pawaritmuangrach/ultrasonic01/CAR_PLAN.md

# แผนรถบังคับ — อัลตราซาวด์มองข้างหน้า

เป้าหมายปลายทาง: ติดอาเรย์อัลตราซาวด์บนรถบังคับ ให้รถ "เห็น" สิ่งกีดขวางข้างหน้า
แบบเรียลไทม์ โดยเทรน NN ด้วยกล้องเป็นครู เอกสารนี้ล็อกสถาปัตยกรรมที่ตัดสินแล้ว
และแทนแผน Stage 4-7 เดิมใน `.claude/plans/` ที่คิดไว้แบบตั้งโต๊ะ 9 ช่อง

Stage 1-2 (ยิงคลื่น + TDOA จริง sub-µs) เสร็จแล้ว ดู `README.md` §8

---

## สถาปัตยกรรมที่ล็อกแล้ว

| เรื่อง | เลือก | เพราะ |
|---|---|---|
| สมองรถ | **Raspberry Pi** (หรือคอมร่วม) | ESP32 เก็บคลื่นอย่างเดียว · Pi รัน NN + คุมมอเตอร์ · ยืดหยุ่นสุด |
| Ground truth | **Astra ติดบนรถ มองหน้า คู่กับอาเรย์** | กล้องเห็นสิ่งเดียวกับอัลตราซาวด์ = label ตรงกัน · ใช้ต่อจาก webcam project ได้เลย |
| เป้าหมายแรก | **egocentric — อะไรอยู่ข้างหน้าตอนนี้** | ทิศ+ระยะในกรวยหน้า ไม่ต้องรู้พิกัดรถ (global map ไว้ทีหลัง) |
| การเก็บข้อมูล | **พร้อมกันทุกช่อง** | รถเคลื่อนที่ → จับคู่ตามลำดับเบลอ (§8.17) |

## คุณค่าหลัก — อัลตราซาวด์เติมจุดบอดกล้อง

Astra เป็น structured light อ่านไม่ได้ในหลายกรณี (จาก webcam project README):
กระจก/แก้ว/พลาสติกใส · ผิวมันสะท้อน · จอมอนิเตอร์ · โดนแดด · **ใกล้กว่า 0.6 m**

จุดที่กล้องบอดคือจุดที่อัลตราซาวด์แข็งแรง โดยเฉพาะ <0.6 m ซึ่งเป็นระยะอันตรายที่สุด
ของรถ **กล้องเป็นครูตอนเทรน อัลตราซาวด์ทำงานตอนกล้องมองไม่เห็น** นี่คือเหตุผลของทั้งโปรเจกต์

## ตัวเลขจริงที่กำหนดขอบเขต (วัด/คำนวณแล้ว)

| | ค่า | ที่มา |
|---|---|---|
| มุมมอง | กรวยหน้า ~60° | ลำเสียง TCT40 |
| ระยะใช้ได้ | กำแพง ~2 m · ของเล็ก ~3 m · **ไม่ถึง 5-10 m** | SNR 40 dB ที่ 0.42 m + ดูดกลืน 1.2 dB/m |
| อัตราปิง | 30-50 ปิง/วิ ที่ 2-3 m | เวลาเอคโค่ไป-กลับ |
| รถขยับต่อปิง | 17-33 mm ที่ช้า | ละเอียดพอ |
| ADC หนึ่ง ESP32 | **2 ช่องพร้อมกันที่ 266 kS/s** | §8.17 (3+ ช่องยุบเหลือ 44-89 kS/s) |
| คอขวดส่งดิบ | 6-11 Mbps ที่ 30 ปิง/วิ | ดิบ 4 ช่อง — เกิน serial |

**คอขวดส่งดิบ**: เก็บ dataset ออฟไลน์ส่งช้าๆ ได้ ไม่มีปัญหา · deploy realtime ต้อง
ประมวลบน ESP32 แล้วส่งแค่ feature (Δt ต่อคู่ + envelope ย่อ) ไม่ใช่ดิบ

---

## แผ่นอาเรย์ที่ปริ้นไว้ — ใช้ตัวเดิมยาว ไม่ต้องปริ้นใหม่จนถึง Stage D

แผ่น Y-array เจาะรูเผื่อ 9 RX + 3 TX ไว้แล้ว เราใช้ทีละไม่กี่รู ไม่ต้องแก้อะไร

| Stage | ทำกับแผ่นอาเรย์ |
|---|---|
| A (2 ช่อง) | ไม่แตะ — T1 + A140 + C140 เสียบอยู่แล้ว |
| B (4 ช่อง) | แผ่นเดิม **เพิ่มหัวรับลงรู A80, C80** |
| C (ขึ้นรถ) | แผ่นเดิม + แผ่นยึดให้ติดรถได้ |
| D+ (9 ช่อง) | ค่อยตัดสินว่าปริ้นใหม่ไหม |

**4 ช่องของ Stage B เลือก A80, A140, C80, C140** (หมุนแผ่นให้ A140-C140 วางนอน =
แกนซ้าย-ขวาของรถ) ได้เบสไลน์แนวนอนสองขนาด: A140-C140 (242 mm, ทิศละเอียด) และ
A80-C80 (139 mm, ทิศหยาบไม่กำกวม) = coarse-to-fine แก้ปัญหาข้ามคาบ · TX คงที่ T1

**ของใหม่ชิ้นเดียวสำหรับ Stage A ไม่ใช่อาเรย์ แต่คือแผ่นยึดกล้อง+อาเรย์** ให้ Astra กับ
อาเรย์มองทางเดียวกันและไม่ขยับระหว่างเก็บ dataset (ไม้/อะคริลิก/พลาสวูดก็พอ ไม่ต้องแม่นมาก
NN เรียนความสัมพันธ์เอง แต่ต้องนิ่ง)

**ทำไม D+ ค่อยคิดเรื่องปริ้นใหม่** Y-array ออกแบบมาสำหรับ DOA 2 มิติบนโต๊ะ (สมมาตรทุกทิศ)
แต่รถมองหน้าอย่างเดียว เน้นซ้าย-ขวา อาจได้ประโยชน์จากอาเรย์เตี้ยกว้างและเล็กลง (ตอนนี้ 280 mm
ใหญ่สำหรับรถเล็ก) **ผล 4 ช่องจะบอกเองว่าต้องการเบสไลน์แบบไหนเพิ่ม** ออกแบบจากข้อมูลจริง
ไม่ใช่เดา

## แผน Stage ใหม่

### Stage A — ไปป์ไลน์ครบวงจร ด้วย 2 ช่องที่มีอยู่  ✅ เสร็จ (ไปป์ไลน์ครบเส้น · ระยะเรียนได้)

พิสูจน์ loop ทั้งเส้นก่อนสร้างฮาร์ดแวร์เพิ่ม **ทำบนคอมเครื่องนี้ได้เลย ไม่ต้องมี Pi
และไม่ต้องมีรถ** (Astra + OpenNI2 ติดตั้งแล้วจาก webcam project) ไม่ต้องซื้ออะไร

> **ไม่ต้องมีรถจนถึง Stage C** หนึ่งตัวอย่างเทรน = สแนปช็อตเดียวของ (คลื่น + depth)
> ณ ขณะเดียว รถไม่เกี่ยว เก็บด้วยการยึด **อาเรย์ + Astra ติดกันบนแท่น/ขาตั้งเดียว**
> หันทางเดียวกัน แล้วเลื่อนวัตถุ/ยกแท่นไปฉากต่างๆ ด้วยมือ เพราะเก็บพร้อมกันทุกช่องแล้ว
> สแนปช็อตจากแท่นนิ่งกับจากรถวิ่งจึงเหมือนกัน (Doppler ที่ 1 m/s = 0.3% ทิ้งได้)
> **ของชิ้นเดียวที่ต้องทำเพิ่มคือแผ่นยึดกล้อง+อาเรย์ให้มองสิ่งเดียวกัน** ไม่ใช่รถ

1. ตัวเก็บ dataset: อ่านอัลตราซาวด์ 2 ช่อง (ไปป์ไลน์ §8 ที่พิสูจน์แล้ว) + Astra depth
   พร้อม timestamp ให้ตรงกัน
2. เก็บชุดเล็ก: วางสิ่งกีดขวางหลายตำแหน่ง/หลายระยะในกรวยหน้า เก็บคู่ (คลื่น, depth)
3. เทรน NN จิ๋ว: คลื่น 2 ช่อง → ระยะ+ทิศของสิ่งที่อยู่ข้างหน้า (label จาก Astra)
4. **เกณฑ์ผ่าน**: NN ทำนายระยะ/ทิศได้ดีกว่าเดา และทำงานในจุดที่ Astra บอด (เอาวัตถุ
   ใกล้กว่า 0.6 m หรือกระจก มาลอง — กล้องได้ 0 แต่อัลตราซาวด์ยังเห็น)

### Stage A — ผลสรุป (2 ช่อง)

ไปป์ไลน์ครบเส้นทำงานแล้ว: เก็บ (คลื่น+depth) → สกัด feature → เทรน → วัดผลเทียบ baseline
โค้ดอยู่ใน `car/` (collect, astra, ultrasonic, features, labels, train, inspect_data)

**บทเรียนสำคัญที่วัดได้:**

| แกน | 2 ช่องทำได้ไหม | เพราะ |
|---|---|---|
| **ระยะ** | ✅ ได้ (r 0.5-0.9) | มาจากเวลาเอคโค่ตรงๆ ไม่ต้องเทียบสองช่อง `--track` พิสูจน์แล้ว 74→87, 102→117, 133→143 cm |
| **มุม** | ❌ ไม่ได้ (r~0) ตอนนั้น | **[แก้ทีหลัง]** สรุปตอนนั้นว่า "ต้องหลายเบสไลน์" — **ผิด** Stage B พบว่าเหตุจริงคือ (1) ช่อง g34 เสีย (Rf2 ผิดรู amp ต่ำ 3 เท่า) (2) อาเรย์วางบนพื้นกระเบื้องที่สะท้อน 40 kHz · พอแก้สองข้อนี้ **เบสไลน์เดียวก็วัดมุมได้** (9.4°) |

**กับดักที่เจอ (มีค่าต่อรถ):** อัลตราซาวด์เห็น "เสียงที่ดังที่สุด" ไม่ใช่ "สิ่งที่ใกล้ที่สุด"
ผนังเรียบไกล 2.4 m ดังกว่ากล่องเล็กที่ 0.8 m ทำให้ us ล็อกผนัง ไม่ใช่วัตถุ →
เพิ่มโหมด `--track` เช็คว่าวัตถุเป็นเสียงเด่นก่อนเก็บ และต้องเก็บในที่โล่ง

### Stage B — ขยายเป็น 4 ช่อง (ยังไม่ใช่ 9)  ⟵ อยู่ตรงนี้

**ฮาร์ดแวร์: ✅ เสร็จ · ระยะ+มุม: ✅ เรียนได้ทั้งคู่ · เหลือ: เก็บ dataset ชุดใหญ่ให้แม่นขึ้น**

รายละเอียดการวัดทั้งหมดอยู่ที่ [`README.md` §8.18](README.md) · ตรงนี้เก็บเฉพาะข้อสรุป

#### สถานะช่อง (วัดด้วย `collect.py --track` เป้าท่อ PVC ที่ ~80 cm)

| ช่อง | หัวรับ | เบสไลน์ | amp | |
|---|---|---|---|---|
| GPIO35 | A140 | คู่ 242 mm | 50 | ✅ |
| GPIO34 | C140 | | 81 | ✅ (เคย 17 — Rf2 เสียบผิดรู) |
| GPIO32 | A80 | คู่ 139 mm | 89 | ✅ |
| GPIO33 | C80 | | 107 | ✅ |

#### ผลการเรียนรู้ (แบ่ง train/val ตามฉาก ซื่อสัตย์)

**ชุดใหญ่ 790 ตัวอย่าง 6 ระยะ (e60-e160 ห่างละ 20 cm) หมุนทดสอบทีละฉาก:**

| | ระยะ | มุม |
|---|---|---|
| เดาค่าเฉลี่ย (baseline) | 36.3 cm | 14.8° |
| โมเดลเทรน | 13.6 cm ✓ | **11.8° ✓** |
| **ฟิสิกส์ตรงๆ (ไม่เทรน)** | **7.3 cm ✓** | — |

มุมดีที่ระยะใกล้ แย่ลงตามระยะ: **8.1° ที่ 53 cm** → 13.8° ที่ 154 cm (SNR ตก)
— ตรงกับที่รถต้องการพอดี เพราะระยะใกล้คือระยะอันตราย

> **ต้องหมุนทดสอบทีละฉาก อย่ากันฉากกลางฉากเดียว** ถ้าเก็บระยะห่างเท่าๆ กัน ค่าเฉลี่ยของ
> ฉากที่เหลือจะตรงกับฉากกลางพอดี baseline เลยแม่นเอง (ได้ 1.4 cm) ชนะยังไงก็ไม่ได้ =
> วัดผลหลอกตัวเอง

#### สี่บทเรียนที่เปลี่ยนผลจริง

1. **สภาพแวดล้อมสำคัญกว่าวงจร** — พื้นกระเบื้องสะท้อน 40 kHz กลบเป้าจนข้อมูล 3 ชุดแรก
   ใช้ไม่ได้ · ยกอาเรย์+เป้าพ้นพื้น ~50 cm และใช้**ทรงกระบอกตั้ง** (สะท้อนกลับทุกมุม
   ผลักตรงๆ ได้) แทนแผ่นเรียบ (ต้องเอียงหาเซนเซอร์ทุกตำแหน่ง ไม่งั้นเด้งหลุด)
2. **ช่องอ่อน = ฉีดสัญญาณวัดทีละสเตจ อย่าเดาแล้วเปลี่ยนของ** เดาผิดสองรอบ (หัวรับ/
   เรโซแนนซ์) เสียเวลา · ลองหัว 3 ตัว amp ไม่ขยับ = ตัดหัวออก แล้วยิงโทน 40 kHz วัดทีละ
   สเตจ เจอทันทีว่าสเตจ 2 ให้เกน ×2.3 แทน ×11
3. **T0 ผิด = bias คงที่ +13 cm** คาลิเบรตกับกล้อง 435 → 1220 µs แล้ว US ตรงกับกล้อง
   78% → 93%, MAE 20 → 9.7 cm · เพิ่ม range gate 40-250 cm กัน argmax เกาะเสียงสะท้อนใกล้
   ซึ่ง**ทำให้มุมพังไปด้วย** เพราะหน้าต่าง TDOA อิงยอดนี้
4. **แยก feature ตามเป้า** ระยะใช้เวลาเอคโค่ (8 มิติ) · มุมใช้ TDOA (6 มิติ) — รวมกัน 518 มิติ
   ทำให้ทำนายแย่กว่าเดาค่าเฉลี่ย (−134%) เพราะต่างฝ่ายเป็น noise ของอีกฝ่าย
5. **label กำกวมจากขาคนเก็บ** ขาที่ระยะพอๆ เป้าทำให้กล้องเลเบลขาแทนเป้า (`--expect-cm`
   กรองแค่ระยะจับไม่ได้) · `near_object_count>1` ข้ามเฟรมที่มีของใกล้หลายจุด — e60/d130 ติด
   27-32% แต่ตอนเก็บด้วย `--manual` เดินออกสุดติดแค่ 1-2% · train.py กรองอัตโนมัติแล้ว
6. **ช่องบนบอร์ดทดลองแผ่นที่สองมีพื้นเสียงสูงกว่า 3 เท่า** ยอดปลอมสูงกว่า 4 เท่า →
   argmax ไปเกาะยอดปลอม จับเป้าถูกแค่ 27-51% ที่ระยะ >90 cm ขณะที่ ch0 ได้ 89-100%
   **[แก้: ตอนแรกสรุปว่าเป็นเพราะสายจั๊มยาว — ผิด เปลี่ยนสายสั้นแล้วพื้นเสียงเท่าเดิม
   (9.0 → 9.0)]** เหตุผลเชิงวงจรที่ควรคิดตั้งแต่แรก: ขาออกออปแอมป์อิมพีแดนซ์ต่ำ (2.2k)
   รับ noise ยาก และ noise ที่เข้าหลังภาคขยายไม่ถูกขยายต่อ — จุดที่ไวคือ *ขาเข้า* ไม่ใช่ขาออก
   · สาเหตุจริงไล่ตัดจนเหลือ "ตัวบอร์ดทดลองเอง" (ดูตารางด้านล่าง)
7. **ใช้ "ยอดร่วม" ไม่ใช่ให้แต่ละช่องหายอดเอง** เป้าอยู่ระยะเดียว ทุกช่องจึงควรอ่านที่หน้าต่าง
   เดียวกัน — เลือกช่องที่พื้นเสียงต่ำสุดเป็นตัวชี้ยอด (`features.common_peak`) →
   **ระยะ MAE 20.6 → 7.3 cm (ถูก 57% → 94%) และมุมดีขึ้นเป็น 11.8°** เพราะหน้าต่าง TDOA
   ของคู่ที่สองเดิมอิงยอดของ ch2 ซึ่งเป็นช่องที่รบกวนสูงสุด

#### ข้อสรุปเชิงออกแบบ

> **ระยะคำนวณจากฟิสิกส์ (9.7 cm แม่นกว่าเทรน 16.7 cm) — ML มีไว้ทำ "มุม" และการแยกวัตถุ**

> **เบสไลน์ยาว (242 mm) คือตัวทำงาน** corr(มุม,TDOA) = +0.64 เทียบ 139 mm ที่ได้ −0.09 ·
> ที่กลัวว่าเบสไลน์ยาวจะกำกวมข้ามคาบ **ไม่เกิด เพราะเราหา TDOA จากเอนเวโลปไม่ใช่เฟสพาหะ
> จึงไม่มีคาบให้กำกวม** · เบสไลน์สั้นจะมีประโยชน์ตอนเปลี่ยนไปใช้เฟสพาหะเท่านั้น

#### ไล่ noise บอร์ด 2 จนจบ แล้วตัดสินใจย้ายลงไข่ปลา (ส.ค. 2026)

ช่องบนบอร์ดทดลองแผ่นที่สอง (g32/g33) พื้นเสียงสูงกว่าแผ่นแรก ~3 เท่า ทำให้ argmax ไปเกาะ
"ยอดปลอม" — จับเป้าถูกแค่ 27-51% ที่ระยะ >90 cm ขณะที่ g34 ได้ 89-100%

**ตัดผู้ต้องสงสัยออกทีละข้อด้วยการวัด** (เครื่องมือ `tools/noise_check.py` เก็บรายการไว้กันไล่ซ้ำ):

| สมมุติฐาน | วิธีตัด | ผล |
|---|---|---|
| สายจั๊มยาว | เปลี่ยนสายให้สั้น | เท่าเดิม (9.0 → 9.0) ❌ |
| คลื่นจากตัวส่ง | ปิดการยิง TX | เท่าเดิม (10.2 → 9.5) ❌ |
| EMI ความถี่เฉพาะ | ดูสเปกตรัม | แบนเรียบ สูงกว่า 3-4 เท่าทุกย่าน 0-133 kHz ❌ |
| หัวรับ/สายหัวรับ | ถอดหัวรับออก | noise **สูงขึ้น** (อินพุตลอย = เสาอากาศ) ❌ |
| ไฟ/VREF ที่ยืมข้ามบอร์ด | ดูสหสัมพันธ์ 2 ช่อง | corr −0.009 = ไม่ใช่แหล่งร่วม ❌ |
| ขา ADC ของ ESP32 | สลับสายที่ ESP32 | noise ตามวงจรไป ไม่ตามขา ❌ |
| ตัวชิป | เปลี่ยน MCP6004 ตัวใหม่ | เท่าเดิม ❌ |
| ค่าตัวต้านทาน | วัดด้วยมัลติมิเตอร์ | ตรงหมด ❌ |

> **เมื่อทุกชิ้นส่วนถูกหมดแต่ noise ยังอยู่ ผู้ต้องสงสัยที่เหลือคือ "ตัวบอร์ดทดลองเอง"**
> หน้าสัมผัสสปริงที่ต้านทานไม่คงที่ + ความจุแฝงระหว่างรางติดกัน — เปลี่ยนอะไหล่แก้ไม่ได้

**แก้ด้วยซอฟต์แวร์ไปก่อนแล้ว**: `features.common_peak` ใช้ยอดเอคโค่จาก "ช่องที่เงียบที่สุด"
เป็นหน้าต่างร่วมของทุกช่อง แทนที่จะให้แต่ละช่อง argmax เอง → **ระยะ MAE 20.6 → 7.3 cm
(ถูก 57% → 94%)** และมุมดีขึ้นเป็น 11.8°

**ตัดสินใจย้ายลงแผ่นไข่ปลา — เร็วกว่าแผนเดิม (เดิมไว้ Stage C)** เพราะแก้ 4 เรื่องพร้อมกัน:
พื้นที่ (บอร์ดทดลองเต็มแล้ว ขยายไม่ได้อีก) · noise (ผู้ต้องสงสัยที่เหลือ) · ความแมตช์ของช่อง
(บัดกรีเลย์เอาต์เดียวกันเป๊ะทุกช่อง = ปรสิตเท่ากัน) · พร้อมขึ้นรถ (รถสั่น ต้องบัดกรีอยู่แล้ว)

**ผังบัดกรีทำแล้ว 4 แผ่น** `hardware/perf_rx_layout.py` → `diagrams/perf_1..4_*.svg`
วาดตรงกับแผ่นจริง (คอลัมน์ A อยู่ขวา · เลขแถว 048 อยู่บน · ทุกรูแยกอิสระ วัดยืนยันแล้ว)
รวมวงจร VREF ที่ต้องสร้างเองบนแผ่น (ตัวแบ่ง + บัฟเฟอร์ section C) ซึ่งผังชุดแรกตกไป

**แผนแผ่น**: 9 ช่องใช้ 5 ชิป — ชิปแรก = ช่อง 1 + บัฟเฟอร์ VREF · ที่เหลือ 2 ช่อง/ชิป
**ทำช่องแรกก่อนช่องเดียว แล้ววัดเทียบทันที** ถ้าพื้นเสียงลงมาใกล้ 3-4 = ยืนยันว่าบอร์ดทดลอง
คือต้นเหตุจริง ค่อยลุยที่เหลือ (หลักเปลี่ยนทีละอย่าง แบบเดียวกับที่จับบั๊ก g34 ได้)

**MCP6024 ใช้ตอนไหน**: ใช้ซ็อกเก็ตทุกตัว จึงเปลี่ยนรุ่นทีหลังฟรี → **ช่องทดสอบใช้ MCP6004
ก่อน** (เพื่อให้เทียบกับบอร์ดทดลองได้สะอาด เปลี่ยนแค่ชนิดบอร์ดอย่างเดียว) แล้วค่อยสลับเป็น
**MCP6024 ทั้ง 5 ตัวพร้อมกัน** ตอนทำช่องที่เหลือ · เหตุผลเชิงวงจร: ที่เกน 11/สเตจ MCP6004
(GBW 1 MHz) ได้ BW 91 kHz ทำให้ 40 kHz อยู่ที่ 0.44 ของความถี่ตัด **เฟสเลื่อนตาม GBW
ของชิปแต่ละตัว = error ของ Δt ระหว่างช่อง** ส่วน MCP6024 (10 MHz) ได้ 909 kHz เฟสแทบไม่เลื่อน
(รายละเอียด `hardware/rx_frontend.md` 8.5)

#### ความคืบหน้าไข่ปลา (ล่าสุด)

| | สถานะ |
|---|---|
| ผัง 4 แผ่น | ✅ เสร็จ ตรงกับแผ่นจริง (A ขวา · แถว 048 บน) + มีตัวตรวจเส้นทับอัตโนมัติ |
| คอนเนคเตอร์ | ✅ TB1 = KF301 ไฟเข้า · H1 หัวรับ · H2 VREF ออก · H3 ไป ESP32 |
| **ESP32 ตัวที่ 2** | ✅ **แฟลช `esp32_scope` แล้ว (COM6)** ใช้กับแผ่นไข่ปลา — **ตัวเดิมคาไว้กับบอร์ดทดลอง อย่ารื้อ** เก็บไว้เทียบ noise |
| ผัง 1 (บัส+ซ็อกเก็ต) | ✅ **ผ่านครบ** · บัสไม่ช็อตกัน · ขา 4 (L33) = 3.35V · ขา 11 (O33) = 0V · บัส 3V3 = 3.35V · บัส GND = 0V — พร้อมเสียบชิป |
| ผัง 2 (VREF 1.65V) | ✅ **ผ่าน** · บัฟเฟอร์ทำงาน U30=1.60V ≈ F37=1.59V (1.59 เพราะ R ±5% — ไม่มีผล ทุกช่องดึงจากบัสเดียว) |
| ผัง 3+4 (สเตจ 1-2) | ✅ **ผ่าน DC ครบ** · H3 ขาออก = 1.611V เทียบ VREF 1.612V (ต่าง 1 mV) = ไบอาสถูกตลอด ขา 3→1→5→7→R_out |

**บทเรียนเครื่องมือ**: ESP32 อ่านได้ 0-3.3V และ**ชนเพดานที่ 3.3V พอดี** จึงไม่เหมาะวัดไฟเลี้ยง —
ใช้มัลติมิเตอร์กับผัง 1 · ESP32 เหมาะกับผัง 2 เป็นต้นไป (VREF 1.65V อยู่กลางพิสัย อ่านแม่น
และฉีดโทนวัดเกนรายสเตจได้)

**บทเรียนไล่จุดเสียบนไข่ปลา (ส.ค. 2026 — เสียเวลาหลายชั่วโมง)**

| อาการ | ความหมาย |
|---|---|
| โหนดตัวแบ่งอ่านได้ 0V ทั้งที่หัวบนมี 3.3V และขาล่างวัดได้ 10k | **มีอะไรลากโหนดลง GND** — ตรรกะบังคับ: ตัวแบ่งที่ครบวงจรอ่าน 0V ไม่ได้ |
| วัดโอห์มได้ **หลักร้อย** (150Ω) ไม่ใช่ 0Ω | **ไม่ใช่ตะกั่วช็อตเต็ม** — เป็นการแตะไม่เต็มที่/คราบฟลักซ์ที่ไหม้ (นำไฟได้ 100Ω–kΩ) |
| **ต้นเหตุจริง** | สายที่ต่อ **ขา 10** ล้นไปแตะแพด **ขา 11 (GND)** ที่อยู่ติดกันบนซ็อกเก็ต |

**บั๊กผังที่เจอระหว่างประกอบ (แก้แล้วทั้งหมด + มีตัวตรวจอัตโนมัติ)**

| # | บั๊ก | ผลที่เกิด |
|---|---|---|
| 1 | สายเข้าขาชิปวาดพาดทับตัวชิป จุดต่อถูกบัง | ต่อผิดไปขา 14 (OUTD) แทนขา 10 |
| 2 | ผัง 3 เดินสายลงคอลัมน์ F ซึ่งเป็นโหนด VREF ของผัง 2 (ผังนั้นไม่ได้วาดไว้ จึงดูว่าง) | สายพาดโหนด VREF · มุมหักลงรู GND |
| 3 | ผัง 1 บอกความยาวบัสแค่แถว 41-26 แต่ผัง 3 ใช้ถึง 44 ผัง 4 ถึง 21 | จุด GND ของผัง 4 ไม่ต่อบัส |
| 4 | ผัง 4 มีสายคนละโหนด 2 เส้นวิ่งคอลัมน์ K ห่างกัน **1 แถว** | มองเป็นเส้นเดียว → ขา 1/5/6 ถึงกันหมด → สเตจ 2 อิ่มตัว 3.34V |
| 5 | ป้ายชื่อชิปทับเส้นสายขา 7 | ขา 7 ดูเหมือนไม่ได้ต่ออะไร |

**ตัวตรวจที่เพิ่มใน `perf_panel.py`** (รันทุกครั้งที่สร้างผัง): เส้นทับกัน · **สองท่อนคนละเส้นเรียงต่อกันโดยเว้น ≤ 2 แถว** · และ `ghosts()` วาดวงประแดงบอก "รูที่ผังอื่นจองไว้แล้ว" ทุกผัง เพราะแผ่นเดียวกันแต่แยกวาด 4 ผัง

**กฎที่ได้:**
- แพดที่ติดกับขา GND/VDD ของชิป = จุดเสี่ยงช็อตที่สุด ใช้ตะกั่วน้อย ๆ และวัด `แพดนั้น ↔ GND ต้อง OL` ก่อนเสมอ
- **วัดโอห์มต้องปิดไฟเสมอ** — วัดตอนเปิดไฟได้ค่ามั่ว (เคยหลงว่าช็อตทั้งที่ไม่ช็อต)
- **วัดคาวงจรให้ค่าหลอก** (Rv1 อ่านได้ 1.5k/6k ทั้งที่เป็น 10k) จะฟันธงค่าอุปกรณ์ต้องปลดขาออกวัด
- **ESP32 ADC ใช้วัด DC แม่น ๆ ไม่ได้** — จุดเดียวกันอ่านได้ 2.055V แล้ว 1.413V ขณะมัลติมิเตอร์ได้ 1.70V ใช้ ESP32 เฉพาะงาน **AC/เทียบเกน** · ใช้มัลติมิเตอร์กับ DC
- **ขาลอยที่ต่อเข้า ADC อ่านได้ ~0.1–0.8V พร้อม noise สูง** — อย่าตีความว่าเป็นค่าจริงของวงจร (หลงมาแล้วตอนวัดบัส VREF ขณะถอดชิป ซึ่งไม่มีอะไรขับบัสเลย)

**บทเรียนผังไข่ปลา (ผัง 2)**: อาการโหนดถูกดึงลง 0 เมื่อเสียบชิป = สายอินพุต (+) ไปลง **ขา 14 (OUTD ที่ไม่ได้ใช้)** แทนขา 10 — OUTD อินพุตลอย เหวี่ยงเอาต์พุตชนขอบล่าง ลากโหนดตาม · **ต้นเหตุคือผังเรนเดอร์สายเข้าขา 10 โดยดิ่งลงทะลุตัวชิปจากด้านบน จุดต่อเลยถูกตัวชิปบัง** ผู้ใช้จึงบัดกรีผิดขา → **กฎใหม่: ผังไข่ปลา สายที่ต่อขาชิปต้อง 'โผล่ออกทางขอบชิป' ให้เห็นชัด ห้ามเดินเข้าหาขาโดยพาดผ่าน/ทับตัวชิป** (แก้ใน perf_rx_layout.py แล้ว)

#### ผลตัดสิน: ไข่ปลา vs บอร์ดทดลอง (ส.ค. 2026)

วัดด้วย ADC ตัวเดียวกัน วินาทีเดียวกัน หัวรับบนแท่น 3D ทั้งคู่ (`--pins 34,36 --samples 12000`)

| | ไม่ยิง TX | ยิง TX | crest | **ยอดปลอม** |
|---|---|---|---|---|
| บอร์ดทดลอง g34 | 3.0 | 13.1 | 12.8 | 167.0 |
| **ไข่ปลา g36** | 4.5 | **11.5** | **5.3** | **61.1** |

**สรุป: ไข่ปลาชนะในตัวชี้วัดที่สำคัญที่สุด** — ยอดปลอมน้อยกว่า 2.7 เท่า และ crest ต่ำกว่า 2.4 เท่า
(ยอดปลอมคือตัวที่ไปชนะเอคโค่จริงตอน argmax ทำให้อ่านระยะผิดทั้งที่ amp ดูปกติ)
พื้นเสียงตอนไม่ยิง TX สูงกว่าเล็กน้อย 1.5 เท่า ซึ่งอยู่ในเกณฑ์ที่ยอมรับได้ **-> เดินหน้าสร้างช่อง 2-9**

**บทเรียนที่ใหญ่ที่สุดของ Stage B**: ต่อสายกราวด์ตรงจาก H3 ขา GND ไป GND ของ ESP32 ที่อ่าน
ทำให้พื้นเสียงลดจาก 14.9 เหลือ **4.5 (3.3 เท่า)** — มากกว่าทุกอย่างที่เคยลองมาตลอดโปรเจกต์
สายสัญญาณทุกเส้นต้องมีสายกราวด์คู่เดินเคียงเสมอ (บิดเกลียวยิ่งดี) และ**เครื่องวัดเองก็เติม noise**
ช่องเดียวกันอ่านด้วย ESP32 คนละตัวได้ 24.0 กับ 14.9 -> เทียบวงจรต้องใช้ ADC ตัวเดียวกัน

#### เหลือทำใน Stage B

- เก็บ dataset ชุดใหญ่ 6 ระยะ ห่างละ 20 cm (ดู "ขั้นถัดไปทันที" ท้ายเอกสาร)
- **เกณฑ์ผ่าน**: มุมแม่นขึ้นจาก 14° ตอนทดสอบข้ามระยะ และระยะยังอยู่ระดับ ~10 cm

> ~~**ทางลัด: ไม่ต้อง master/slave** ฉากนิ่งตอนเก็บ จึงยิงสองครั้งอ่านทีละคู่ได้~~
> **เลิกใช้แล้ว (ส.ค. 2026) — ดู Stage B2** ทางลัดนี้ใช้ได้เฉพาะตอนฉากนิ่ง พอเปลี่ยนมา
> อัดต่อเนื่องกับเป้าที่เคลื่อนที่ มันพังทันที: สองรอบยิงห่างกัน ~95 ms คนเดิน 0.5 m/s
> ขยับไป 9.5 cm ซึ่งเกินหน้าต่างวิเคราะห์ (±5 cm) -> **คู่ที่สองพลาดเอคโค่โดยไม่มีอะไรเตือน**
> ตอนนี้อ่าน 4 ช่องพร้อมกันใน ESP32 ตัวเดียวด้วย bandpass sampling แทน (`car/sync4.py`)
> **master/slave ยังมีประโยชน์อยู่** ถ้าอยากได้ 266 kHz/ช่องเต็มพร้อมกันทั้ง 4 — เลื่อนไป Stage C

**1 TX + 4 RX ไม่ใช่ 3 TX + 9 RX** ขยายทีละขั้น 2→4 เพื่อให้แต่ละขั้นเป็นจุดจับปัญหา
(เหมือนที่ 2→3 ช่องทำให้เจอเพดาน ADC) กระโดดไป 9 เลยคือทำผิดซ้ำแบบสร้างใหญ่ก่อนพิสูจน์
9 RX / 3 TX เต็มรูปไว้ Stage D+ และตอนนั้นใช้ ADC ภายนอก ไม่ใช่ breadboard

- **ต่อ A80/C80 บนบอร์ดทดลองก่อน (ไม่ใช่ไข่ปลา) สำหรับทดสอบบนโต๊ะ** เพราะผู้ใช้เพิ่ง
  เคยใช้ไข่ปลาครั้งแรก การบัดกรีไข่ปลาครั้งแรก + เพิ่มช่อง พร้อมกัน = สองตัวแปร ถ้าไม่เวิร์ก
  แยกไม่ออกว่าบัดกรีพลาดหรือแนวคิดผิด — เปลี่ยนทีละอย่าง ต่อแบบเดิมที่คล่องแล้ว เสี่ยงต่ำ
  - A80 → GPIO32 · C80 → GPIO33 · ต่อเหมือน 2 ช่องเดิมเป๊ะ
- **ย้ายลงแผ่นไข่ปลาที่ Stage C (ตอนขึ้นรถ)** เมื่อแนวคิดพิสูจน์แล้วและรถสั่นจริงต้องบัดกรีอยู่ดี
  ตอนนั้นฝึกไข่ปลากับวงจรที่รู้ว่าถูกแล้ว ไม่ต้องเดาว่าปัญหาอยู่ไหน · ใส่ MCP6024 + IC socket
  ตอนนั้น · วางเลย์เอาต์ช่องละก้อนเหมือนกันเพื่อให้ปรสิตเท่ากัน (แมตช์ดีกว่า breadboard)
- TX กับ ESP32 ยังอยู่ breadboard/socket ได้ ยังไม่ต้องบัดกรี
- เฟิร์มแวร์ master/slave: ESP32 สองตัวยิง+เก็บพร้อมกัน ซิงก์ด้วยสายทริกเกอร์ร่วม +
  พัลส์ตรงในข้อมูล (ทดสอบ sync ได้ก่อนด้วย 2 ช่องปัจจุบันแยกใส่คนละบอร์ด)
- เทรนใหม่ วัดว่า 4 ช่องดีขึ้นจาก 2 ช่องแค่ไหน
- **เกณฑ์ผ่าน**: ความละเอียดทิศดีขึ้นวัดได้ และยังทำงานตอนรถขยับ

### Stage B2 — ระบบเก็บข้อมูลแบบใหม่: 4 ช่องพร้อมกัน อัดต่อเนื่อง (ส.ค. 2026) ✅

เดิมเก็บทีละช็อตด้วย `collect.py` (ฉากต้องนิ่ง กดปุ่มทีละเฟรม) เปลี่ยนเป็น **อัดต่อเนื่อง
พร้อมกล้อง depth เป็นเฉลยทุกเฟรม** และ **อ่าน 4 ช่องพร้อมกันในการยิงครั้งเดียว**

| | เดิม | **ตอนนี้** | ดีขึ้น |
|---|---|---|---|
| การยิง | 2 รอบ (อ่านทีละคู่) | **รอบเดียว ครบ 4 ช่อง** | ฐานเวลาเดียวกัน |
| คู่เบสไลน์ที่ใช้ได้ | 2 | **6** | มุมควรดีขึ้น |
| ความเร็วสาย | 921600 baud | **2,000,000 baud** | 2 เท่า |
| อัตราเก็บ | 1.3 -> 2.6 fps | **20 fps (คาบคงที่ 50 ms)** | **15 เท่า** |
| ระยะ | 258 cm | **200 cm** | พอดีกับสีกล้อง |
| กล้อง depth | 640x480 | **320x240 @ 30 fps** (เก็บ 15 fps) | ไฟล์เล็กลง 4 เท่า |
| ความเหลื่อมกล้อง-เซ็นเซอร์ | — | **33 ms** (วัดจริง) | |

#### กุญแจ 3 อย่างที่ทำให้เป็นไปได้

**1. เพิ่ม baud เป็น 2 Mbaud** — เฟรมส่งเป็นไบนารีอยู่แล้ว คอขวดคือความเร็วสายล้วน ๆ
แก้ `Serial.begin()` ค่าเดียวในเฟิร์มแวร์ + `car/ultrasonic.py: BAUD` ให้ตรงกัน
**เฟรมเสีย 0 และข้อมูลเหมือนเดิมทุกอย่าง** (ตรวจแล้ว: อัตราสุ่ม/skew/ค่าเฉลี่ยดิบ ตรงกับ npz เก่า)
สำรองไฟล์เดิมที่ `esp32_scope.ino.bak921600`

**2. bandpass sampling** — ADC ของ ESP32 มีตัวแปลงตัวเดียว อัตรารวมตันที่ ~266 kHz
**ไม่ว่าจะขอเท่าไหร่** (วัดที่ f = 0.5/0.8/1.0/1.2/1.6/2.0 MHz ได้ 62-66 kHz/ช่องเท่ากันหมด)
4 ช่องจึงได้ 66 kHz/ช่อง ซึ่งต่ำกว่า Nyquist ของ 40 kHz -> **40 kHz พับลงมาที่ 26.4 kHz
ซึ่งอยู่ใต้ Nyquist 33.2 kHz** สัญญาณเราเป็นแถบแคบ การพับจึงเป็นแค่การเลื่อนย่าน
เปลือกคลื่นและ TDOA อยู่ครบ · `features.signal_band(rate)` เลือกย่านกรองให้อัตโนมัติ
ราคาที่จ่าย: ความละเอียดเวลา 3.76 -> 15 us (~2.1 องศา ยังต่ำกว่าความผิดพลาดจริง 11.8 องศา)

**3. ตัดดีเลย์รอ ADC สลับช่อง** — เดิมหน่วง 0.2 วิทุกครั้ง วัดที่ 0.20/0.08/0.03/0.00
ได้ 1.3/1.8/2.2/**2.6** fps โดย**เฟรมเสีย 0 ทุกค่า** = เป็นการรอเปล่า ๆ ล้วน

#### เพดานที่เหลือ (วัด/คำนวณแล้ว)

```
เวลาต่อ 1 ping = เก็บ ADC (13.1 ms) + ส่งข้อมูล (34.8 ms) = 47.9 ms
คาบที่ตั้ง 50 ms -> เหลือระยะขอบ 2.1 ms
เสียงไปกลับที่ 200 cm ต้องการ 11.7 ms -> ห่างจากคาบ 4 เท่า ปลอดภัยมาก
```

**84% ของเวลาหมดไปกับการส่งข้อมูล ไม่ใช่การวัด** — ถ้าอยากเร็วกว่านี้: ดัน baud เป็น
4 Mbaud (คาบ 26.7 ms = 37 fps) · แพ็ก 12 บิตแทน 16 (+25%) · หรือใช้ ESP32 สองตัวขนานกัน
**5 ms ทำไม่ได้** — ต่อให้ลดระยะเหลือ 50 cm และดัน 4 Mbaud ก็ยังได้แค่ 13.2 ms

#### หลักที่ยึดในระบบใหม่

- **ไม่กรองอะไรตอนเก็บ** บันทึกทุกเฟรมพร้อมค่าคุณภาพ (`cam_near_cm`, `depth_valid`)
  ติดไปในไฟล์ **คัดตอนเทรนแทน** — คัดตอนเก็บคือทิ้งแล้วทิ้งเลย คัดตอนเทรนเปลี่ยนใจได้
- **หน้าจอแสดงข้อมูลดิบล้วน** แกนตั้งตรึง 0-4095 ไม่ปรับสเกล ไม่กรอง ไม่หาเปลือกคลื่น
  ไม่คำนวณ SNR/ระยะ — สิ่งที่เห็น = สิ่งที่บันทึกเป๊ะ ๆ (สเกลอัตโนมัติเคยหลอกตาว่าทุกช่อง
  แรงเท่ากัน ทั้งที่จริงต่างกัน 3 เท่า และมองไม่ออกว่าเหลือเฮดรูมเท่าไหร่)
- **แบ่ง train/test ตามช่วงเวลา ไม่ใช่สุ่มทีละเฟรม** เฟรมติดกันแทบเหมือนกัน สุ่มแบ่งแล้ว
  เพื่อนบ้านของเฟรมทดสอบไปอยู่ในชุดเทรน = โมเดลเคยเห็นคำตอบ (เคยเจอ baseline 1.4 cm)

#### เครื่องมือชุดใหม่

| ไฟล์ | ทำอะไร |
|---|---|
| `car/sync4.py` | อ่าน 4 ช่องพร้อมกัน คาบคงที่ · รันเดี่ยว ๆ เพื่อวัดความเร็ว/คุณภาพ |
| `car/record.py` | อัดต่อเนื่องเป็นช่วง ๆ (`--start N` แยกรันทีละช่วงได้) |
| `car/check.py` | ตรวจระบบทุกเมื่อ ไม่บันทึกอะไร ใช้ก่อนอัดทุกครั้ง |
| `car/view.py` | หน้าจอกลางที่ใช้ร่วมกัน — depth + คลื่นดิบ + กราฟประวัติแบบเลื่อน |
| `car/train_sections.py` | เทรน 3 ช่วง ทดสอบ 1 ช่วง + เทียบวิธีหายอด + แยกผลตาม SNR |
| `car/live.py` / `live2.py` | ดูสด: แผนที่ 2D จุดเดียว / กลุ่มจุดทุกเอคโค่ |
| `tools/noise_spectrum.py` | แยกว่าเสียงรบกวนอยู่ย่านไหน (ฮัม/เสียง/เกินย่าน) |
| `explain_car.md` | อธิบายวงจรทีละภาค ตั้งแต่สั่งยิงจนได้ระยะ+มุม |

#### บั๊กที่เจอและแก้ระหว่างทาง

| บั๊ก | ผล | แก้ |
|---|---|---|
| `os._exit(0)` ใน finally | **กลืน traceback ทั้งหมด** โปรแกรมตายเงียบ ไล่หาสาเหตุไม่ได้ | ดักและพิมพ์ error ก่อนจบ |
| numpy FFT ทำงานพร้อม OpenNI คนละเธรด | heap corruption 0xc0000374 | ซ้อมเส้นทางคำนวณ+วาดภาพให้ครบ **ก่อนเปิดกล้อง** ด้วยรูปร่างข้อมูลจริง |
| แผงแสดงผลใน `record.py` หายจากการแก้รอบก่อน | อัดโดยไม่เห็นอะไรเลย | ใส่กลับ + ต่อกราฟประวัติ |
| กรองความยาว feature ผิด (รวมชุดระยะกับมุมเข้าเซ็ตเดียว) | ข้ามตัวอย่างทั้งหมด | หาความยาวมาตรฐานแยกต่อชุด |

#### เป้าที่เป็น "คนเดิน" — สิ่งที่ต้องระวัง

วัดจริง 1 นาที (154 ตัวอย่าง): ระยะจากฟิสิกส์ผิดเฉลี่ย **27.4 cm** (ท่อ PVC ได้ 7.3 cm)
และผิดพลาดสัมพันธ์กับความแรงสัญญาณโดยตรง:

| SNR ของยอด | ผิดเฉลี่ย | ตรงใน 20 cm |
|---|---|---|
| 3.1-5.2 (อ่อน) | 47.8 cm | 31% |
| 8.2-25.5 (แรง) | **10.2 cm** | **87%** |

เสื้อผ้าดูดซับ 40 kHz ได้ดีมากและตัวคนเป็นผิวโค้งนุ่ม สะท้อนกระจัดกระจาย
-> ถือแผ่นแข็งไว้หน้าตัวจะได้สัญญาณที่เชื่อถือได้กว่ามาก (ยังเป็น "คนเดิน" อยู่)

### Stage B+ — MIMO: เพิ่ม TX เป็น 3 ตัว (ทำก่อนขึ้นรถ)

**ทำไมคุ้มเป็นพิเศษกับข้อจำกัดของเรา: TX ถูก RX แพง**

| เพิ่ม 1 ช่อง | ต้นทุน |
|---|---|
| RX | ออปแอมป์ 2 สเตจ + R/C ครบชุด + **ช่อง ADC** ซึ่งเราชนเพดานแล้ว (README §8.17: ตั้งแต่ 3 ช่องเหลือ 267 kHz รวม ต้องยิงสองครั้งทีละคู่อยู่แล้ว) |
| **TX** | **74HCT04 1 ตัว + GPIO 1 ขา** ไม่มีภาครับ ไม่กิน ADC เลย |

3 TX × 4 RX = **12 เส้นทาง โดยไม่แตะคอขวด ADC** — นี่คือเหตุผลที่แข็งที่สุด

**ต้องเป็น time-division (TDM) ไม่ใช่ code-division**

| แบบ | ใช้ได้ | เหตุผล |
|---|---|---|
| Code-division (ยิงพร้อมกัน แยกด้วยรหัส Golay/Hadamard ตามแผนเดิม §7) | ❌ | หัวแบนด์แคบ ~4 kHz → ผลคูณเวลา×แบนด์วิดท์ ได้แค่ ~4-8 แยกรหัสไม่ออก เอคโค่แรงของ TX ตัวหนึ่งจะกลบเอคโค่อ่อนของอีกตัว (ข้อจำกัดเดียวกับ FM chirp ด้านล่าง) |
| **TDM: ยิง TX1 ฟัง → TX2 ฟัง → TX3 ฟัง** | ✅ | แยกได้สมบูรณ์ 100% ไม่ต้องออกแบบรหัสเลย แลกกับเวลา 3 เท่า (ตอนเก็บ dataset ฉากนิ่ง = ของฟรี) |

**กำไรจริง 3 อย่าง**

1. **แก้ปัญหาผิวสะท้อนหลุด — ตัวที่ทำ dataset 3 ชุดแรกเสีย** TX คนละตำแหน่ง = ส่องวัตถุ
   คนละมุม ผิวเรียบที่สะท้อนหนีจาก TX1 อาจสะท้อนกลับเข้า TX2 · บนโต๊ะเราหลบด้วยท่อกลมได้
   **แต่ห้องจริงที่รถต้องวิ่งมีแต่ผนัง ประตู หน้ากล่อง = ผิวเรียบทั้งนั้น** ข้อนี้สำคัญที่สุดตอนขึ้นรถ
2. เส้นทางเพิ่ม 4 → 12 และ TX แต่ละตำแหน่งให้ความสัมพันธ์ Δt-กับ-มุม **ต่างกัน** =
   ได้สมการอิสระเพิ่ม ไม่ใช่แค่ SNR ดีขึ้น
3. รูรับเสมือน: จุดเฟสของคู่ TX-RX อยู่กึ่งกลาง → 12 ตำแหน่งเสมือน จากตัวจริงแค่ 7 ตัว

**ราคาที่ต้องจ่าย**

- **เวลาต่อการวัด ×3** — บนรถ 3 TX × ~15 ms = 45 ms/สแกน ที่ 1 m/s รถเคลื่อน 5 cm
  ระหว่างสแกน ยอมรับได้ที่ความเร็วต่ำ แต่เป็นงบที่ต้องคิดตอนออกแบบ Stage C
- **มิติ feature เพิ่ม → เสี่ยง overfit** (เจอมาแล้วกับ 518 มิติ) แก้ด้วย feature ฟิสิกส์กระชับ:
  3 TX × 2 คู่ = 6 ค่า TDOA + 12 ค่าระยะ ยังเล็กอยู่
- **เปลี่ยนผัง TX = dataset เก่าใช้ร่วมกันไม่ได้** (เรขาคณิตเปลี่ยน)

**ลำดับที่ตกลงกันไว้**: เก็บ dataset 1 TX ให้จบก่อน แล้วค่อยเพิ่ม TX — เพราะ (ก) ได้ตัวเลขฐาน
ไว้เทียบว่า MIMO ทำให้มุมดีขึ้นกี่องศาจริงๆ ไม่ใช่เดา (ข) ยึดหลัก **เปลี่ยนทีละอย่าง** ซึ่งเป็น
สิ่งที่ทำให้จับบั๊ก g34 (Rf2 ผิดรู) ได้

**ของที่ต้องใช้ มีแล้วตาม BOM**: 74HCT04 ×2 (ซื้อไว้ 4) · หัวส่ง TCT40 ×2 (เหลือเยอะ) ·
GPIO 2 ขา · งานเฟิร์มแวร์: เลือก TX ที่จะยิงต่อเบิร์สต์ แล้ววนเก็บ TX×คู่RX

### Stage C — ยกขึ้นรถ เดินจริง

- ย้ายสมองไป Raspberry Pi · ประมวลบน ESP32 ส่งแค่ feature (แก้คอขวด)
- inference realtime บน Pi → สั่งหลบสิ่งกีดขวาง
- **เกณฑ์ผ่าน**: รถวิ่งแล้วหยุด/เลี้ยงหลบสิ่งกีดขวางข้างหน้าได้ รวมถึงของที่กล้องมองไม่เห็น

### Stage D+ — ถ้าต้องการมากกว่านี้

- ช่องเพิ่มเป็น 6-9 ด้วย ADC ภายนอก simultaneous-sampling (บอร์ดเดียว สมองเดียว)
  ไม่ใช่ 5 ESP32
- (MIMO 3 TX ย้ายขึ้นไปเป็น **Stage B+** แล้ว — ทำก่อนขึ้นรถ เพราะแก้ปัญหาผิวสะท้อน)
- global map: เพิ่ม odometry (encoder ล้อ/IMU) สะสมเป็นแผนที่ห้อง

#### FM chirp แบบค้างคาว — อัปเกรดที่รู้ว่าคุ้ม แต่รอจังหวะ

ค้างคาวที่ล่าในที่รก (ใบไม้/กิ่งไม้) ใช้คลื่นแบบ **FM ไล่ความถี่** เพื่อดูรายละเอียด
ซึ่งเป็นสถานการณ์เดียวกับรถในห้องที่ของเยอะเป๊ะ ตอนนี้เราใช้เบิร์สต์ความถี่คงที่
40 kHz — chirp เป็นทางที่พิจารณาแล้วว่าคุ้ม แต่ยังไม่ทำเพราะยังไม่มีของพื้นฐาน (4 ช่อง)

**กำแพงเชิงฮาร์ดแวร์ที่ต้องรู้ก่อน**: หัว TCT40 เป็นเรโซเนเตอร์ Q สูง (วัดเองได้ Q~20)
มันดังเฉพาะ ~39-42 kHz ต่อให้สั่งไล่ 20-40 kHz หัวจะเงียบช่วง 20-38 kHz —
**แบนด์วิดท์ที่ปล่อยได้จริง ~4 kHz ไม่ใช่ 20 kHz** ค้างคาวทำได้เพราะกล่องเสียงกว้าง
หัวเราแคบ ลอกด้วยซอฟต์แวร์ไม่ได้

| | แบนด์วิดท์ | ความละเอียดระยะ = c/2B |
|---|---|---|
| ค้างคาว FM | 20 kHz | 0.9 cm |
| หัว TCT40 ปล่อยได้จริง | ~4 kHz | 4.3 cm |
| เบิร์สต์คงที่ตอนนี้ | ~2 kHz | 6.9 cm |

**กำไรที่ได้จริงสองอย่าง:**
1. ความละเอียดระยะ 4.3 vs 6.9 cm — ดีขึ้นเล็กน้อย (หัวจำกัดเพดานไว้ที่ ~4 cm)
2. **pulse compression** — ไล่ความถี่แคบแต่ยิงยาว แล้วบีบให้คมตอนประมวลผล ได้พลังงาน
   เยอะโดยไม่เสียความละเอียด: ยิง 2 ms → +9 dB, ยิง 5 ms → +13 dB (เห็นไกลขึ้น ~5 เท่า
   หรือเห็นของอ่อนกว่าเดิม 20 เท่า) **อันนี้คือกำไรตัวจริงสำหรับรถที่อยากเห็นไกลขึ้น**
3. สำหรับ NN: รูปคลื่นมีโครงสร้างมากขึ้น อาจช่วยแยกของหลายชิ้นที่ซ้อนกัน

**ทำได้ถูกและง่ายเมื่อถึงเวลา**: เฟิร์มแวร์แค่ไล่ `g_burst_hz` ระหว่างเบิร์สต์ (LEDC ทำได้)
ประมวลผลใช้ matched filter ที่มีอยู่แล้วใน `tools/matched.py`

**เงื่อนไขที่ควรเริ่มทำ**: หลัง 4 ช่องทำงาน **และ** พบว่าการแยกของหลายชิ้นหรือระยะ
เป็นคอขวดจริง — แล้วทำ A/B: เก็บฉากเดียวกันด้วยเบิร์สต์ vs chirp วัดว่า NN ทำนายดีขึ้นไหม
ถ้าดีขึ้นจริงค่อยเปลี่ยน (อย่าเปลี่ยนเพราะทฤษฎีสวย — วัดก่อน)

---

## ขั้นถัดไปทันที

1. **ตรวจระบบก่อนอัด** — `python car/check.py --port COM5`
   ดู: depth valid > 40% · ค่า min-max ของแต่ละช่องไม่ชนขอบ 0/4095 · กราฟประวัติขยับตอนมีของเข้ามา
2. **อัด dataset 4 ช่วง ช่วงละ 5 นาที** (แยกรันทีละช่วงเพื่อพักและควบคุมจังหวะเอง)
   ```
   python car/record.py --port COM5 --name walk --sections 1 --start 1 --minutes 5
   ```
   ที่ 20 fps จะได้ **~6,000 ตัวอย่าง** = 4 เท่าของชุดเดิม (1,544)
3. **เทรน** — `python car/train_sections.py --name walk --keep-multi`
   รายงาน 4 ส่วน: ผลตามที่ขอ (เทรน s1-s3 ทดสอบ s4) · หมุนทุกช่วง · เทียบวิธีหายอด ·
   **แยกผลตามความแรงเอคโค่** (จะบอกได้ว่าเฟรมที่สัญญาณอ่อนกระทบผลแค่ไหน)
4. **สิ่งที่ยังไม่ได้ยืนยันและควรทำ**
   - **T0 = 1220 us ยังไม่ได้คาลิเบรตใหม่** สำหรับโหมด 4 ช่อง/66 kHz — ในทางทฤษฎีไม่ควร
     เปลี่ยน (ตัวกรอง zero-phase ไม่เพิ่มหน่วง ชุดยิงยาวเท่าเดิม) แต่ต้องเทียบกับกล้องก่อนเชื่อ
   - **วัดสหสัมพันธ์ระหว่าง 4 ช่องด้วยตัวเลข** ยืนยันว่าทั้ง 4 เห็นเป้าเดียวกันจริง
   - **คาบ 50 ms คงที่จริงไหม** วัดค่ากลาง/ค่าแกว่ง/ช่วงต่ำสุด-สูงสุด
   - ทั้งสามข้อรันได้ทันทีเมื่อ COM5 ว่าง (ต้องปิด `check.py` ก่อน — พอร์ตเปิดซ้อนไม่ได้)

## ผลกฎ rule base กับชุด walk 5 ช่วง (25 ส.ค. 2026)

เก็บครบ 5 ช่วง ช่วงละ ~1 นาที **4,325 เฟรม** (ยืนซ้ายสุด/กลาง/ขวาสุด อย่างละ 10 วินาที
ในช่วงเดียวกัน เห็นการเดินเปลี่ยนตำแหน่งด้วย) กันช่วงที่ 1 ไว้ทดสอบ เทรนด้วยช่วง 2-5

### ปัญหาที่เจอก่อน: **เฉลยจากกล้องพัง ไม่ใช่เซ็นเซอร์พัง**

เฉลยเดิมใช้ `depth_to_profile` แบ่งภาพเป็น 9 ช่องมุมแล้วเอา `argmin` ของช่องที่ใกล้สุด
คนที่ยืนห่าง 60 cm **กินภาพ 5-7 ช่องมุมที่ระยะเท่ากันหมด** ต่างกันแค่ 1-3 cm ตาม
ความโค้งของลำตัว `argmin` จึงเลือกช่องแบบสุ่ม ได้เฉลยเด้ง ±26 องศาทั้งที่ยืนนิ่ง

| | เฉลยเดิม (argmin ช่องใกล้สุด) | เฉลยใหม่ (`labels.target_angle`) |
|---|---|---|
| สหสัมพันธ์กับความแรง | **−0.37** (กลับด้าน) | **+0.65** |
| ทายโซนถูก | 35% (เดาได้ 47% — **แพ้การเดา**) | 82% (เดาได้ 50%) |

`target_angle` หาก้อนเป้า (พิกเซลที่ลึกใกล้เคียงตัวใกล้สุด ±40 cm) แล้วเอา
**จุดศูนย์กลางตามคอลัมน์** เฉลี่ยทั้งลำตัวจึงไม่มีปัญหานี้

### ฟีเจอร์ที่เลือก และเหตุผลที่วัดมา

เทียบบนชุดเดียวกัน (เทรน s2-s5 · ทดสอบ s1) หน่วยเป็น MAE องศา ยิ่งน้อยยิ่งดี:

| ฟีเจอร์ | ยอด ≥0 mV | ≥80 mV | ≥250 mV |
|---|---|---|---|
| `(a−b)/(a+b)` คู่นอกอย่างเดียว | 8.43 | 7.15 | 6.33 |
| `(a−b)/(a+b)` ทั้ง 4 ช่อง | 7.61 | 6.47 | 5.61 |
| **`ln` อัตราส่วน ทั้ง 4 ช่อง (log4)** | **7.40** | **6.23** | **5.28** |

`ln` ชนะเพราะ beam pattern ของหัวรับเป็น **ตัวคูณ** `ln` ของอัตราส่วนจึงแปรตามมุม
แบบเส้นตรง ส่วน `(a−b)/(a+b)` อิ่มตัวที่ ±1 แล้วบีบช่วงปลายทิ้ง

**เกลี่ยด้วยมัธยฐาน 9 เฟรม (0.6 วินาที)** — เอคโค่จากคนเป็น specular ขยับตัวนิดเดียว
ความแรงเปลี่ยน 40 เท่า (วัดจริง 28 mV ถึง 1173 mV ที่ระยะเท่ากัน) เกลี่ยแล้ว
MAE 6.2 → **4.8 องศา** สหสัมพันธ์ 0.65 → **0.80** หน่วงคำตอบ 0.3 วินาที

### ผลไขว้ทั้ง 5 ช่วง (กันทีละช่วง)

| กันช่วง | เฟรมทดสอบ | MAE องศา | เดาได้ | ทายโซนถูก | เดาโซน | **สลับซ้าย↔ขวา** |
|---|---|---|---|---|---|---|
| s1 | 769 | **4.8** | 8.6 | **82%** | 50% | 0.0% |
| s2 | 634 | **4.5** | 7.7 | **88%** | 61% | 0.0% |
| s3 | 654 | **5.0** | 9.6 | **86%** | 57% | 0.0% |
| s4 | 637 | **6.0** | 9.1 | **76%** | 56% | 0.0% |
| s5 | 715 | **6.2** | 10.2 | **73%** | 48% | 0.4% |

**ไม่เคยสลับซ้ายเป็นขวา** (ผิดข้ามสุดขั้ว 3 เฟรมจาก 3,409) ซึ่งเป็นความผิดพลาดชนิดที่
อันตรายที่สุดสำหรับรถหลบสิ่งกีดขวาง

### ตารางตรวจสาย — ยืนยันว่าต่อถูกด้าน

ความแรงมัธยฐาน mV แยกตามมุมกล้อง (+ = เป้าอยู่ทางขวาของภาพ):

| มุม | เฟรม | FAR LEFT (34) | LEFT (33) | RIGHT (32) | FAR RIGHT (35) |
|---|---|---|---|---|---|
| −24° | 692 | 46 | 64 | **179** | **217** |
| −16° | 239 | 111 | 123 | **265** | **277** |
| −8° | 714 | **248** | 214 | 193 | 224 |
| 0° | 1127 | **268** | 207 | 184 | 206 |
| +8° | 274 | **211** | 171 | 68 | 67 |
| +16° | 357 | **154** | 116 | 57 | 59 |
| พื้นเสียงรบกวน | | 11.0 | 10.2 | 12.1 | 8.2 |

ไล่จากซ้ายไปขวาแบบ **โมโนโทน** ทั้ง 4 ช่อง และช่องคู่ตรงข้ามสลับกันตรงกลางพอดี
→ วงจรทั้ง 4 ช่องทำงานถูกต้อง เกนใกล้เคียงกัน (พื้นเสียง 8-12 mV เท่ากันหมด)

**การจับคู่กับกล้อง: ภาพฝั่งซ้าย ↔ GPIO 32/35 · ภาพฝั่งขวา ↔ GPIO 34/33**
(กล้องหันเข้าหาเป้า ภาพจึงกลับด้านกับชื่อที่ตั้งจากมุมมองของรถ — ถูกต้องตามฟิสิกส์)

### ทดลองยืนดูผลสด — `car/predict.py`

`rules.py` เก็บกฎที่ฟิตแล้วไว้ที่ `car/data/_walk_rule.json` (เทรนซ้ำด้วยทุกช่วง
3,409 เฟรม: **มุม = +9.68 × log4 − 4.75**) แล้ว `predict.py` โหลดไปใช้สด ๆ

- **เกลี่ยแบบย้อนหลังล้วน** ไม่แอบใช้เฟรมอนาคตเหมือนตอนวัดผลออฟไลน์
  วัดเทียบแล้วผลเท่ากัน (MAE 5.28 เทียบกับ 5.30 องศา) แต่ใช้บนรถได้จริง
- **เอคโค่วูบไม่ทำให้หยุดตอบ** เฟรมที่อ่อนกว่า 80 mV ไม่ถูกใส่บัฟเฟอร์ แต่ยังคืนคำตอบเดิม
  พร้อมป้าย `ECHO TOO WEAK` และนับจำนวนเฟรมที่ค้าง
- เล่นข้อมูลเก่าย้อนกลับผ่านเส้นทางเดียวกันได้ **โซนถูก 82% · ผิด 4.7 องศา**
  ตรงกับผลออฟไลน์ (82% · 4.8 องศา) → เส้นทางสดกับเส้นทางวัดผลตรงกันจริง
- วาดภาพได้ 64 fps จึงไม่เป็นคอขวด (เซ็นเซอร์ 15-20 fps)

### ข้อจำกัดที่ยังเหลือ

1. **ระยะยังประเมินไม่ได้จากชุดนี้** ผู้เก็บยืนที่ระยะเดียวเกือบตลอด (กล้อง 44-102 cm
   แต่ sd แค่ **5.8 cm**) ไม่มีการแปรผันให้วัด · เสียงอ่านได้ต่ำกว่ากล้อง **11.4 cm**
   อย่างเป็นระบบ (ฮิสโทแกรมเป็นก้อนเดียวเรียบ ไม่ใช่ล็อกวัตถุอื่น — เป็นอคติคงที่)
   **ต้องเก็บชุดคาลิเบรตระยะแยก**: ยืนนิ่งที่ 60 / 100 / 140 / 180 cm อย่างละ 20 วินาที
   แล้วค่อยฟิต T0 กับความชัน — ตอนนี้ยัง**ไม่ควรแก้ T0** เพราะช่วงระยะแคบเกินจะเชื่อได้
2. **โซนขวาแม่นน้อยกว่าโซนซ้าย** (59% เทียบกับ 85%) เพราะเอคโค่ฝั่งขวาอ่อนกว่า
   (57-68 mV เทียบกับ 179-217 mV) และเฟรมน้อยกว่า — เก็บเพิ่มฝั่งขวาจะช่วยได้
3. ทิ้งไป 21% ของเฟรม (782 เฟรมเสียงอ่อนกว่า 80 mV · 134 เฟรมเป้าเกือบหลุดภาพ)

## แผงทดลองเล็ก 150×150 มม. (25 ส.ค. 2026)

พิมพ์แผงเล็กมาลองก่อน แทนที่จะรอบัดกรีครบ 12 ช่องของแผงเต็ม — ใช้ **RX 4 + TX 1**
ซึ่งเท่ากับที่วงจรบนไข่ปลารองรับอยู่ตอนนี้พอดี พิมพ์ชิ้นเดียว ไม่ต้องแบ่งชิ้น

สเปกเต็ม: [`hardware/plate_mini_spec.md`](hardware/plate_mini_spec.md) ·
โมเดล: [`hardware/plate_mini_model.py`](hardware/plate_mini_model.py) ·
ไฟล์พิมพ์: `hardware/cad/plate_mini.stl`

| | ค่า |
|---|---|
| แผ่น | 150 × 150 × 4 มม. มุมลบ R12 |
| RX 4 ตัว | มุมทั้งสี่ที่ (±55, ±55) — **เบสไลน์ 110 มม.** ทั้งแนวนอนและแนวตั้ง |
| TX 1 ตัว | กึ่งกลาง (0, 0) |
| รูเซ็นเซอร์ | **⌀20.5** (ของเดิม 19.5 + 1.0 ตามที่ขอ) · บอส ⌀24 สูง 10 |
| ร่องตัดเสียง | 4 ร่อง 3 × 30 มม. ขวางแนว TX→RX ทุกเส้นทาง |
| GPIO | TL=34 · BL=33 · BR=32 · TR=35 · TX=18 |

**การจับคู่ GPIO เลือกให้ `car/rules.py` ใช้ต่อได้เลย** — สูตร
`log4 = ln((a34+a33+1)/(a32+a35+1))` คือการเทียบผลรวมฝั่งซ้ายกับฝั่งขวา
ตราบใดที่ (34,33) อยู่ซ้ายและ (32,35) อยู่ขวา โค้ดไม่ต้องแก้ ฟิตใหม่แค่ 2 ค่า

**ของแถม**: RX วางเป็นสี่เหลี่ยมทำให้ได้ทิศ *แนวตั้ง* มาด้วย
`ln((a34+a35+1)/(a33+a32+1))` — อาเรย์เส้นตรงเดิมบอกไม่ได้เลย

**รูโตขึ้น 1 มม. ดีกว่าเดิมจริง ไม่ใช่แค่ใส่ง่าย**: โอริงที่ถูกอัดจนแบนนำเสียงได้มากขึ้น
ซึ่งผิดวัตถุประสงค์ของมัน — โอริงมีไว้ *กั้น* เสียงไม่ให้ลัดผ่านเนื้อพลาสติก

### โมเดล PolarScan (นิวรัลเน็ต 13 ช่องมุม)

อธิบายการเทรนทีละขั้น: [`explain_polar_model.md`](explain_polar_model.md) —
ครอบคลุมขั้น DSP, เฉลยจากกล้อง, สถาปัตยกรรม, ฟังก์ชันสูญเสีย, การแบ่งข้อมูล
และผลจริงพร้อมเส้นฐานที่ควรเทียบ · ดูผลสด: `python car/live_polar.py --replay walk_s5`

### โมเดล ML ล้วนจากคลื่นดิบ — `car/train_nn.py` (26 ส.ค. 2026)

ป้อน `counts[4x871]` ดิบเข้า CNN ตรง ๆ **ไม่ผ่าน DSP ที่เขียนมือเลย** เน็ตเรียนรู้
การกรองแบนด์ หาเปลือกคลื่น เทียบความแรงระหว่างช่อง เองทั้งหมด · 142,721 พารามิเตอร์

**ผลรันไขว้ครบ 5 ช่วง** (กันทีละช่วงไว้ทดสอบ · เฉลยเดียวกับ rules.py):

| กันช่วง | ML ล้วน | เดามั่ว | ทายโซนถูก |
|---|---|---|---|
| s1 | 3.11° | 10.07° | 88% |
| s2 | 3.47° | 8.17° | 87% |
| s3 | 3.68° | 10.08° | 92% |
| s4 | 3.92° | 10.05° | 87% |
| s5 | 4.42° | 10.60° | 87% |
| **เฉลี่ย** | **3.72°** | 9.79° | **88%** |

| วิธี | MAE เฉลี่ย | ทายโซน | พารามิเตอร์ |
|---|---|---|---|
| เดาค่าเฉลี่ย | 9.79° | 47% | 0 |
| `rules.py` (ความแรง + เส้นตรง) | 4.80° | 82% | **2** |
| **`train_nn.py` (คลื่นดิบ → CNN)** | **3.72°** | **88%** | 142,721 |

**ดีขึ้นจาก rules.py 23%** และนิ่งทุกช่วง (3.11–4.42°) ไม่ใช่ความบังเอิญของการแบ่ง

สถาปัตยกรรมออกแบบตามฟิสิกส์: **ลำตัวคอนโวลูชันร่วมทั้ง 4 ช่อง** (หัวรับชนิดเดียวกัน
เอคโค่หน้าตาเหมือนกัน) แล้วค่อยรวมช่องเพื่อเทียบกัน · **นอร์มัลไลซ์ด้วยค่ากลาง+MAD
แต่เก็บสเกลเดิมป้อนแยก** เพราะความแรงสัมพัทธ์ระหว่างช่องคือข้อมูลบอกทิศทั้งหมด
ถ้านอร์มัลไลซ์ทิ้งไปเฉย ๆ จะทิ้งสัญญาณที่ rules.py ใช้

**ดูผลได้ทั้งสองหน้าจอเดิม** โดยเติม `--model nn` ไม่ต้องมีไฟล์ใหม่:

```bash
python car/predict.py --port COM5 --model nn      # สด
python car/replay.py  --section 5 --model nn      # เล่นย้อน (s5 = ช่วงที่โมเดลกันไว้)
```

หน้าจอขึ้นป้ายบอกเองว่ากำลังดูชุดไหน — เขียว `TEST SECTION` ถ้าเป็นช่วงที่โมเดลไม่เคยเห็น
เหลือง `TRAINED ON THIS` ถ้าอยู่ในชุดเทรน (ตัวเลขจะดีเกินจริง)

**เกลี่ยตามเวลาช่วย NN ด้วย** ทั้งที่เทรนแบบทีละเฟรม:

| เกลี่ย | MAE | ทายโซน |
|---|---|---|
| 1 เฟรม | 4.42° | 87% |
| **9 เฟรม** (ค่าเริ่มต้น) | **3.82°** | **93%** |
| 21 เฟรม | 3.73° | 95% |

เทียบบนช่วง s5 เดียวกัน: **NN 3.7° / โซน 94%** · rules.py 5.9° / 75%
(rules.py เคยเห็น s5 ตอนเทรนด้วยซ้ำ แต่ยังแพ้)

**ผลจากการเล่นย้อนตรงกับตอนเทรน** (3.7° เทียบ 3.82°) ยืนยันว่าเส้นทางที่ใช้จริง
กับเส้นทางที่วัดผลให้คำตอบเดียวกัน

**ยังไม่แทน rules.py** — rules.py มี 2 พารามิเตอร์ อธิบายได้ทุกตัว ตรวจสอบด้วยมือได้
เหมาะเป็นตัวอ้างอิงและตัวสำรอง · ตัวใหม่แม่นกว่าแต่เป็นกล่องดำ

### เล่นย้อนดูโมเดลทำงาน — `car/replay.py`

เล่นข้อมูลที่อัดไว้ทีละเฟรม ตั้งแต่เฟรมแรกจนเฟรมสุดท้าย **ไม่ต้องต่อฮาร์ดแวร์**

```bash
python car/replay.py --section 1              # เล่นบนหน้าต่าง
python car/replay.py --section 1 --save o.mp4 # อัดเป็นวิดีโอ
```

ปุ่ม: `space` หยุด · `,` `.` เดินทีละเฟรม · `<` `>` กระโดด 30 · `+` `-` ปรับความเร็ว ·
`r` กลับต้น · `s` เซฟภาพ · `q` ออก

**ใช้ `predict.Predictor` กับ `predict.render` ตัวเดียวกับตอนรันสด** ไม่ได้เขียนใหม่
สิ่งที่เห็นตอนเล่นย้อนจึงเป็นสิ่งเดียวกับที่รถจะเห็นจริง

**ตัวเลขซื่อสัตย์**: `rules.py` เก็บสัมประสิทธิ์ไว้สองชุด — ชุดหลักฟิตจากทุกช่วง
(ใช้ตอนรันสด) และ `holdout_slope/intercept` ฟิตจากชุดเทรนล้วน `replay.py` เลือกใช้
ชุดหลังอัตโนมัติเมื่อเล่นช่วงที่กันไว้ทดสอบ และขึ้นป้ายบอกบนจอว่ากำลังดูชุดไหน

| ช่วงที่เล่น | ป้ายบนจอ | โซนถูก | มุมผิด |
|---|---|---|---|
| s1 (กันไว้ทดสอบ) | 🟢 TEST SECTION — model never saw these frames | **82%** | **4.7°** |
| s3 (อยู่ในชุดเทรน) | 🟡 TRAINED ON THIS — numbers look better than reality | 86% | 4.8° |

ตัวเลขของ s1 ตรงกับผลออฟไลน์ (82% · 4.8°) เป๊ะ — ยืนยันว่าเส้นทางเล่นย้อนกับเส้นทาง
วัดผลให้คำตอบเดียวกัน

**เก็บผลที่คำนวณแล้วไว้ทุกเฟรม** (ไม่เก็บภาพ depth — cache แค่ 98 KB) ถอยหลังหรือ
กระโดดกลับจึงทันที 0 ms ถ้าไม่เก็บ การถอย 1 เฟรมตอนอยู่ท้ายช่วงต้องไล่คำนวณใหม่
ตั้งแต่ต้น เพราะมัธยฐานย้อนหลังมีสถานะสะสม = รอ 25 วินาทีต่อการกดหนึ่งครั้ง

### ขาตั้ง + ที่วางกล้อง (พิมพ์ 2 ชิ้น)

สเปก: [`hardware/stand_spec.md`](hardware/stand_spec.md) · โมเดล:
[`hardware/stand_model.py`](hardware/stand_model.py) ·
ไฟล์พิมพ์ `cad/stand_base.stl` (~160 g) + `cad/cam_cradle.stl` (~34 g)

| | ค่า |
|---|---|
| ฐาน + เสา | 145 × 150 × 206 มม. · ยึดแผงด้วยรูเดิม **ครบ 4 รู** (M4 × 25) |
| เดือยรองแผง | ⌀14 สูง **12 มม.** — เว้นที่ให้สายเซ็นเซอร์ที่ออกหลังแผง ไม่ให้ถูกหนีบ |
| ช่องร้อยสาย | 50 × 22 มม. ที่ z = 95 ลอดไปหลังเสา |
| รางกล้อง | ล็อกซ้าย-ขวาอย่างเดียว กว้างใน 167 มม. · ปรับหน้า-หลังได้ ±7.5 มม. |
| ความสูงกึ่งกลางแผง | **125 มม.** เหนือผิวฐาน |

**วางกล้องชิดแผงดีกว่าวางไกล** — ลำเสียงเป็นกรวยที่กางออกตามระยะ ขอบล่างของกรวย 30°
จาก RX คู่ล่างอยู่ที่ z = 67.7 มม. เมื่อ x = 30 แต่เหลือ 30.2 มม. เมื่อ x = 95
หลังคากล้องอยู่ 46 มม. จึงพ้นเมื่อวางชิด และ**โดนบังเมื่อวางไกล**

**ต้องวัด `CAM_W` (ความยาวกล้อง) ก่อนพิมพ์** ค่าตั้งต้น 165 มม. ตามสเปก Orbbec
รางไม่มีผนังหน้า-หลัง จึงมีมิติเดียวที่ต้องถูก

## สถานะอุปกรณ์ที่ซื้อมา (เทียบ BOM กับที่ใช้จริง)

| อุปกรณ์ | สถานะ | ใช้ตอน |
|---|---|---|
| มัลติมิเตอร์ · สาย USB · ESP32 #1 · 74HCT04 · breadboard ×3 · ชุด R/C · IC socket · แผ่นสะท้อน · ไม้บรรทัด | **ใช้แล้ว** | Stage 1-2 |
| TCT40 (1 T + 2 R จาก 12 คู่) · MCP6004 · อิเล็กโทรฯ 10/100µF | **ใช้อยู่** | ภาคส่ง/รับปัจจุบัน |
| ESP32 #2 | จะใช้ | **Stage C** (master/slave อ่านพร้อมกันตอนรถวิ่ง — Stage B ใช้ยิงสองครั้งทีละคู่แทน ไม่ต้องใช้) |
| TCT40 ที่เหลือ · หัวแร้ง+ตะกั่ว | จะใช้ | Stage B (บัดกรีช่องเพิ่มลงไข่ปลา) |
| MCP6024 ×6 | **จะใช้** | **Stage B (ไข่ปลา)** — ใส่ตอนทำช่องที่ 2-9 แล้วถอดเปลี่ยนช่องแรกด้วย ใช้ 5 เหลือสำรอง 1 |
| **74HCT04 ที่เหลือ ×2 · หัวส่ง TCT40 ×2** | **จะใช้** | **Stage B+ (MIMO 3 TX)** |
| **แผ่นไข่ปลา 9x15 cm ×4** | **กำลังใช้** | Stage B — ย้ายภาครับลงบัดกรี (ผัง `hardware/diagrams/perf_*.svg`) |
| ต้องซื้อเพิ่ม: **IC socket DIP-14 ×5 · ลวดแข็ง · pin header · ฟลักซ์ · ที่ดูดตะกั่ว** | ยังไม่มี | Stage B (ไข่ปลา) |
| TC4428A ×3 | อาจใช้ | Stage C/D ถ้าต้องยิงไกลขึ้นบนรถ |
| **LM393 ×4 · 1N4148 ×20 · trimpot · ADS1115** | **น่าจะไม่ใช้แล้ว** | แผนเดิมช่อง far แบบ comparator — แผนรถใช้ raw ทุกช่องป้อน NN จึงไม่ใช้ envelope→comparator (ของสามัญ เก็บใช้โปรเจกต์อื่นได้) |

**Logic analyzer** ยังไม่ได้ใช้ เก็บไว้ดีบัก sync ของ master/slave ใน Stage B ได้

**แผ่นไข่ปลา + pin header** ถ้ายังไม่ได้ซื้อ ให้ซื้อก่อน Stage B (ภาครับ 4 ช่องย้ายมาบัดกรีที่นี่)

### กับดักบน Windows: ไลบรารี native ที่จัดของตอนถูกเรียกครั้งแรก

เจอมาแล้ว **สามรอบ** กับ numpy, GC และล่าสุด torch อาการเหมือนกันหมดคือ
โปรเซสตายเงียบ ๆ ไม่มี exception มีแต่ stack ที่ชี้ไปที่เธรดกล้องค้างอยู่ใน
`oniStreamReadFrame` พร้อมกับอีกเธรดที่กำลังจัดหน่วยความจำก้อนใหญ่

เหตุคือไลบรารีพวกนี้ **ไม่ได้จัดของตอน import หรือตอนโหลดโมเดล แต่จัดตอนถูกเรียกจริงครั้งแรก**
พอไปชนกับเธรด native ของ OpenNI ที่กำลังทำงาน heap ก็พัง

กฎของโปรเจกต์นี้: **ซ้อมทุกเส้นทางคำนวณด้วยข้อมูลปลอมก่อนเปิดกล้องเสมอ**
(`record._warmup`, `NNPredictor.warmup`, `live_polar.Model.warmup`) และ `gc.disable()`

วัดแล้วเห็นชัด — forward ครั้งแรกของ torch แพงกว่าครั้งถัดไป **28 เท่า**
(27.5 ms เทียบ 1.0 ms) นั่นคือก้อนงานที่ไปชนกับกล้องพอดี

**ต้องซ้อมด้วยจำนวนจุดจริง** torch เลือกวิธีคำนวณตามรูปร่างข้อมูล ของจริงคือ
871 จุด ไม่ใช่ค่าเริ่มต้น 677 ซ้อมผิดรูปร่าง = มันไปจัดของใหม่ตอนกล้องเปิดอยู่ดี

## โมเดลแผนที่ depth — ML ล้วน ออกเป็นภาพระยะ

รับคลื่น 4 ช่อง ตอบ **ภาพระยะ 40x30** (1,200 ช่อง ช่องละ "มีวัตถุไหม" + "ไกลเท่าไร")
ไม่มีป้ายซ้าย/กลาง/ขวาแล้ว วาดเป็นกลุ่มจุดไล่เฉดฟ้า(ใกล้)→ม่วง(ไกล)
รายละเอียดทั้งหมดอยู่ที่ [`explain_map_model.md`](explain_map_model.md)

```bash
python car/mapdata.py                             # สร้างแคชครั้งเดียว (29,509 เฟรม)
python car/train_map.py --test 1                  # เทรน
python car/check_map.py                           # ตรวจว่าเห็นอะไรจริง
python car/live_map.py --port COM5                # ดูสด
python car/live_map.py --name walk2 --section 1   # เล่นย้อน
```

| | IoU | ระยะพลาด |
|---|---|---|
| ทายค่าเฉลี่ย | 0.308 | 28.2 ซม. |
| แม่แบบรู้ตำแหน่งจริง (โกง) | 0.731 | 8.8 ซม. |
| **โมเดล เสียงล้วน** | 0.659 | **6.4 ซม.** |
| โมเดล + สลับคลื่น | 0.248 | 29.1 ซม. |

**อ่านผล: เสียงบอกตำแหน่งและระยะได้จริง แต่รูปร่างที่เห็นเป็นค่าเฉลี่ยที่จำมา**

ระยะแม่นกว่าคู่เทียบทุกตัว เพราะเวลาเดินทางวัดระยะได้ตรง ๆ
แต่ IoU แพ้คู่เทียบที่ได้มุมจริงจากกล้องฟรี ๆ และวัดด้วย R² แล้วโมเดล
**อยู่ใต้เพดาน "รู้แค่ตำแหน่ง" ทั้งแกนนอนและแกนตั้ง**

จะได้รูปร่างจริงต้องแก้ที่ฮาร์ดแวร์ — เสา 4 ต้นเรียงแนวนอนล้วน แยกบน-ล่างไม่ได้
ในทางฟิสิกส์ และที่ 40 kHz แยกมุมได้ราว 4 องศาเท่านั้น **แผน 3x3 ตอบโจทย์นี้ตรง ๆ**
