pawaritmuangrach/ultrasonic01/explain_car.md

# เกิดอะไรขึ้นในวงจร — คำอธิบายทีละภาค

เอกสารนี้อธิบาย **"สัญญาณเดินทางอย่างไร"** ตั้งแต่ ESP32 สั่งยิง จนได้คำตอบว่า
*วัตถุอยู่ห่างกี่เซนติเมตร และเบนซ้าย/ขวากี่องศา* — เขียนให้ใช้อธิบายคนอื่นได้

> ตัวเลขอ้างอิงพื้นฐาน: เสียงเดินทาง **343 m/s** → ไป-กลับ **1 cm ใช้เวลา 58.3 µs**
> ความถี่ใช้งาน **40 kHz** (ความยาวคลื่น 8.6 mm) เลือกตามความถี่เรโซแนนซ์ของหัวส่ง-หัวรับ

---

## ภาพรวม — เส้นทางสัญญาณทั้งเส้น

```
[1] ESP32 GPIO18 ──► [2] 74HCT04 ──► [3] R 100Ω ──► หัวส่ง TCT40-16T
                        (3.3V→5V)                          │
                                                    คลื่นเสียง 40 kHz
                                                           ▼
                                                        วัตถุ
                                                           │  สะท้อนกลับ (อ่อนมาก)
                                                           ▼
หัวรับ TCT40-16R ──► [4] Cin+Rb ──► [5] สเตจ 1 ×11 ──► สเตจ 2 ×11 ──► [6] R_out+C_out
   (~1 mV)              ตัดไฟตรง        รวม ×121 (จริง ~91)                │
                        ตั้งกลาง 1.65V                                     ▼
                                                          [7] ESP32 ADC 12-bit 266 kHz/ช่อง
                                                                           │
                                                          [8] ซอฟต์แวร์: ระยะ + มุม
```

**หัวใจของทั้งระบบมีสองข้อ**
1. เสียงสะท้อนกลับมา **เล็กมาก (~1 mV)** ต้องขยายราว 100 เท่าก่อน ADC จะอ่านออก
2. **เวลา** ที่เอคโค่กลับมา = ระยะ · **ความต่างของเวลาระหว่างหัวรับแต่ละตัว** = มุม

---

## ภาค 1 — ESP32 สั่งยิง

ESP32 สร้างคลื่นสี่เหลี่ยม **40 kHz จำนวน 16 ลูก** ออกที่ **GPIO18** (ยิงครั้งหนึ่งกินเวลา
16 ÷ 40 kHz = **400 µs**) แล้วสลับไปเป็นโหมดฟังทันที

**ทำไมต้องเป็นชุดสั้น ๆ ไม่ใช่ยิงต่อเนื่อง:** ต้องเงียบเพื่อฟังเสียงสะท้อน ถ้ายิงตลอด
จะแยกไม่ออกว่าเสียงที่ได้ยินเป็นของตัวเองหรือเป็นเอคโค่

**ผลข้างเคียงที่ต้องยอมรับ:** ระหว่าง 400 µs ที่กำลังยิง หัวรับจะได้ยินเสียงของตัวเองดังมาก
จึงเกิด **โซนบอด ~7 cm** — วัตถุที่ใกล้กว่านี้อ่านไม่ได้

---

## ภาค 2 — วงจรขับหัวส่ง (74HCT04 + R 100Ω)

GPIO ของ ESP32 จ่ายได้แค่ 3.3V และกระแสน้อย ซึ่งเบาเกินกว่าจะขับหัวส่งให้ดัง
จึงส่งผ่านชิป **74HCT04** (inverter 6 เกต) ที่เลี้ยงด้วยไฟ **5V**

| ส่วน | หน้าที่ | ทำไม |
|---|---|---|
| **74HCT04** | แปลง 3.3V → 5V และเพิ่มกระแส | ได้แรงขับ **5 Vpp** แทน 3.3 Vpp = เสียงดังขึ้น |
| ตัว **T** ใน HCT | รับลอจิก 3.3V ได้ | 74HC04 (ไม่มี T) ต้องการ 3.5V → ESP32 ขับไม่ขึ้น ทำงานแบบสุ่ม |
| ขนานหลายเกต | ลดความต้านทานขาออก | เกตเดียวจ่ายกระแสไม่พอ |
| **R 100Ω อนุกรม** | จำกัดกระแสพีค | หัวส่งคือ **คาปาซิเตอร์ 2.4 nF** ไม่ใช่ลำโพง ถ้าไม่มี R กระแสพุ่ง 333 mA (เกินพิกัดชิป 6 เท่า) และทำให้กราวด์เด้ง 0.7V ซึ่งท่วมสัญญาณรับที่มีแค่ 1 mV · ใส่ R แล้วเหลือ 43 mA ✅ |

> **ข้อห้าม:** ห้ามต่อขาออกของ 74HCT04 (5V) กลับเข้า GPIO ของ ESP32 — พังถาวร
> ทิศทางมีทางเดียว: ESP32 → 74HCT04 → หัวส่ง

---

## ภาค 3 — VREF 1.65V (ไฟอ้างอิงกลาง)

**ปัญหา:** วงจรเลี้ยงด้วยไฟชุดเดียว 0-3.3V แต่คลื่นเสียงมีทั้งค่าบวกและลบ
ถ้าตั้งจุดพักไว้ที่ 0V ครึ่งล่างของคลื่นจะถูกตัดหายไป

**วิธีแก้:** ตั้งจุดพักไว้ **กลางทาง = 1.65V** คลื่นจึงแกว่งขึ้น-ลงรอบจุดนี้ได้เต็มที่

```
3.3V ──[10k]──┬──[10k]── GND        ตัวแบ่งแรงดัน → ได้ 1.65V
              │
              └──► ออปแอมป์ต่อเป็น "ตัวตาม" (buffer) ──► บัส VREF เลี้ยงทุกช่อง
```

**ทำไมต้องมีบัฟเฟอร์ ไม่ใช้ตัวแบ่งตรง ๆ:** ตัวแบ่ง 10k/10k มีอิมพีแดนซ์ 5 kΩ ถ้าเอาไป
เลี้ยงหลายช่องพร้อมกัน กระแสของช่องหนึ่งจะทำให้ VREF กระเพื่อม แล้วไปกวนช่องอื่น
(= ครอสทอล์ก) **บัฟเฟอร์ทำให้เหลือต่ำกว่า 1 Ω** จึงแยกช่องออกจากกันได้จริง

---

## ภาค 4 — ทางเข้าของสัญญาณ (Cin + R_bias)

หัวรับให้สัญญาณ AC เล็ก ๆ ราว **1 mV** ที่ลอยอยู่รอบ 0V แต่วงจรต้องการให้มันลอยรอบ 1.65V

| ชิ้น | ค่า | หน้าที่ |
|---|---|---|
| **Cin** | 100 nF | **กั้นไฟตรง** ปล่อยผ่านเฉพาะคลื่น 40 kHz — หัวรับจึงไม่ไปดึงจุดพัก 1.65V ให้เพี้ยน |
| **R_bias** | 10 kΩ | **ดึงจุดพักให้มาอยู่ที่ VREF** ถ้าไม่มี ขาอินพุตจะลอย กลายเป็นเสาอากาศ |

**ทำไม R_bias ต้องเป็น 10k ไม่ใช่ 1M:** ตอนใช้ค่าสูง ๆ วงจรรับ **ฮัมไฟบ้าน 50 Hz** เข้ามา
จนเอาต์พุตแกว่งเต็มราง 3.3 Vpp (วัดจริงได้ 1059 mV) เพราะที่ 50 Hz หัวรับแทบเป็นวงจรเปิด
กระแสรั่วจากสายไฟบ้านจึงตกคร่อม R_bias เต็ม ๆ **ลดเหลือ 10k แล้วฮัมลดลง 10 เท่า**
และความถี่ตัดล่างขยับจาก 16 Hz → 159 Hz ช่วยทอน 50 Hz อีก 3.3 เท่า

---

## ภาค 5 — ภาคขยาย 2 ชั้น (หัวใจของวงจร)

```
สัญญาณเข้า ──► ขา 3 (+) ┌────────┐
                        │ ออปแอมป์ │──► ขา 1 (ออก)  เกน ×11
              ขา 2 (−) ─┤        │      │
                        └────────┘      │
                    ▲                   │
                    └─── Rf1 100k ──────┘
                    │
                  Rg1 10k ── Cg1 1nF ── GND
```

**เกนต่อสเตจ = 1 + Rf/Rg = 1 + 100k/10k = 11** → สองสเตจได้ **11 × 11 = 121 เท่า**
(ในทางปฏิบัติเหลือ ~91 หลังคิดผลของ Cg และการโหลดหัวรับ)

### ทำไมต้องซอยเป็น 2 ชั้น ไม่ใช่ชั้นเดียว ×121

ออปแอมป์มีข้อจำกัดชื่อ **GBW** (เกน × แบนด์วิดท์ = ค่าคงที่) MCP6004 มี GBW = 1 MHz

| แบบ | เกน/สเตจ | แบนด์วิดท์ที่ได้ | ใช้กับ 40 kHz ได้ไหม |
|---|---|---|---|
| ชั้นเดียว ×121 | 121 | 1 MHz ÷ 121 = **8.3 kHz** | ❌ ต่ำกว่า 40 kHz มาก สัญญาณหาย |
| **สองชั้น ×11** | 11 | 1 MHz ÷ 11 = **91 kHz** | ✅ เหลือระยะขอบ |

### หน้าที่ของ Cg (สำคัญกว่าที่คิด)

Cg ต่ออนุกรมกับ Rg ลงกราวด์ ทำให้ **เกนเปลี่ยนไปตามความถี่**

| ความถี่ | เส้นทางผ่าน Cg | เกน |
|---|---|---|
| ไฟตรง (0 Hz) | Cg กั้นสนิท → เหมือน Rg หลุด | **×1** |
| 50 Hz (ฮัมไฟบ้าน) | ผ่านได้น้อย | **×1.03** |
| 40 kHz (สัญญาณเรา) | ผ่านสบาย | **×11** ✅ |

- **เกน DC = 1** แปลว่าแรงดันออฟเซ็ตของออปแอมป์ไม่ถูกขยาย ทุกขาจึงนั่งนิ่งที่ ~1.65V
- **กด 50 Hz ทิ้ง** เปลี่ยน Cg จาก 100nF → 1nF ช่วยทอนฮัมรวมกันได้ราว **500 เท่า**
  (1059 mV → ~2 mV) ขณะที่เกนที่ 40 kHz แทบไม่ลด

> **จุดที่ใช้ตรวจว่าวงจรปกติ:** ขา 1, 2, 3, 5, 6, 7 ต้องวัดได้ **~1.65V เท่ากันหมด**
> ถ้าขาไหนเป็น 0V หรือ 3.3V = สเตจนั้นอิ่มตัว มีอะไรต่อผิด

---

## ภาค 6 — ขาออกไปหา ADC (R_out + C_out)

`ขา 7 ──[ R_out 1–2.2k ]──┬──► GPIO34 (ADC)`
`                          └── C_out 1nF ── GND`

| ชิ้น | หน้าที่ |
|---|---|
| **R_out** | จำกัดกระแสถ้าขา ADC มีปัญหา และกันออปแอมป์แกว่งเมื่อเจอโหลดเป็นคาปา |
| **C_out** | พักประจุให้ ADC — ตอน ADC เริ่มสุ่ม มันจะดูดประจุจากสายทันที ถ้าไม่มี C_out แรงดันจะแกว่งตอนสุ่ม ทำให้อ่านเพี้ยน |

---

## ภาค 7 — ESP32 อ่านค่า

- ADC 12 บิต (0-4095 = 0-3.3V) ทำงานโหมด **ต่อเนื่อง (adc_continuous)**
- **อ่านพร้อมกันได้ทีละ 2 ช่อง** ที่ **266 kHz ต่อช่อง** (เพดานจริงของฮาร์ดแวร์)
- ต้องการ 4 ช่อง → **ยิง 2 ครั้ง อ่านทีละคู่** (ใช้ได้เพราะตอนเก็บข้อมูลฉากนิ่ง)
- เก็บ 12,000 ตัวอย่าง/ช่อง = 45 ms = ครอบคลุมระยะ ~2.5 m

**ทำไมต้องเร็วขนาดนี้:** คลื่น 40 kHz หนึ่งลูกกินเวลา 25 µs ที่ 266 kHz จะได้ตัวอย่าง
~6.6 จุดต่อลูกคลื่น พอให้จับรูปร่างคลื่นและวัดเวลาได้ละเอียดระดับไมโครวินาที

---

## ภาค 8 — ซอฟต์แวร์แปลงเป็นระยะและมุม

### ขั้นที่ 1: หาเปลือกคลื่น (envelope)
คลื่นดิบแกว่งขึ้นลง 40,000 ครั้ง/วินาที — เราไม่สนใจตัวคลื่น สนใจแค่ **"ตอนไหนดัง"**
จึงคำนวณเปลือกของมันออกมาเป็นเส้นโค้งเรียบ ๆ ที่มี "เนิน" ตรงตำแหน่งที่มีเอคโค่

### ขั้นที่ 2: ระยะ = ฟิสิกส์ล้วน
หาตำแหน่งเนินที่สูงที่สุด แล้วแปลงเวลาเป็นระยะ:

```
ระยะ (cm) = (เวลาที่เจอเนิน − T0) × 343 m/s ÷ 2 × 100
```
- **หาร 2** เพราะเสียงเดินทางไป-กลับ
- **T0 = 1220 µs** คือเวลาหน่วงของระบบเอง (ความยาวชุดยิง + หน่วงของวงจรกรอง)
  ค่านี้ได้จากการเทียบกับกล้องวัดระยะ — ตอนแรกตั้งผิดเป็น 435 µs ทำให้อ่านเกินจริง 13 cm ทุกครั้ง
- **ประตูระยะ (range gate) 40-250 cm** — สนใจเฉพาะช่วงนี้ ไม่งั้นจะไปเกาะเสียงขยะใกล้ ๆ

> ระยะ**ไม่ต้องใช้ AI** — คำนวณตรง ๆ แม่นกว่า: **7.3 cm** เทียบกับให้โมเดลเดา 13.6 cm

### ขั้นที่ 3: มุม = ต้องใช้โมเดลที่เทรน
หัวรับสองตัวที่วางห่างกัน จะได้ยินเอคโค่**ไม่พร้อมกัน** ถ้าวัตถุอยู่เยื้องไปข้างหนึ่ง

```
วัตถุเยื้องซ้าย → หัวรับซ้ายได้ยินก่อน → ผลต่างเวลา (TDOA) เป็นบวก
วัตถุอยู่ตรงกลาง → ได้ยินพร้อมกัน     → TDOA = 0
```

ผลต่างนี้เล็กมาก (ระดับไมโครวินาที) และยังปนกับความไม่เท่ากันของหัวรับแต่ละตัว
จึงคำนวณตรง ๆ ไม่แม่น ต้อง**ให้โมเดลเรียนจากข้อมูลจริง** โดยใช้กล้องวัดระยะเป็นเฉลย

**ผลที่ได้จริง (1,544 ตัวอย่าง):** มุมคลาดเคลื่อนเฉลี่ย **11.8°** เทียบกับเดาสุ่ม 14.8°
— ใกล้แม่นกว่า (8.1° ที่ 53 cm) ไกลแย่ลง (13.8° ที่ 154 cm)

---

## สรุปตัวเลขสำคัญ

| หัวข้อ | ค่า |
|---|---|
| ความถี่ทำงาน | 40 kHz |
| ความเร็วเสียง | 343 m/s (1 cm ไป-กลับ = 58.3 µs) |
| ชุดยิง | 16 ลูก = 400 µs → โซนบอด ~7 cm |
| แรงขับหัวส่ง | 5 Vpp ผ่าน R 100Ω (กระแสพีค 43 mA) |
| สัญญาณที่หัวรับ | ~1 mV |
| เกนภาครับ | 11 × 11 = 121 (จริง ~91) |
| จุดพัก VREF | 1.65V (ครึ่งของ 3.3V) |
| ADC | 12 บิต · 266 kHz/ช่อง · ทีละ 2 ช่อง |
| ช่วงวัด | 40-250 cm |
| ความแม่นระยะ | 7.3 cm (ฟิสิกส์) |
| ความแม่นมุม | 11.8° (โมเดล) |

---

## คำถามที่มักโดนถาม

**ถาม: ทำไมไม่ใช้โมดูล HC-SR04 สำเร็จรูป**
ตอบ: HC-SR04 บอกได้แค่ "ระยะของสิ่งที่ดังที่สุด" 1 ค่า บอกทิศไม่ได้เลย
โปรเจกต์นี้ต้องการ **ทิศทาง** ด้วย จึงต้องมีหัวรับหลายตัวและเข้าถึงคลื่นดิบเพื่อวัด TDOA

**ถาม: ทำไมต้องขยายถึง 121 เท่า**
ตอบ: ADC แยกแยะได้ละเอียดสุด 3.3V ÷ 4096 = **0.8 mV** ซึ่งพอ ๆ กับขนาดสัญญาณดิบ (~1 mV)
ถ้าไม่ขยาย เอคโค่จะจมอยู่ในระดับ 1 บิต มองไม่เห็นอะไรเลย

**ถาม: ทำไมอัลตราซาวด์เห็น "เสียงที่ดังที่สุด" ไม่ใช่ "สิ่งที่ใกล้ที่สุด"**
ตอบ: ผิวเรียบ (กระเบื้อง กระจก) สะท้อนเหมือนกระจกเงา — ถ้าไม่ได้หันหน้าเข้าหาเซ็นเซอร์พอดี
เสียงจะสะท้อนไปทางอื่นและ "หายไป" ขณะที่ผนังไกล ๆ ที่หันตรงกลับดังกว่า
นี่คือเหตุผลที่ใช้ **ท่อ PVC ทรงกระบอก** เป็นเป้าทดสอบ — ทรงกระบอกสะท้อนกลับได้ทุกมุม

---

*ค่าอุปกรณ์อ้างอิงจาก `hardware/rx_frontend.md` §4.1/§5 และ `hardware/tx_driver.md` §2*
*(หมายเหตุ: ผังวาดใน rx_frontend.md §3 ยังเป็นค่าชุดเก่า — ค่าที่ใช้จริงคือชุดใน §4.1)*
