pawaritmuangrach/ultrasonic01/pcb/3d-models.md

# ทำไม 3D ถึงโล่ง และทำยังไงให้เห็นตัวชิป

## สาเหตุจริง ไม่ใช่เรื่องรูปแบบไฟล์

EasyEDA วาดภาพ 3D จาก **โมเดล 3D ที่ผูกอยู่กับ footprint ในคลังของ EasyEDA เอง**
ไม่ได้วาดจากข้อมูลในไฟล์ที่นำเข้า

footprint ที่มากับไฟล์นำเข้ามีแค่ **ตำแหน่งรู ขนาดแป้น และเส้นซิลค์สกรีน**
ซึ่งเป็นข้อมูล 2 มิติล้วน ๆ ไม่มีคำว่า "ตัวนี้เป็นชิป DIP-14 สูง 4 มม." อยู่ในนั้นเลย
โปรแกรมจึงไม่มีอะไรจะเอาไปวาดเป็นก้อน

## เปลี่ยนไปนำเข้ารูปแบบอื่นช่วยไหม

| รูปแบบ | พา 3D มาด้วยได้ไหม |
|---|---|
| KiCad (ที่ใช้อยู่) | ไม่ได้ · อ้างถึงไฟล์ .step ภายนอกด้วยเส้นทางไฟล์ ซึ่งไม่ได้อยู่ในซิป |
| Gerber | ไม่ได้ · มีแต่รูปร่างทองแดง ไม่มีแม้แต่ชื่อชิ้นส่วน |
| Eagle | ไม่ได้ · เก็บ footprint เป็น 2 มิติเหมือนกัน |
| Altium | ตามทฤษฎีฝัง 3D ลงไฟล์ได้ แต่เป็นไฟล์ไบนารีที่ไม่มีสเปกเปิด สร้างเองไม่ไหว |

**สรุป: ไม่มีรูปแบบไหนที่ผมสร้างจากฝั่งไฟล์แล้วจะทำให้ 3D โผล่มาได้**
เพราะต้นตอไม่ใช่รูปแบบไฟล์ แต่คือ **เราไม่มีข้อมูลโมเดล 3D อยู่ในมือตั้งแต่แรก**

## ทางที่ได้ผลจริง — เปลี่ยน footprint ไปใช้ของคลัง EasyEDA

ของในคลัง EasyEDA มีโมเดล 3D ติดมาให้อยู่แล้วทุกตัว

**ข่าวดี: ตัวถังที่เราใช้เป็นของมาตรฐานทั้งหมด** ผมเลือกระยะขาให้ตรงมาตรฐานตั้งแต่ต้น
เปลี่ยนแล้วรูจะลงตำแหน่งเดิม ไม่ต้องย้ายอะไร ไม่กระทบลายที่เดินไว้

| ตัวเราใช้ | ระยะขา | ค้นในคลัง EasyEDA ด้วยคำว่า | ใช้กับ |
|---|---|---|---|
| DIP14 | 2.54 แถวห่าง 7.62 | `DIP-14` | U1-U6 |
| R_AXIAL | 7.62 | `AXIAL-0.3` | ตัวต้านทาน 54 ตัว |
| C_DISC | 5.08 | `RAD-0.2` | คาปาจาน 39 ตัว |
| C_ELEC | 2.54 | `RAD-0.1` | CB1 CB2 |
| C_BULK | 5.08 | `RAD-0.2` | CF |
| HDR20 | 2.54 | `HDR-1X20` ตัวเมีย | JA JB |
| TERM2 | 5.08 | `KF301-5.0-2P` | TX1-3 RX1-8 ไฟเข้า |

**ต้องเช็คระยะขาทุกครั้งก่อนเปลี่ยน** ถ้าระยะขาไม่ตรงกับตารางนี้ รูจะเลื่อน
แล้วลายที่เดินไว้จะขาด ให้ดูตัวเลขในคอลัมน์ "ระยะขา" เป็นตัวตัดสิน ไม่ใช่ดูแค่ชื่อ

## ลำดับที่แนะนำ

1. เดินลายและตรวจ DRC ให้ผ่านก่อน — **3D เป็นเรื่องความสวยงาม ไม่ใช่เรื่องที่โรงงานใช้**
   ไฟล์ที่ส่งโรงงานคือ Gerber กับ Excellon ซึ่งไม่มี 3D อยู่แล้วโดยธรรมชาติ
2. ถ้าอยากเห็น 3D ค่อยไล่เปลี่ยน footprint ทีหลัง มี 7 แบบเท่านั้น
   เปลี่ยนแบบเดียวแล้วใช้กับทุกตัวที่ใช้ตัวถังนั้นได้
3. ลอง `Device Standardization` ใน EasyEDA ก่อน เป็นเครื่องมือจับคู่ชิ้นส่วน
   กับของมาตรฐานในคลัง ถ้ามันจับคู่ให้ได้ทีเดียวก็ไม่ต้องไล่ทีละตัว

## สิ่งที่ผมทำให้แล้วและช่วยได้จริงกว่า

เพิ่ม **เส้นกรอบตัวถัง 464 เส้น** กับ **จุดบอกขา 1** ลงซิลค์สกรีน
ซึ่งเดิมไม่มีเลยแม้แต่เส้นเดียว

อันนี้สำคัญกว่า 3D มาก เพราะ **ซิลค์สกรีนถูกพิมพ์ลงบอร์ดจริง**
คนประกอบใช้เส้นพวกนี้ดูว่าตัวไหนอยู่ตรงไหนและหันทางไหน
ส่วน 3D อยู่แค่ในจอ ไม่ได้ไปถึงบอร์ดจริง
