pawaritmuangrach/ultrasonic01/pcb/out/tx3/nets.md

# tx3 — ตารางการต่อ

ไว้ไล่วัดด้วยมิเตอร์โหมดเสียงปี๊บ ขาในแถวเดียวกันต้องปี๊บถึงกันหมด
ขาคนละแถวต้องไม่ปี๊บ ถ้าปี๊บ = ลายช็อต

| เน็ต | ขาที่ต่อถึงกัน |
|---|---|
| `+5V` | U1.14 · C1.1 · C2.1 · JP.1 |
| `GND` | U1.7 · C1.2 · C2.2 · JP.2 · J1.1 · T1.2 · T2.2 · T3.2 |
| `TX1_IN` | J1.2 · U1.1 |
| `TX1_MID` | U1.2 · U1.3 |
| `TX1_OUT` | U1.4 · R1.1 |
| `TX1_DRV` | R1.2 · T1.1 |
| `TX2_IN` | J1.3 · U1.13 |
| `TX2_MID` | U1.12 · U1.11 |
| `TX2_OUT` | U1.10 · R2.1 |
| `TX2_DRV` | R2.2 · T2.1 |
| `TX3_IN` | J1.4 · U1.5 |
| `TX3_MID` | U1.6 · U1.9 |
| `TX3_OUT` | U1.8 · R3.1 |
| `TX3_DRV` | R3.2 · T3.1 |
