pawaritmuangrach/ultrasonic01/hardware/plate_mini_coords.csv

id | x_mm | y_mm | z_mm | role | gpio | note
RX_TL | -55.00 | 55.00 | 14.00 | RX | 34 | ซ้ายบน
RX_BL | -55.00 | -55.00 | 14.00 | RX | 33 | ซ้ายล่าง
RX_BR | 55.00 | -55.00 | 14.00 | RX | 32 | ขวาล่าง
RX_TR | 55.00 | 55.00 | 14.00 | RX | 35 | ขวาบน
TX1 | 0.00 | 0.00 | 14.00 | TX | 18 | กลาง
M0 | 62.00 | 0.00 | 0.00 | MOUNT |  | รูยึด ⌀4.5
M90 | 0.00 | 62.00 | 0.00 | MOUNT |  | รูยึด ⌀4.5
M180 | -62.00 | 0.00 | 0.00 | MOUNT |  | รูยึด ⌀4.5
M270 | -0.00 | -62.00 | 0.00 | MOUNT |  | รูยึด ⌀4.5
