pawaritmuangrach/ultrasonic01/hardware/stand_spec.md

# ขาตั้ง plate_mini + ที่วางกล้อง Astra Pro — สเปกพิมพ์ 3D

พิมพ์ 2 ชิ้น สร้างจากโค้ด [`stand_model.py`](stand_model.py) →
`python hardware/stand_model.py` จะได้ STEP + STL + ภาพตัวอย่างใน `cad/`

| ไฟล์พิมพ์ | ขนาด | เนื้อตัน | น้ำหนักจริง (อินฟิล 25%) |
|---|---|---|---|
| `cad/stand_base.stl` | 145 × 150 × 206 มม. | 310.6 cm³ | ~197 g |
| `cad/cam_cradle.stl` | 45 × 177 × 24 มม. | 54.1 cm³ | ~34 g |

---

## ⚠️ วัดกล้องก่อนพิมพ์ — มีตัวเลขเดียวที่ต้องถูก

```python
CAM_W = 165.0      # ความยาวตัวกล้องซ้าย-ขวา  (hardware/stand_model.py บรรทัด 44)
```

สเปกที่ Orbbec ประกาศคือ **165 × 30 × 40 มม.** ซึ่งใช้เป็นค่าตั้งต้น แต่ตัวจริงอาจต่าง
ถ้ามีฐานเอียงติดมาด้วย **วัดด้วยไม้บรรทัดแล้วแก้บรรทัดเดียว แล้วรันใหม่** ใช้เวลา 10 วินาที

รางออกแบบให้ **ล็อกแค่ซ้าย-ขวา ไม่มีผนังหน้า-หลัง** ตามที่ขอ ผลพลอยได้คือ
**ความลึกกับความสูงของกล้องผิดได้ไม่เป็นไร** เหลือมิติเดียวที่ต้องถูก = เสี่ยงพิมพ์ผิดน้อยที่สุด

> อยากได้ขอบกันกล้องไหลไปข้างหลังด้วย ตั้ง `BACK_LIP = 6.0` แล้วรันใหม่

---

## ทำไมวางกล้อง**ชิด**แผงถึงดีกว่า

ลำเสียงเป็น**กรวยที่กางออกตามระยะ** ขอบล่างของกรวย 30° จาก RX คู่ล่าง
(สูง 70 มม. หน้าเซ็นเซอร์อยู่ที่ x = 26) ตกลงมาเป็น

```
z = 70 − tan(30°) × (x − 26)
```

| ระยะจากแผง | ขอบล่างของลำเสียง | หลังคากล้อง 46 มม. |
|---|---|---|
| x = 30 มม. (ขอบหลังราง) | 67.7 มม. | ✅ พ้นสบาย |
| x = 60 มม. (ขอบหน้ากล้อง) | 50.4 มม. | ✅ พ้น 4.4 มม. |
| x = 95 มม. (ตำแหน่งเดิม) | 30.2 มม. | ❌ **กล้องบังลำเสียง** |

**ยิ่งวางใกล้ ยิ่งบังน้อย** เพราะกรวยยังไม่ทันกางลงมา — ตำแหน่งเดิมที่ x = 95
กลับเป็นตำแหน่งที่แย่ที่สุด (ฉบับแรกคิดกลับด้าน)

ขอบหลังรางหยุดที่ **x = 30** เพราะบอส RX คู่ล่างกินพื้นที่ถึง x = 26
และยกแผงจาก 115 เป็น **125 มม.** เพื่อให้ปลายหน้าของกล้องพ้นขอบกรวยด้วย

---

## เดือยรองแผง 12 มม. — จำเป็น ไม่ใช่ของตกแต่ง

ตัวเซ็นเซอร์ TCT40 นั่งจมในรูลึก 14 มม. และ **สายออกทางด้านหลังแผง** ซึ่งเป็นด้าน
ที่แนบเสาพอดี ถ้าแผงแนบเสาสนิท **สายจะถูกหนีบ** — และสายที่ถูกดึงหรือหนีบคือจุดสัมผัสแข็ง
ที่ทำลายการแยกเสียงพอ ๆ กับการทากาว (ดู `plate_mini_spec.md` ข้อ 3)

เดือย ⌀14 สูง 12 มม. สามตัวยกแผงให้ลอย สายจึงมีที่เดินแล้วลอด**ช่องร้อยสาย
50 × 22 มม.** ที่ z = 95 ไปออกหลังเสาได้

---

## จุดยึดและอะไหล่ที่ต้องใช้

| จุด | จำนวน | สกรู |
|---|---|---|
| แผง ↔ เสา (ผ่านเดือย) | **4** | **M4 × 25 + น็อต** (แผง 4 + เดือย 12 + เสา 8 = 24 มม.) |
| ราง ↔ ฐาน | 2 | **M4 × 16 + น็อต M4** (น็อตหย่อนในช่องหกเหลี่ยมใต้ฐาน ไม่ต้องจับ) |

- แผงใช้รูยึด **ครบทั้ง 4 รู** — เสาสูง 200 มม. จึงรับรูบน (0, +62) ที่ z = 187 ได้
  (ฉบับแรกเสาสูง 140 มม. รูบนเลยลอยพ้นเสา ผู้ใช้ทักมาถึงเจอ)
  **ขันสามรูล่างให้แน่นก่อน แล้วค่อยขันรูบนพอตึงมือ** — เดือยพิมพ์ออกมาสูงไม่เท่ากันเป๊ะ
  ถ้าขันแน่นทั้งสี่พร้อมกันแผ่น 4 มม. จะถูกบิดเล็กน้อย ซึ่งย้ายตำแหน่งเซ็นเซอร์จากค่าที่ใช้คำนวณ
- ร่องบนรางยาว 15 มม. → **ปรับกล้องหน้า-หลังได้ ±7.5 มม.** หลังพิมพ์เสร็จ
- หัวสกรูของรางจมในบ่า ⌀8.6 ลึก 3 มม. จึงไม่โดนก้นกล้อง

---

## ค่าพิมพ์

| | ค่า | เหตุผล |
|---|---|---|
| วัสดุ | PETG | เหมือนแผง หน่วงการสั่นดี |
| ผนัง | 4 เส้น | ครีบค้ำหนา 6 มม. ต้องตันจริง |
| อินฟิล | 25% gyroid | |
| ซัพพอร์ต | **ไม่ต้อง** | เสา/ผนังรางตั้งฉาก · ช่องน็อตเปิดลงล่างเป็นชั้นแรก · ปลายครีบค้ำอยู่บนเนื้อฐาน |
| ทิศวาง | วางตามที่โมเดลวางไว้ (ฐานติดเตียง) | |

---

## ตรวจก่อนพิมพ์ (โค้ดทำให้อัตโนมัติ)

`python hardware/stand_model.py` จะพิมพ์ผลตรวจออกมาทุกครั้ง:

- **เมชปิดสนิท** ทั้งสองชิ้น
- **ระยะเนื้อขั้นต่ำระหว่างฟีเจอร์ 14 คู่** ต้อง ≥ 4 มม. ทุกคู่
- ราง**ไม่ยื่นเกินขอบฐาน** · ปลายครีบค้ำ**อยู่บนเนื้อฐาน** (ไม่พิมพ์ลอย)
- ขอบหลังราง**ไม่ชนบอส RX ล่าง**

> **บทเรียนจากรอบนี้** — สามข้อที่มองจากภาพไม่เห็นเลย แต่ตัวตรวจจับได้:
> 1. `both=True` ใน build123d ทำให้ทุกความหนาเป็น **สองเท่า** (ฐานหนา 12 แทน 6)
> 2. ช่องลดเนื้อกลางฐานกินขอบช่องน็อต M4 พอดี → ช่องน็อตแหว่ง ขันไม่ได้
> 3. ปลายครีบค้ำยื่นพ้นขอบฐาน 3 มม. → พิมพ์ลอยกลางอากาศ
