pawaritmuangrach/ultrasonic01/explain_map_model.md

# โมเดลแผนที่ depth จากเสียงล้วน — อธิบายทีละขั้น

เป้าหมาย: รับคลื่นสะท้อน 4 ช่อง แล้ววาดออกมาเป็นภาพระยะ ให้ใกล้เคียงกล้อง depth ที่สุด
ไม่มีสูตรที่คนเขียนเลย ป้อนคลื่นดิบเข้าไปตรง ๆ ให้โมเดลหาเอง

```bash
python car/mapdata.py                        # สร้างแคชครั้งเดียว
python car/train_map.py --test 1             # เทรน
python car/check_map.py                      # ตรวจว่าเห็นอะไรจริง
python car/live_map.py --port COM5           # ดูสด
python car/live_map.py --name walk2 --section 1   # เล่นย้อน
```

---

## 1. ต่างจากสองโมเดลก่อนหน้ายังไง

| | ป้อนอะไร | ตอบอะไร | ใครคิดสูตร |
|---|---|---|---|
| `rules.py` | ความแรง 4 ช่อง | มุมเดียว | คน (2 พารามิเตอร์) |
| `train_nn.py` | คลื่นดิบ | มุมเดียว | โมเดล (142k) |
| **`train_map.py`** | **คลื่นดิบ** | **ภาพระยะ 40x30** | **โมเดล (718k)** |

สองตัวแรกตอบเลขตัวเดียว ตัวนี้ตอบ 1,200 ช่อง ช่องละสองค่า

---

## 2. เป้าหมายที่ให้โมเดลเรียน

กล้องให้ภาพ 320x240 หน่วยมิลลิเมตร ย่อเหลือ **40x30 ด้วยบล็อก 8x8**

ย่อไม่ใช่เพราะสวย แต่เพราะ **กำลังแยกแยะของอาเรย์หยาบกว่านั้นมาก** — เสาห่างกัน 12 ซม.
ที่ความถี่ 40 kHz แยกมุมได้ราว 4 องศา ซึ่งกินพื้นที่ราว 7 ช่องของภาพ 40 ช่อง
ทำนายละเอียดกว่านี้คือทำนายลม

ย่อด้วย **มัธยฐานเฉพาะพิกเซลที่อ่านได้** ไม่ใช่ค่าเฉลี่ยทั้งบล็อก
เพราะกล้องคืน 0 ตรงที่อ่านไม่ได้ (ขอบวัตถุ ผิวมันวาว) ถ้าเฉลี่ยรวม 0 เข้าไปด้วย
ขอบของคนจะถูกดึงให้ดูใกล้กว่าความจริง

### หัวออกสองอัน ไม่ใช่อันเดียว

- `occ` — มั่นใจแค่ไหนว่ามีวัตถุอยู่ในช่วง 40–200 ซม.
- `depth` — ถ้ามี อยู่ไกลเท่าไร

แยกกันเพราะ **"ไม่มีอะไรตรงนี้" ไม่ใช่ "อยู่ไกลมาก"** ถ้ายัดรวมเป็นเลขเดียว
ที่ว่างจะถูกบังคับให้มีค่าระยะ แล้วลากค่าเฉลี่ยเพี้ยนทั้งภาพ

ตอนคิด loss จึงนับระยะ **เฉพาะช่องที่กล้องเห็นวัตถุจริง** ที่ว่างไม่มีระยะให้เรียน

---

## 3. เตรียมคลื่นก่อนป้อน

```
คลื่นดิบ -> ลบมัธยฐาน (ตัดไฟตรง) -> หารด้วย MAD ของตัวเอง -> ส่งความแรงเดิมไปอีกทางเป็น log
```

หารด้วยความแรงตัวเองเพื่อให้โมเดลดู **รูปร่างคลื่น** ไม่ใช่ดังเบา —
คนสะท้อนเสียงแรงต่างกันได้ถึง 40 เท่าที่ระยะเดียวกัน แล้วแต่ว่าหันตัวยังไง
แต่ความแรงก็มีข้อมูลของมัน (ไกลกว่า = เบากว่า) จึงไม่ทิ้ง ส่งแยกไปอีกทาง

ใช้ **MAD ไม่ใช่ส่วนเบี่ยงเบนมาตรฐาน** เพราะยอดสะท้อนกินพื้นที่นิดเดียวของคลื่น
ส่วนเบี่ยงเบนมาตรฐานจะโดนยอดลากจนวัดพื้นเสียงรบกวนไม่ได้

---

## 4. โครงโมเดล

```
คลื่น (4 ช่อง x 871 จุด)
   |
   +-- trunk  ใช้น้ำหนักชุดเดียวกันทั้ง 4 ช่อง   -> (4 x 32 x 55)
   |          ฟิสิกส์ของทุกช่องเหมือนกัน ต่างแค่ตำแหน่ง
   |          ใช้ร่วมกันจึงได้ข้อมูลต่อพารามิเตอร์มากกว่า
   |
   +-- mix    เอา 4 ช่องมาต่อกันแล้วผสม        -> (96 x 7)
   |          ความต่างเวลาระหว่างช่องคือที่มาของมุม
   |
   +-- fc     แผ่ทั้งก้อน + ความแรง 4 ค่า      -> 768
   |          **ไม่ยุบแกนเวลา** เพราะตำแหน่งบนแกนเวลาคือระยะ ยุบทิ้งคือทิ้งระยะ
   |
   +-- dec    3x4 -> 7x10 -> 15x20 -> 30x40   -> occ + depth
```

ขยายภาพด้วยการกำหนดขนาดปลายทางตรง ๆ ไม่ใช่ `ConvTranspose2d`
เพราะ 30 หารสองลงตัวไม่สวย (30 → 15 → 7.5) กำหนดเองชัดเจนกว่าไล่คำนวณ padding

---

## 5. แบ่ง train/test ยังไง

**ตามช่วงการอัด ไม่ใช่สุ่มรายเฟรม**

เฟรมที่ติดกันเกือบเหมือนกัน (กล้อง 15 fps คนขยับไม่ทันในหนึ่งเฟรม)
ถ้าสุ่มรายเฟรม เฟรมข้างเคียงของ test จะไปโผล่ใน train แล้วคะแนนพองเกินจริง

`--test 1` = กันช่วง s1 ของ **ทุกชุด** ไว้ (grid_s1 + walk_s1 + walk2_s1)

---

## 6. วิธีวัดผล — ส่วนที่สำคัญที่สุด

ภาพ depth ที่ทายออกมา **ดูน่าเชื่อได้ง่ายมาก** เพราะห้องกับคนหน้าตาคล้ายกันทุกเฟรม
โมเดลที่ตอบ "ภาพเฉลี่ย" เฉย ๆ ก็ดูดีแล้ว จึงต้องมีคู่เทียบ

### คู่เทียบ 1 — ทายค่าเฉลี่ย
ไม่ดูคลื่นเลย ตอบภาพเฉลี่ยของชุดเทรนทุกครั้ง
**ชนะไม่ได้ = ไม่ได้เรียนอะไรจากเสียงเลย**

### คู่เทียบ 2 — แม่แบบรู้ตำแหน่ง (โกง)
ดูมุมและระยะจริง**จากกล้อง** แล้วแปะรูปร่างเฉลี่ยของตำแหน่งนั้นลงไป
**ชนะไม่ได้ = เสียงบอกได้แค่ "อยู่ตรงไหน" ไม่ได้บอก "รูปร่างยังไง"**

นี่คือคำถามที่แพงที่สุดของโปรเจกต์ ถ้าชนะไม่ได้ ภาพสวย ๆ ที่เห็นก็เป็นแค่
รูปร่างเฉลี่ยที่ถูกเลื่อนไปวางถูกที่ ไม่ใช่การ "มองเห็น" ด้วยเสียงจริง ๆ

### สลับคลื่น
เอาคำตอบที่ทายจากคลื่นของเฟรมอื่น มาเทียบกับภาพจริงของเฟรมนี้
**ถ้าคะแนนไม่ตก แปลว่าโมเดลไม่ได้ใช้เสียงเลย** แค่จำภาพเฉลี่ยไว้ตอบ

### จุดตัดต้องหาให้ทุกฝ่าย
วัดด้วย IoU ไม่ใช่ "ทายถูกกี่ช่อง" เพราะภาพส่วนใหญ่เป็นที่ว่าง
การตอบ "ว่างทั้งภาพ" จะได้ความถูกต้องสูงลิ่วทั้งที่ไม่เจออะไรเลย

และต้องหาจุดตัดที่ดีที่สุดให้ **คู่เทียบด้วย** ไม่ใช่แค่โมเดล —
ภาพเฉลี่ยไม่มีช่องไหนเกิน 0.5 เลย (คนเดินไปมา ไม่มีจุดไหนมีคนยืนเกินครึ่งเวลา)
ถ้าล็อกจุดตัดไว้ที่ 0.5 คู่เทียบนี้จะได้ IoU 0.000 ซึ่งอ่อนเกินจริง แล้วโมเดลก็ดูเก่งเกินตัว
พอหาจุดตัดให้มัน คู่เทียบเดียวกันขยับจาก 0.000 เป็น 0.308 ทันที

---

## 7. ชุดข้อมูลที่ใช้

| ชุด | เฟรม | ระยะ (5–95%) | หน้าตา |
|---|---|---|---|
| `grid` | 16,970 | 66–173 ซม. | ถ่ายใกล้ เห็นแค่ลำตัวกับขา |
| `walk` | 4,300 | 54–107 ซม. | ใกล้มาก ลำตัวเต็มเฟรม |
| `walk2` | 8,092 | 64–150 ซม. | **เห็นคนเต็มตัว** มีหัวและแขน |
| รวม | 29,509 | | |

สามชุดนี้หน้าตาต่างกันมาก ตัวเลขรวมก้อนเดียวจะกลบความต่างนี้
`check_map.py` จึงแยกรายงานทีละชุด

---

## 8. หน้าจอ

ซ้าย = กล้อง (ความจริง) · ขวา = เสียงล้วน (โมเดล) วาดบน **ตารางเดียวกัน 40x30**
เพื่อให้เทียบกันได้ตรง ๆ ไม่ใช่เอาภาพกล้องเต็มความละเอียดมาข่มภาพที่โมเดลทายได้

- **สีบอกระยะ** ฟ้า = ใกล้ ม่วง = ไกล สเกลตายตัว 40–200 ซม. ทุกเฟรม
  (ตายตัวเพื่อให้สีเฟรมนี้เทียบกับเฟรมอื่นได้ ถ้าปรับตามเฟรมจะเทียบไม่ได้)
- **ขนาดจุดบอกความมั่นใจ** ถ้าวาดทุกจุดเท่ากันหมด ขอบของก้อนจะดูคมชัด
  ราวกับโมเดลรู้แน่ ทั้งที่ตรงนั้นมันลังเลอยู่ — ภาพจะโกหกมากกว่าที่โมเดลโกหก
- **ความแรงเสียงสะท้อน** โหมดสดต้องเห็นค่านี้ ไม่งั้นแยกไม่ออกระหว่าง
  "ไม่มีอะไรอยู่ตรงนั้น" กับ "เซ็นเซอร์ไม่ได้ยินอะไรเลย" — สองอย่างนี้หน้าจอออกมาเหมือนกัน
- **ป้ายมุมขวาบน** เขียว = ช่วงที่กันไว้ (เชื่อได้) เหลือง = ช่วงที่เคยเทรน (ดีเกินจริง)

ข้อความบนจอเป็นภาษาอังกฤษเพราะ OpenCV วาดอักษรไทยไม่ได้ (ออกมาเป็น `?`)

---

## 9. ผลจริง (กันช่วง s1 ไว้ 6,944 เฟรม · เทรนจาก 22,565 เฟรม)

| | IoU | ระยะพลาด |
|---|---|---|
| ทายค่าเฉลี่ย | 0.308 | 28.2 ซม. |
| แม่แบบรู้ตำแหน่ง (โกง) | 0.731 | 8.8 ซม. |
| **โมเดล เสียงล้วน** | **0.659** | **6.4 ซม.** |
| โมเดล + สลับคลื่น | 0.248 | 29.1 ซม. |

**สลับคลื่นแล้วพังจาก 0.659 เหลือ 0.248** — ยืนยันว่าโมเดลใช้เสียงจริง ไม่ได้จำภาพเฉลี่ยไว้ตอบ

### ไล่คู่เทียบให้ละเอียดขึ้นเรื่อย ๆ

| ช่อง (มุม x ระยะ) | เฟรม/ช่อง | IoU | ระยะพลาด |
|---|---|---|---|
| 8 x 4 | 738 | 0.738 | 10.1 ซม. |
| 12 x 6 | 363 | 0.731 | 8.8 ซม. |
| 20 x 8 | 167 | **0.780** | 8.6 ซม. |
| 32 x 12 | 73 | 0.765 | 7.8 ซม. |
| **โมเดล** | | 0.659 | **6.4 ซม.** |

**รูปร่างแพ้ทุกความละเอียด แต่ระยะชนะทุกความละเอียด**

ระยะชนะเพราะ **เวลาเดินทางของเสียงวัดระยะได้ตรง ๆ** ละเอียดกว่าการหยอดลงช่องระยะ
ส่วนรูปร่างแพ้เพราะโมเดลต้องเดามุมเอาเอง ขณะที่คู่เทียบได้มุมจริงจากกล้องฟรี ๆ

### รูปร่างที่เห็นมาจากไหน (R² เทียบกับการตอบค่าเฉลี่ย)

| | โมเดล | เพดานถ้ารู้ของจริงฟรี |
|---|---|---|
| แนวนอน ซ้าย-ขวา | +0.534 | รู้มุมจริง **+0.809** |
| แนวตั้ง บน-ล่าง | +0.670 | รู้ระยะจริง +0.182 · +ชุด +0.280 · **+มุม +0.728** |

โมเดล **อยู่ใต้เพดานทั้งสองแกน** แปลว่าทุกอย่างที่เห็นบนจออธิบายได้หมดด้วย
"อยู่มุมไหน ไกลเท่าไร" ไม่มีส่วนไหนที่ต้องอ้างว่าเสียงมองเห็นรูปร่าง

ที่แนวตั้งดูเหมือนโมเดลเก่ง (+0.670 ขณะที่ระยะอย่างเดียวได้ +0.182) ไม่ใช่เพราะ
เสียงแยกบน-ล่างได้ — เสา 4 ต้นเรียงแนวนอน แยกบน-ล่างไม่ได้ในทางฟิสิกส์
แต่เพราะ **ความสูงในภาพเกาะไปกับระยะและมุม** (ยิ่งใกล้ยิ่งเต็มเฟรม อยู่ริมก็โดนตัด)
พอใส่มุมเข้าไปในเพดาน เพดานก็กระโดดเป็น +0.728 แซงโมเดลทันที

### แยกตามชุด

| ชุด | เฟรม | IoU | ระยะพลาด |
|---|---|---|---|
| `walk` | 865 | 0.833 | 5.4 ซม. |
| `grid` | 3,393 | 0.703 | 5.8 ซม. |
| `walk2` | 2,686 | **0.501** | 8.0 ซม. |

`walk2` ยากที่สุดเพราะคนอยู่ไกลกว่า เห็นเต็มตัว และท่าทางหลากหลายกว่า
ซึ่งบังเอิญเป็นชุดที่ **หน้าตาใกล้เคียงกับที่เห็นตอนยืนใช้งานจริงที่สุด**

---

## 10. สรุปตรง ๆ ว่าตอนนี้ได้อะไร ยังไม่ได้อะไร

**ได้จริง**
- เสียงบอก **อยู่ตรงไหน** และ **ไกลเท่าไร** ได้จริง ระยะแม่นกว่าคู่เทียบทุกตัว (6.4 ซม.)
- ผลไม่ได้มาจากการจำ — สลับคลื่นแล้วพังทันที
- ภาพออกมาเป็นกลุ่มจุดไล่เฉดตามระยะ เหมือนกล้อง depth ในระดับที่ฟิสิกส์ยอมให้

**ยังไม่ได้**
- **รูปร่างของวัตถุ** สิ่งที่เห็นเป็นก้อนคือรูปร่างเฉลี่ยที่จำมา ไม่ใช่สิ่งที่เสียงเห็น
  วัดแล้วยืนยัน: โมเดลอยู่ใต้เพดาน "รู้แค่ตำแหน่ง" ทั้งสองแกน
- แยกบน-ล่างไม่ได้เลย เพราะเสาเรียงแนวนอนล้วน

**ถ้าอยากได้รูปร่างจริง ต้องแก้ที่ฮาร์ดแวร์ ไม่ใช่ที่โมเดล**
- เสา 4 ต้นแนวนอนที่ 40 kHz แยกมุมได้ราว 4 องศา = ราว 7 ช่องของภาพ 40 ช่อง
- อยากได้แนวตั้ง ต้องมีเสาเรียงแนวตั้งด้วย — แผน 9 ตัว (3x3) ตอบโจทย์นี้ตรง ๆ
- อยากได้ละเอียดขึ้น ต้องกางอาเรย์ให้กว้างขึ้น หรือขึ้นความถี่

โมเดลนี้จึงเป็น **เพดานของฮาร์ดแวร์ชุดปัจจุบัน** ไม่ใช่เพดานของวิธีการ
