pawaritmuangrach/ultrasonic01/car/ROUND3.md

# รอบ 3 — สิ่งที่จะแก้ และชุดข้อมูลใหม่

บันทึกไว้ก่อนเก็บข้อมูล จะได้ไม่ลืมว่าจะแก้อะไรและทำไม

## ชุดข้อมูลใหม่ — และทำไมมันแก้ปัญหาใหญ่ของรอบ 2

**แผน: 5 ช่วง ช่วงละ 5 นาที ทำอะไรก็ได้ แต่ทำเหมือนกันทุกช่วง**

รอบ 2 พังตรงนี้: **หนึ่งช่วง = หนึ่งตำแหน่ง** กันช่วงหนึ่งไว้ทดสอบจึงเท่ากับ
กันตำแหน่งนั้นออกจากการเทรนทั้งหมด โมเดลต้องเดาข้ามไปยังที่ไม่เคยเห็น
หลักฐาน: แม้แต่แม่แบบที่รู้ตำแหน่งจริงยังได้ R2 ติดลบ 0.713

ต้องเลี่ยงด้วยการแบ่งตามเวลา (กัน 25% ท้ายของทุกช่วง) ซึ่งใช้ได้ แต่ยังมีจุดอ่อน
เพราะเฟรมทดสอบอยู่ในเซสชันเดียวกับเฟรมเทรน เสื้อผ้าเดิม ห้องเดิม แสงเดิม

**ชุดใหม่ทุกช่วงครอบคลุมเหมือนกัน จึงกันทั้งช่วงไว้ทดสอบได้ตรง ๆ**
เป็นการทดสอบที่สะอาดกว่า และเป็นวิธีที่ควรใช้ตั้งแต่แรก

## ข้อกังวลข้อเดียวของแผนนี้ — และวิธีกัน

"ทำอะไรก็ได้" ให้ **ตำแหน่ง** หลากหลายดี แต่มีโอกาสให้ **ท่าทาง** น้อยลง
ถ้าเดินไปมาเฉย ๆ ส่วนใหญ่จะเป็นท่ายืน ซึ่งเป็นท่าเดียวกันหมด

แต่เป้าหมายของเราคือให้เห็นท่ากางแขนกับท่าย่อตัว ถ้าข้อมูลมีท่าพวกนั้นน้อย
โมเดลก็เรียนไม่ได้ ไม่ว่า loss จะดีแค่ไหน

**ทางแก้: เปิดคิวท่าไว้ด้วย (`--poses`) แล้วเดินเปลี่ยนที่ไปด้วยระหว่างทำท่า**
จะได้ทั้งตำแหน่งหลากหลายและท่าหลากหลายในช่วงเดียวกัน

คำสั่งที่จะใช้

```
python car/record.py --port COM5 --name mix --sections 5 --minutes 5 --poses
```

- `--name mix` สำคัญ · `mapdata2.ROUNDS["r3"]` รอชุดชื่อ `mix_s1` ถึง `mix_s5`
- ขาไม่ต้องใส่แล้ว ค่าปริยายเป็น `35,34,32,33` ตรงกับ rig2 แล้ว
- ได้ราว 4,200 เฟรมต่อช่วง รวม ~21,000 เฟรม ใกล้เคียงรอบ 2 (22,375)

## แยกที่เก็บของแต่ละรอบแล้ว

ทำไปแล้วก่อนเก็บข้อมูล เพราะถ้าสร้างแคชทับ ข้อมูลกับโมเดลรอบ 2 จะหายทั้งคู่

| รอบ | ชุดข้อมูล | แคช | โมเดล |
|---|---|---|---|
| r2 | pose_s1-5 + free_s1-3 | `_map2_cache` | `_map2_model.pt` |
| **r3** | **mix_s1-5** | `_map2_cache_r3` | `_map2_model_r3.pt` |

ค่าปริยายคือ r3 · กลับไปใช้ของเก่าด้วย `MAP2_ROUND=r2`

## สี่อย่างที่จะแก้ตอนเทรน

เรียงตามผลกระทบที่คาดว่าจะได้ · **ทั้งสี่ข้อยังไม่ได้ทดลอง** เป็นการวิเคราะห์ว่า
loss ไม่ตรงกับสิ่งที่เราวัด ไม่ใช่ผลที่วัดมาแล้ว

### 1. เพิ่มพจน์ความสูงเงาเข้า loss

**ปัญหา: เราวัดท่าทางแต่ไม่เคยสอนท่าทางเลย** loss ปัจจุบันไม่มีคำว่าความสูง
อยู่เลยแม้แต่คำเดียว โมเดลจึงไม่เคยถูกบอกว่าท่าทางสำคัญ

```python
h_p = shadow_height(sigmoid(ol))
h_t = shadow_height(occ)
loss = bce + 2.0*l1 + 0.5*|h_p - h_t|
```

น่าจะได้ผลมากที่สุด เพราะตรงกับเป้าหมายที่ตั้งไว้ที่สุด

### 2. เพิ่ม Dice เข้าไปคู่กับ BCE

**ปัญหา: วัด IoU แต่สอนด้วย BCE ซึ่งเป็นคนละอย่าง**

วัดจากข้อมูลจริง: ช่องที่มีวัตถุเฉลี่ยแค่ **26.7%** ของภาพ
ทายว่า "ว่างทั้งภาพ" อย่างเดียว BCE ก็ดูดีเพราะถูก 73.3% ของช่อง
**แต่ IoU จะเป็นศูนย์** BCE ให้น้ำหนักทุกช่องเท่ากัน จึงถูกครอบงำด้วยพื้นหลัง

```python
dice = 1 - 2*(p*occ).sum() / (p.sum() + occ.sum() + 1)
loss = bce + dice + 2.0*l1
```

### 3. เลือกเช็คพอยต์ด้วย R2 ไม่ใช่ IoU

ตอนนี้เก็บรอบที่ IoU ดีที่สุด ซึ่งอาจทิ้งรอบที่ท่าทางดีกว่าไป
รอบ 2 เห็นชัด: รอบที่ 28 ได้ R2 -0.016 แต่รอบที่เก็บไว้ได้ -0.143

ควรเก็บทั้งสองแบบไว้เทียบ หรือเลือกด้วยคะแนนรวมที่ให้น้ำหนักท่าทางด้วย

### 4. ลองน้ำหนักของ l1 หลายค่า

เลข 2.0 ผมตั้งขึ้นมาเอง ไม่ได้ทดลอง · ควรลอง 1.0 / 2.0 / 4.0 แล้ววัด

## เรื่องฮาร์ดแวร์ที่เจอระหว่างวิเคราะห์ — ไม่เกี่ยวกับรอบนี้แต่ต้องจด

**สัญญาณใช้ไปแค่ 7.3 บิต จาก 12 บิตที่ ADC มี**

| | ค่า |
|---|---|
| ช่วงที่ ADC ให้ได้ | 0 - 4095 |
| ที่ใช้จริง | 1437 - 2318 |
| ไฟตรงที่ลอยอยู่ | 1889 (นิ่งมาก +-1) |
| สัญญาณแกว่ง (99%) | **+-80 นับ จากที่มีให้ +-2048** |
| จุดสูงสุด | +-451 นับ |

ใช้ไป **3.9%** ของช่วง ADC · จุดสูงสุดถึง 451 แปลว่า **เพิ่มอัตราขยายได้อีก
ราว 4.5 เท่าก่อนล้น** ซึ่งจะได้ความละเอียดเพิ่มอีก 2.2 บิต

แก้ที่บอร์ด ไม่ใช่ที่โมเดล · จดไว้ใช้ตอนออกแบบบอร์ดรุ่นถัดไป
บอร์ด main8 ที่ทำไว้ยังใช้อัตราขยายเดิม 1156 เท่า

## ลำดับที่จะทำ

1. เก็บข้อมูล 5 ช่วง (คำสั่งข้างบน) — ราว 30 นาทีรวมพัก
2. `python car/mapdata2.py` สร้างแคช r3
3. `python car/check_data2.py` ตรวจว่าท่าทางแยกจากตำแหน่งก่อนเทรน
4. แก้ loss ตามข้อ 1-2 แล้วเทรน
5. เทียบกับรอบ 2: IoU 0.555 · ระยะ 5.7 ซม. · ท่าทาง R2 +0.114

---

# ผลรอบสาม — สรุปหลังเทรนสามรัน

## ตัวเลขบน section 4 ซึ่งไม่ถูกแตะระหว่างเทรน

| รัน | เลือกเช็คพอยต์จาก | IoU | ระยะพลาด | **ท่าทาง R2** |
|---|---|---|---|---|
| รอบสอง (แบ่งตามเวลา) | **ชุดทดสอบเอง** | 0.555 | 5.7 ซม. | **+0.114** |
| รัน 1 | **ชุดทดสอบเอง** | 0.481 | 10.9 ซม. | −0.116 |
| รัน 2 (น้ำหนักท่าทาง 3.0) | ทั้ง section 5 | 0.397 | 15.9 ซม. | −0.086 |
| **รัน 3 (สะอาดที่สุด)** | **15% ท้ายของชุดเทรน** | **0.459** | **10.3 ซม.** | **+0.002** |
| คู่เทียบ ทายค่าเฉลี่ย | — | 0.232 | 28.2 ซม. | 0.000 |

**รัน 3 คือตัวเลขที่เชื่อถือได้ที่สุด** เพราะเป็นรันเดียวที่เช็คพอยต์ถูกเลือก
โดยไม่เคยเห็น section 4 เลย สองรันบนไม่ว่าจะได้เลขดีหรือแย่ ล้วนเลือกเช็คพอยต์
จากชุดเดียวกับที่ใช้รายงาน จึงมองข้ามไปได้

## ข้อสรุปเรื่องท่าทาง

**เสียงทายท่าทางไม่ได้ดีกว่าการเดาค่าเฉลี่ยเลย** R2 = +0.002 คือศูนย์พอดี

เลข +0.114 ของรอบสองที่เคยดูมีหวัง เกิดจากการเลือกเช็คพอยต์จากชุดทดสอบเอง
พอวัดด้วยวิธีที่สะอาด สัญญาณนั้นหายไป

ลองมาสามวิธีที่ต่างกันมาก — 5 การยิงต่อภาพ, LSTM ข้ามการยิง, พจน์ความสูงใน
loss, น้ำหนักสองระดับ — ผลคร่อมศูนย์ทุกครั้ง ไม่มีแนวโน้มดีขึ้น

## ข้อสรุปเรื่องที่ทำได้จริง

**ตำแหน่งกับระยะทำได้ดีและมั่นคงทุกรัน**

| | โมเดล | คู่เทียบ | ดีกว่า |
|---|---|---|---|
| รูปร่าง IoU | 0.459 | 0.232 | 2.0 เท่า |
| ระยะพลาด | 10.3 ซม. | 28.2 ซม. | 2.7 เท่า |

และสลับคลื่นแล้วพังทุกครั้ง (IoU 0.156 · ระยะ 37.0 ซม.) ยืนยันว่าใช้เสียงจริง
ไม่ได้จำภาพเฉลี่ย

## เรื่องฟิสิกส์ที่ผมเคยพูดผิด และขอแก้

**ผมเคยบอกว่าบอร์ด 8 หัวรับจะลดความเบลอลงครึ่งหนึ่ง — ผิด**

ความเบลอเชิงมุมขึ้นกับ **ความกว้างของอาเรย์** ไม่ใช่จำนวนหัวรับ
8 หัวรับวางในกรอบ 110 มม. เท่าเดิม ได้ความเบลอ 4.5 องศาเท่าเดิมทุกประการ

| ความกว้างอาเรย์ | ความเบลอ | ที่ระยะ 1.5 ม. แยกของห่างกันเกิน |
|---|---|---|
| **110 มม. (ตอนนี้)** | **4.5°** | **11.7 ซม.** |
| 220 มม. | 2.2° | 5.9 ซม. |
| 257 มม. | 1.9° | 5.0 ซม. |

แขนคนกว้างราว 15 ซม. ที่ระยะ 1.5 ม. จึงกินราว **1.3 ช่องความละเอียด**
ตามหลักฟิสิกส์แล้ว "พอเห็น" ว่ามีอะไรกว้างขึ้น แต่ไม่พอจะเห็นเป็นแขนแยกจากลำตัว
ถ้าอยากได้ 3 ช่องพาดแขน ต้องกางอาเรย์เป็น **257 มม. คือกว้างขึ้น 2.3 เท่า**

**สิ่งที่การเพิ่มจำนวนหัวรับช่วยได้จริง** คือกดทิศทางหลอก
ระยะห่างที่ไม่เกิดภาพหลอกคือครึ่งความยาวคลื่น = 4.3 มม. แต่หัวรับตัวหนึ่งกว้าง
ราว 16 มม. วางชิดขนาดนั้นไม่ได้ อาเรย์จึงมีช่องโหว่และเกิดทิศทางหลอกเสมอ
หัวรับมากขึ้นในกรอบที่กว้างขึ้น จึงช่วยทั้งสองเรื่องพร้อมกัน

## ที่ควรทำต่อ

1. **เก็บโมเดลรัน 3 ไว้ใช้งาน** ตำแหน่งกับระยะใช้ได้จริงแล้ว
2. **ถ้ายังอยากได้ท่าทาง ต้องแก้ที่ฮาร์ดแวร์ ไม่ใช่ที่โมเดล**
   กางอาเรย์ให้กว้างขึ้นราว 2.3 เท่า และใช้หัวรับ 8 ตัวกระจายในกรอบนั้น
   ซึ่งบอร์ด main8 รองรับอยู่แล้ว เหลือแค่การจัดวางทางกายภาพ
3. อย่าปรับ loss เพิ่มอีก — สามครั้งแล้วผลคร่อมศูนย์ ไม่ใช่ปัญหาการตั้งค่า
