pawaritmuangrach/ultrasonic01/pcb/out/main8/nets.md

# main8 — ตารางการต่อ

ไว้ไล่วัดด้วยมิเตอร์โหมดเสียงปี๊บ ขาในแถวเดียวกันต้องปี๊บถึงกันหมด
ขาคนละแถวต้องไม่ปี๊บ ถ้าปี๊บ = ลายช็อต

| เน็ต | ขาที่ต่อถึงกัน |
|---|---|
| `GND` | JA.1 · JA.2 · JB.19 · U1.7 · CD1.2 · CB1.2 · JP.2 · T1.2 · T2.2 · T3.2 · CF.2 · K1.2 · C1G1.2 · C1G2.2 · C1O.2 · K2.2 · C2G1.2 · C2G2.2 · C2O.2 · K3.2 · C3G1.2 · C3G2.2 · C3O.2 · K4.2 · C4G1.2 · C4G2.2 · C4O.2 · K5.2 · C5G1.2 · C5G2.2 · C5O.2 · K6.2 · C6G1.2 · C6G2.2 · C6O.2 · K7.2 · C7G1.2 · C7G2.2 · C7O.2 · K8.2 · C8G1.2 · C8G2.2 · C8O.2 · U2.11 · CD2.2 · U3.11 · CD3.2 · U4.11 · CD4.2 · U5.11 · CD5.2 · U6.11 · CD6.2 · RV2.2 · CV1.2 · CB2.2 |
| `MCU3V3` | JA.3 · JB.20 · RF.1 |
| `RX8_ADC` | JA.9 · R8O.2 · C8O.1 |
| `RX7_ADC` | JA.10 · R7O.2 · C7O.1 |
| `RX6_ADC` | JA.11 · R6O.2 · C6O.1 |
| `RX5_ADC` | JA.12 · R5O.2 · C5O.1 |
| `RX4_ADC` | JA.13 · R4O.2 · C4O.1 |
| `RX3_ADC` | JA.14 · R3O.2 · C3O.1 |
| `RX2_ADC` | JA.15 · R2O.2 · C2O.1 |
| `RX1_ADC` | JA.16 · R1O.2 · C1O.1 |
| `TX1_IN` | JB.14 · U1.1 |
| `TX2_IN` | JB.15 · U1.13 |
| `TX3_IN` | JB.16 · U1.5 |
| `P5V` | JB.18 · U1.14 · CD1.1 · CB1.1 · JP.1 |
| `TX1_MID` | U1.2 · U1.3 |
| `TX1_OUT` | U1.4 · RT1.1 |
| `TX1_DRV` | RT1.2 · T1.1 |
| `TX2_MID` | U1.12 · U1.11 |
| `TX2_OUT` | U1.10 · RT2.1 |
| `TX2_DRV` | RT2.2 · T2.1 |
| `TX3_MID` | U1.6 · U1.9 |
| `TX3_OUT` | U1.8 · RT3.1 |
| `TX3_DRV` | RT3.2 · T3.1 |
| `A3V3` | RF.2 · CF.1 · U2.4 · CD2.1 · U3.4 · CD3.1 · U4.4 · CD4.1 · U5.4 · CD5.1 · U6.4 · CD6.1 · RV1.1 |
| `RX1_IN` | K1.1 · C1I.1 |
| `RX1_G` | C1I.2 · R1B.1 · U2.3 |
| `RX1_S1O` | U2.1 · R1F1.1 · U2.5 |
| `RX1_S1N` | U2.2 · R1F1.2 · R1G1.1 |
| `RX1_G1` | R1G1.2 · C1G1.1 |
| `RX1_S2O` | U2.7 · R1F2.1 · R1O.1 |
| `RX1_S2N` | U2.6 · R1F2.2 · R1G2.1 |
| `RX1_G2` | R1G2.2 · C1G2.1 |
| `RX2_IN` | K2.1 · C2I.1 |
| `RX2_G` | C2I.2 · R2B.1 · U2.10 |
| `RX2_S1O` | U2.8 · R2F1.1 · U2.12 |
| `RX2_S1N` | U2.9 · R2F1.2 · R2G1.1 |
| `RX2_G1` | R2G1.2 · C2G1.1 |
| `RX2_S2O` | U2.14 · R2F2.1 · R2O.1 |
| `RX2_S2N` | U2.13 · R2F2.2 · R2G2.1 |
| `RX2_G2` | R2G2.2 · C2G2.1 |
| `RX3_IN` | K3.1 · C3I.1 |
| `RX3_G` | C3I.2 · R3B.1 · U3.3 |
| `RX3_S1O` | U3.1 · R3F1.1 · U3.5 |
| `RX3_S1N` | U3.2 · R3F1.2 · R3G1.1 |
| `RX3_G1` | R3G1.2 · C3G1.1 |
| `RX3_S2O` | U3.7 · R3F2.1 · R3O.1 |
| `RX3_S2N` | U3.6 · R3F2.2 · R3G2.1 |
| `RX3_G2` | R3G2.2 · C3G2.1 |
| `RX4_IN` | K4.1 · C4I.1 |
| `RX4_G` | C4I.2 · R4B.1 · U3.10 |
| `RX4_S1O` | U3.8 · R4F1.1 · U3.12 |
| `RX4_S1N` | U3.9 · R4F1.2 · R4G1.1 |
| `RX4_G1` | R4G1.2 · C4G1.1 |
| `RX4_S2O` | U3.14 · R4F2.1 · R4O.1 |
| `RX4_S2N` | U3.13 · R4F2.2 · R4G2.1 |
| `RX4_G2` | R4G2.2 · C4G2.1 |
| `RX5_IN` | K5.1 · C5I.1 |
| `RX5_G` | C5I.2 · R5B.1 · U4.3 |
| `RX5_S1O` | U4.1 · R5F1.1 · U4.5 |
| `RX5_S1N` | U4.2 · R5F1.2 · R5G1.1 |
| `RX5_G1` | R5G1.2 · C5G1.1 |
| `RX5_S2O` | U4.7 · R5F2.1 · R5O.1 |
| `RX5_S2N` | U4.6 · R5F2.2 · R5G2.1 |
| `RX5_G2` | R5G2.2 · C5G2.1 |
| `RX6_IN` | K6.1 · C6I.1 |
| `RX6_G` | C6I.2 · R6B.1 · U4.10 |
| `RX6_S1O` | U4.8 · R6F1.1 · U4.12 |
| `RX6_S1N` | U4.9 · R6F1.2 · R6G1.1 |
| `RX6_G1` | R6G1.2 · C6G1.1 |
| `RX6_S2O` | U4.14 · R6F2.1 · R6O.1 |
| `RX6_S2N` | U4.13 · R6F2.2 · R6G2.1 |
| `RX6_G2` | R6G2.2 · C6G2.1 |
| `RX7_IN` | K7.1 · C7I.1 |
| `RX7_G` | C7I.2 · R7B.1 · U5.3 |
| `RX7_S1O` | U5.1 · R7F1.1 · U5.5 |
| `RX7_S1N` | U5.2 · R7F1.2 · R7G1.1 |
| `RX7_G1` | R7G1.2 · C7G1.1 |
| `RX7_S2O` | U5.7 · R7F2.1 · R7O.1 |
| `RX7_S2N` | U5.6 · R7F2.2 · R7G2.1 |
| `RX7_G2` | R7G2.2 · C7G2.1 |
| `RX8_IN` | K8.1 · C8I.1 |
| `RX8_G` | C8I.2 · R8B.1 · U5.10 |
| `RX8_S1O` | U5.8 · R8F1.1 · U5.12 |
| `RX8_S1N` | U5.9 · R8F1.2 · R8G1.1 |
| `RX8_G1` | R8G1.2 · C8G1.1 |
| `RX8_S2O` | U5.14 · R8F2.1 · R8O.1 |
| `RX8_S2N` | U5.13 · R8F2.2 · R8G2.1 |
| `RX8_G2` | R8G2.2 · C8G2.1 |
| `MID` | RV1.2 · RV2.1 · U6.3 |
| `VREF` | R1B.2 · R2B.2 · R3B.2 · R4B.2 · R5B.2 · R6B.2 · R7B.2 · R8B.2 · U6.1 · U6.2 · CV1.1 · CB2.1 · U6.5 · U6.6 · U6.7 · U6.10 · U6.9 · U6.8 · U6.12 · U6.13 · U6.14 |
| `NC_JA_R` | JA.4 |
| `NC_JA_B11` | JA.5 |
| `NC_JA_B10` | JA.6 |
| `NC_JA_B1` | JA.7 |
| `NC_JA_B0` | JA.8 |
| `NC_JA_C15` | JA.17 |
| `NC_JA_C14` | JA.18 |
| `NC_JA_C13` | JA.19 |
| `NC_JA_VB` | JA.20 |
| `NC_JB_B12` | JB.1 |
| `NC_JB_B13` | JB.2 |
| `NC_JB_B14` | JB.3 |
| `NC_JB_B15` | JB.4 |
| `NC_JB_A8` | JB.5 |
| `NC_JB_A9` | JB.6 |
| `NC_JB_A10` | JB.7 |
| `NC_JB_A11` | JB.8 |
| `NC_JB_A12` | JB.9 |
| `NC_JB_A15` | JB.10 |
| `NC_JB_B3` | JB.11 |
| `NC_JB_B4` | JB.12 |
| `NC_JB_B5` | JB.13 |
| `NC_JB_B9` | JB.17 |
