pawaritmuangrach/ultrasonic01/pcb/out/rx2/nets.md

# rx2 — ตารางการต่อ

ไว้ไล่วัดด้วยมิเตอร์โหมดเสียงปี๊บ ขาในแถวเดียวกันต้องปี๊บถึงกันหมด
ขาคนละแถวต้องไม่ปี๊บ ถ้าปี๊บ = ลายช็อต

| เน็ต | ขาที่ต่อถึงกัน |
|---|---|
| `3V3` | U1.4 · C1.1 · C2.1 · J1.1 |
| `CH1_IN` | K1.1 · C11.1 |
| `CH1_G` | C11.2 · R1B.1 · U1.3 |
| `CH1_S1O` | U1.1 · R1F1.1 · U1.5 |
| `CH1_S1N` | U1.2 · R1F1.2 · R1G1.1 |
| `CH1_G1` | R1G1.2 · C1G1.1 |
| `CH1_S2O` | U1.7 · R1F2.1 · R1O.1 |
| `CH1_S2N` | U1.6 · R1F2.2 · R1G2.1 |
| `CH1_G2` | R1G2.2 · C1G2.1 |
| `CH1_OUT` | R1O.2 · C1O.1 · J2.1 |
| `CH2_IN` | K2.1 · C21.1 |
| `CH2_G` | C21.2 · R2B.1 · U1.10 |
| `CH2_S1O` | U1.8 · R2F1.1 · U1.12 |
| `CH2_S1N` | U1.9 · R2F1.2 · R2G1.1 |
| `CH2_G1` | R2G1.2 · C2G1.1 |
| `CH2_S2O` | U1.14 · R2F2.1 · R2O.1 |
| `CH2_S2N` | U1.13 · R2F2.2 · R2G2.1 |
| `CH2_G2` | R2G2.2 · C2G2.1 |
| `CH2_OUT` | R2O.2 · C2O.1 · J2.2 |
| `GND` | U1.11 · C1.2 · C2.2 · J1.2 · J2.3 · K1.2 · C1G1.2 · C1G2.2 · C1O.2 · K2.2 · C2G1.2 · C2G2.2 · C2O.2 |
| `VREF` | J1.3 · R1B.2 · R2B.2 |
