pawaritmuangrach/ultrasonic01/pcb/out/vref/nets.md

# vref — ตารางการต่อ

ไว้ไล่วัดด้วยมิเตอร์โหมดเสียงปี๊บ ขาในแถวเดียวกันต้องปี๊บถึงกันหมด
ขาคนละแถวต้องไม่ปี๊บ ถ้าปี๊บ = ลายช็อต

| เน็ต | ขาที่ต่อถึงกัน |
|---|---|
| `3V3` | U1.4 · R1.1 · C1.1 · C2.1 · J1.1 · J2.1 · J3.1 · J4.1 · J5.1 |
| `GND` | U1.11 · R2.2 · C1.2 · C2.2 · C3.2 · C4.2 · J1.2 · J2.2 · J3.2 · J4.2 · J5.2 |
| `MID` | R1.2 · R2.1 · U1.3 |
| `VREF` | U1.1 · U1.2 · C3.1 · C4.1 · U1.5 · U1.6 · U1.7 · U1.10 · U1.9 · U1.8 · U1.12 · U1.13 · U1.14 · J2.3 · J3.3 · J4.3 · J5.3 |
