pawaritmuangrach/ultrasonic01/pcb/out/main8/preview.png

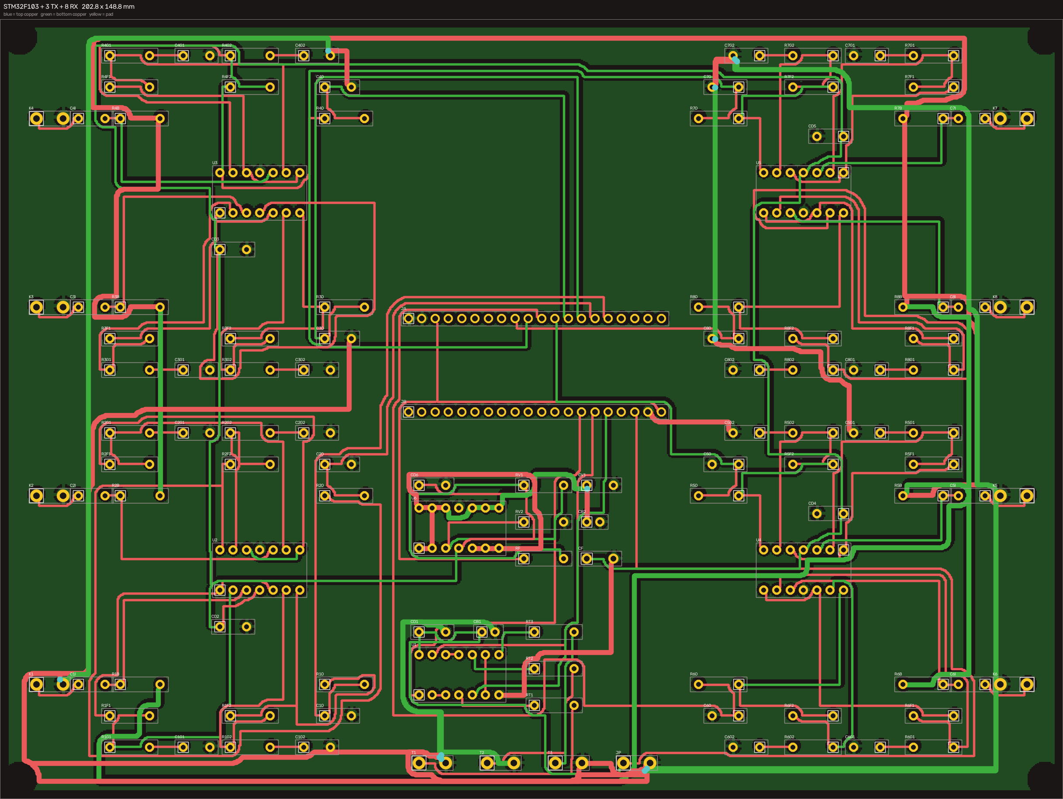
pcb/out/main8/preview.png
