pawaritmuangrach/ultrasonic01/pcb/out/main8/schematic-2-rx-channel.png

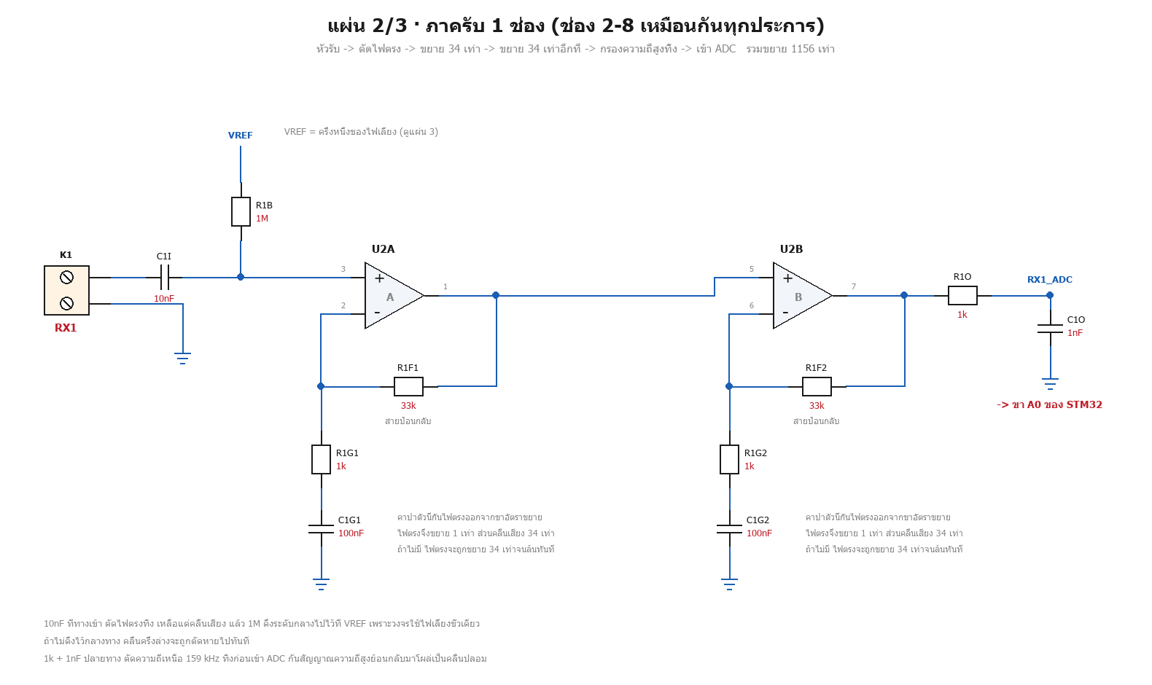
pcb/out/main8/schematic-2-rx-channel.png
