pawaritmuangrach/ultrasonic01/pcb/out/main8/schematic-4-rx-grid.png

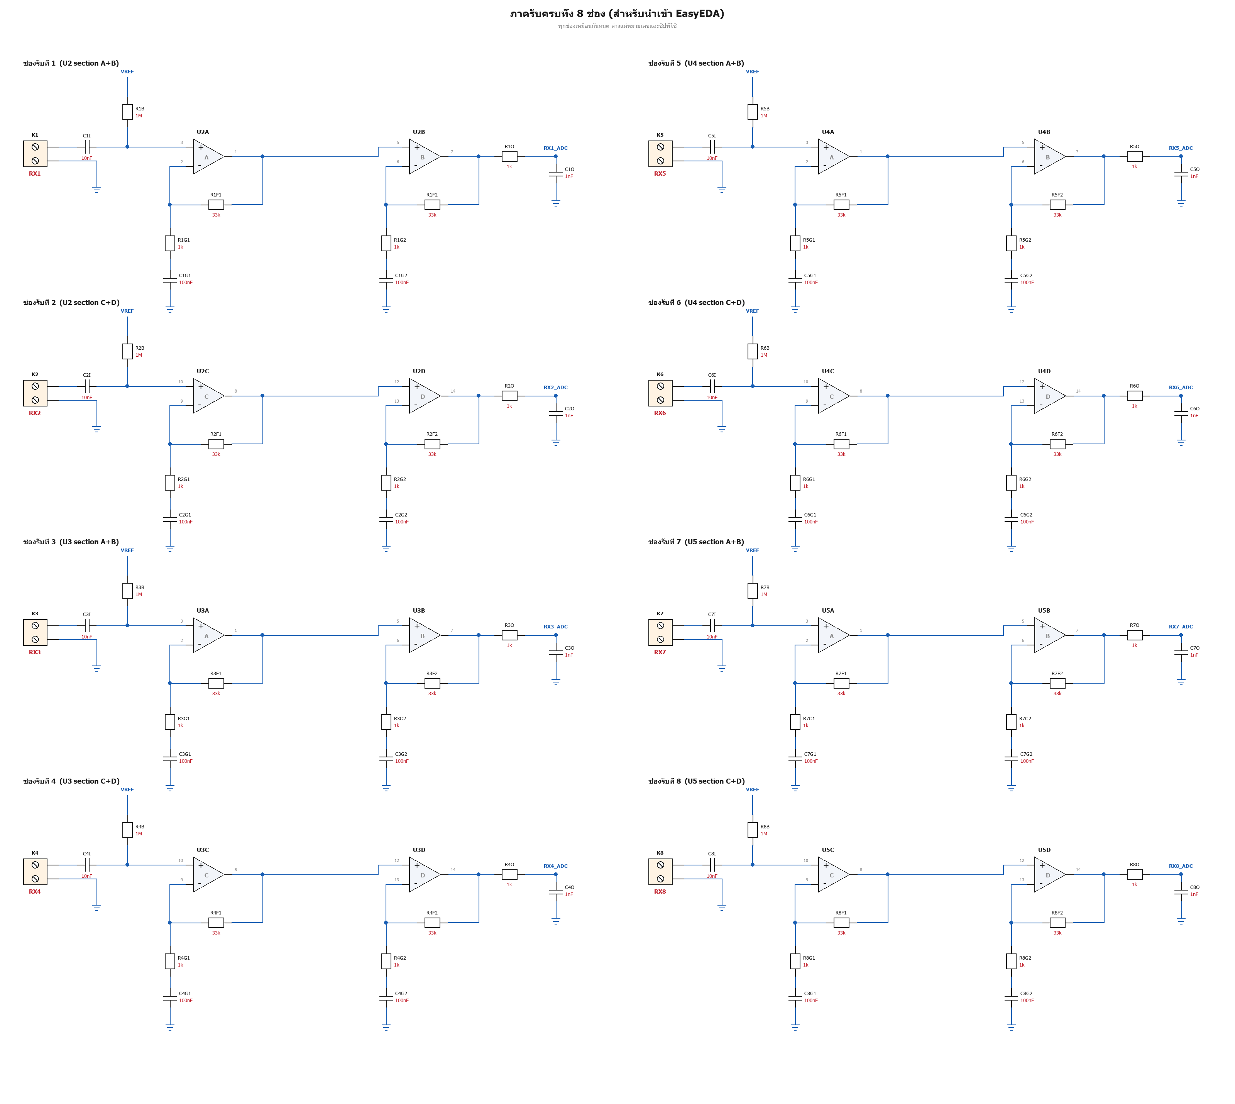
pcb/out/main8/schematic-4-rx-grid.png
