pawaritmuangrach/ultrasonic01/pcb/out/rx2/preview.png

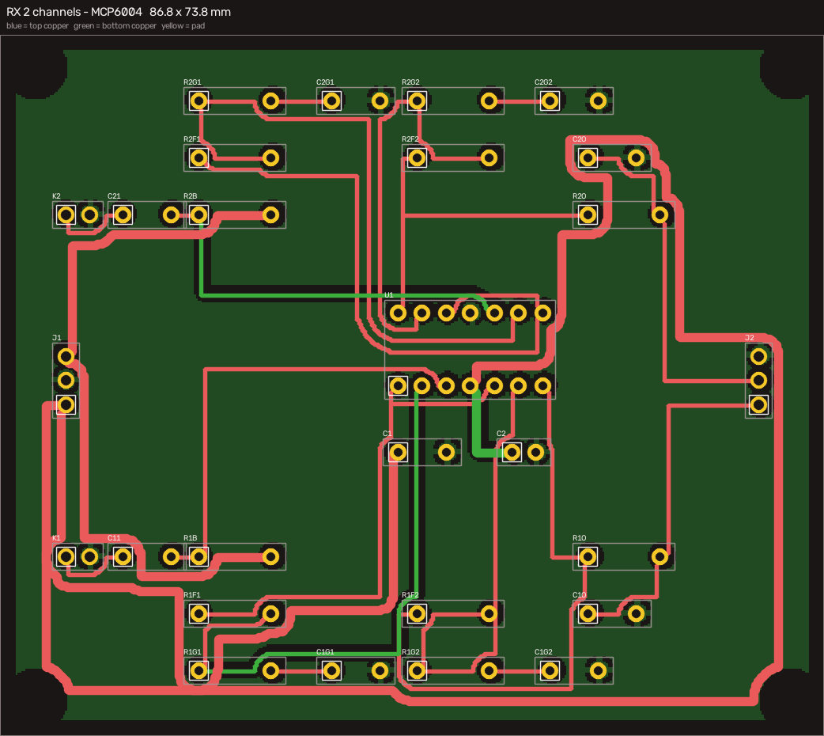
pcb/out/rx2/preview.png
