pawaritmuangrach/ultrasonic01/pcb/out/tx3/preview.png

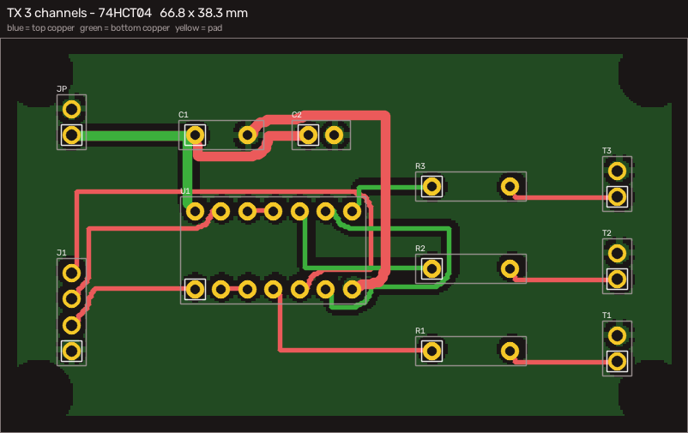
pcb/out/tx3/preview.png
