pawaritmuangrach/ultrasonic01/pcb/out/vref/preview.png

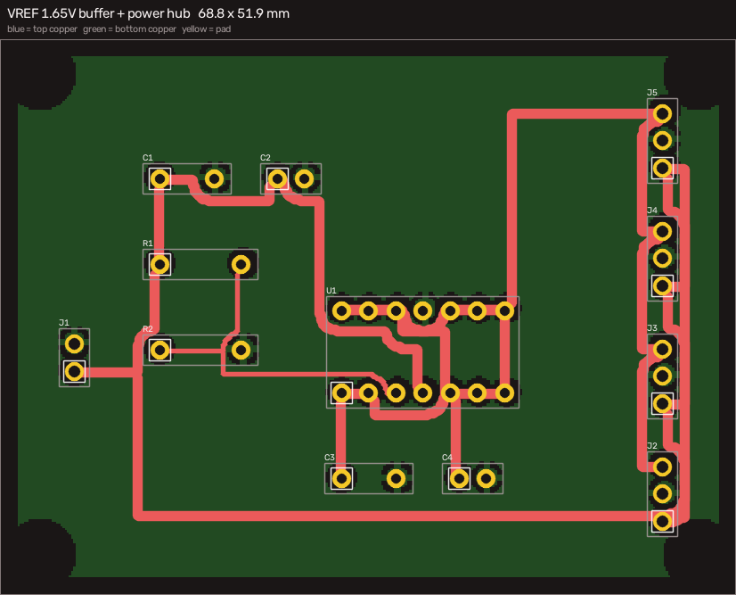
pcb/out/vref/preview.png
