pawaritmuangrach/ultrasonic01/pcb/out/main8/assembly.png

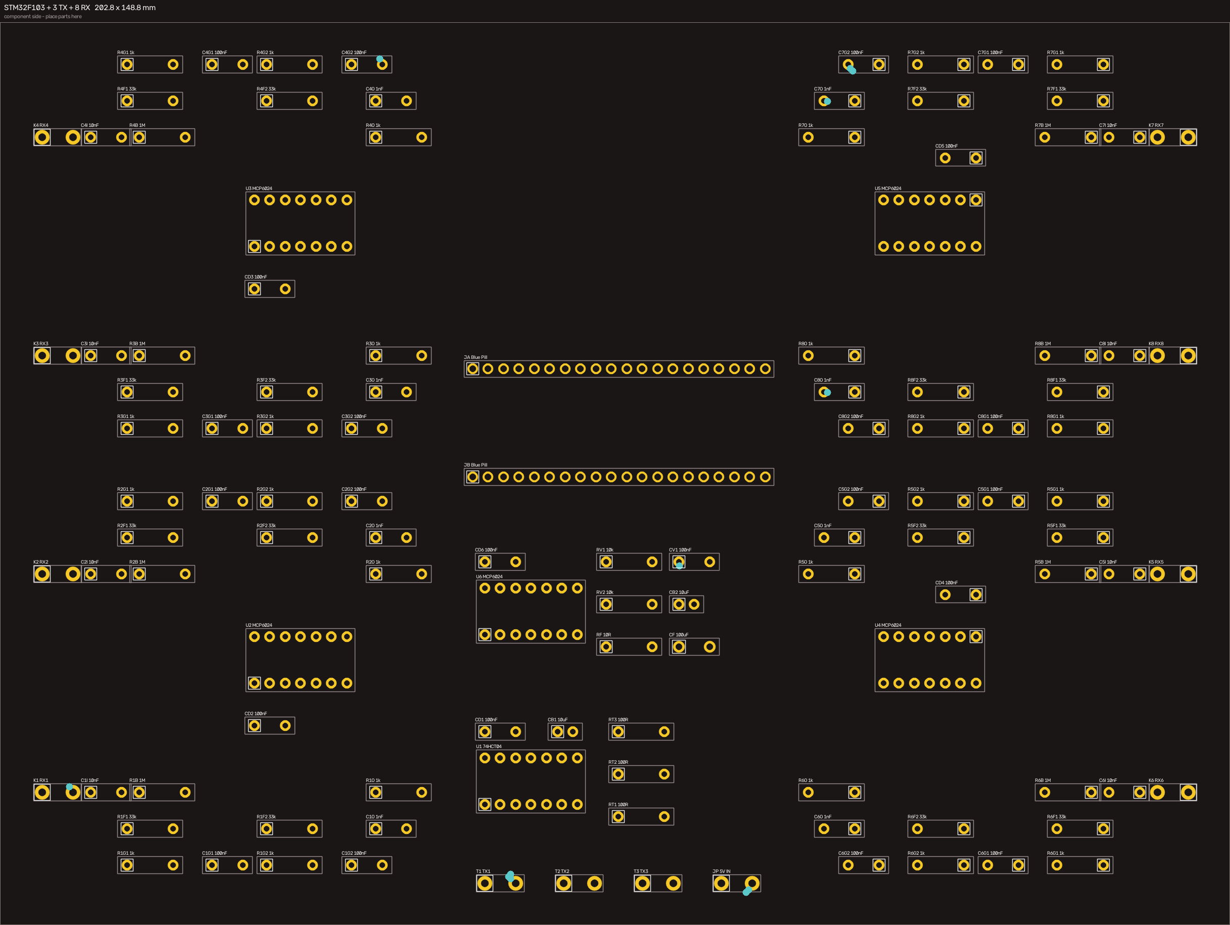
pcb/out/main8/assembly.png
