pawaritmuangrach/ultrasonic01/pcb/out/rx2/assembly.png

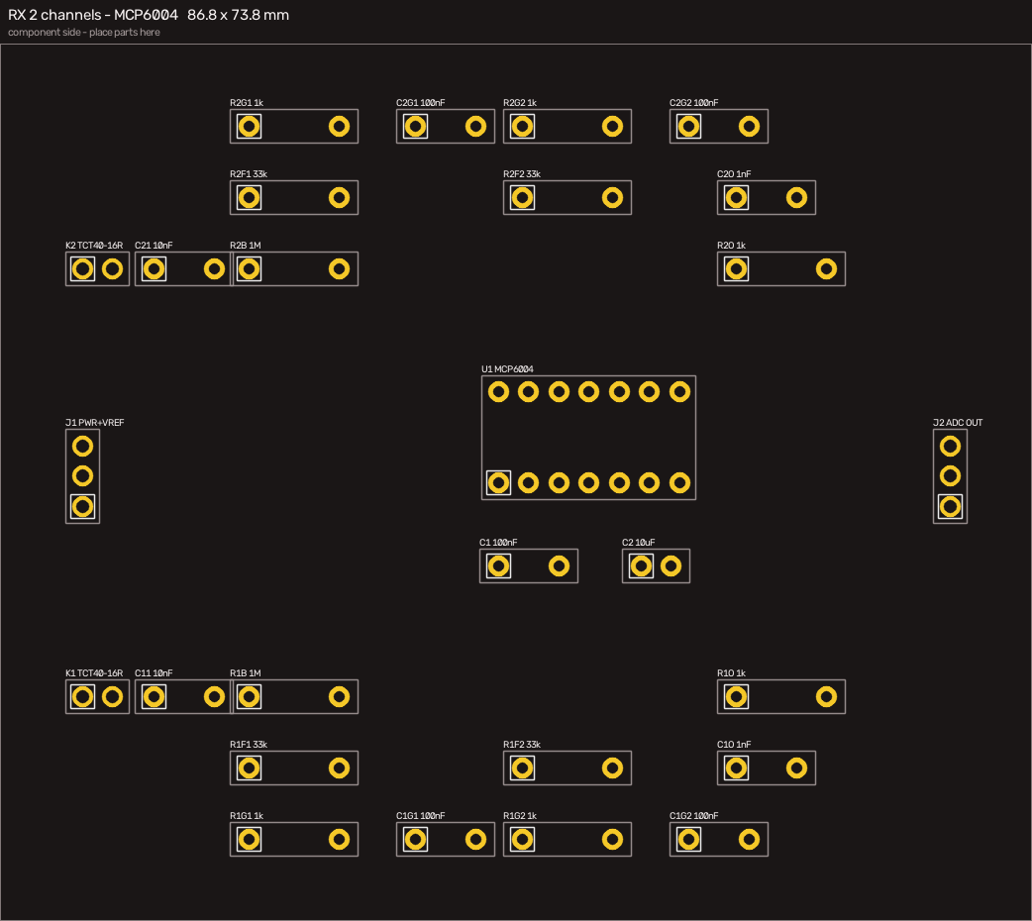
pcb/out/rx2/assembly.png
