pawaritmuangrach/ultrasonic01/pcb/out/tx3/assembly.png

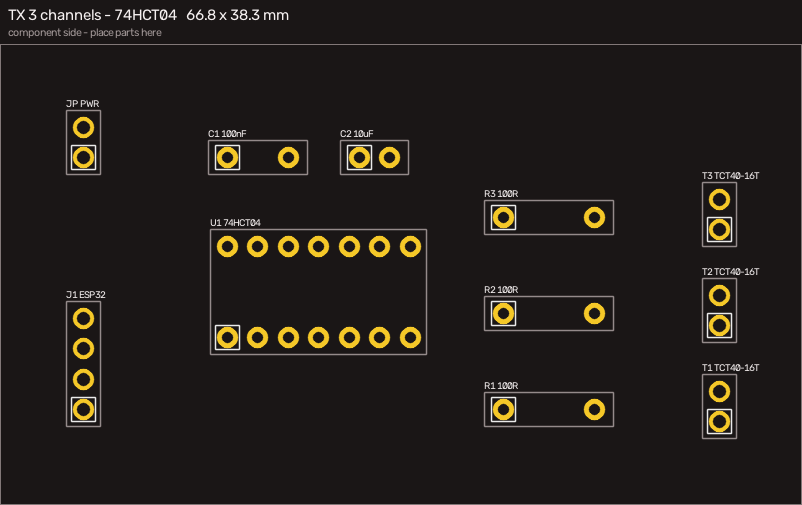
pcb/out/tx3/assembly.png
