pawaritmuangrach/ultrasonic01/pcb/out/vref/assembly.png

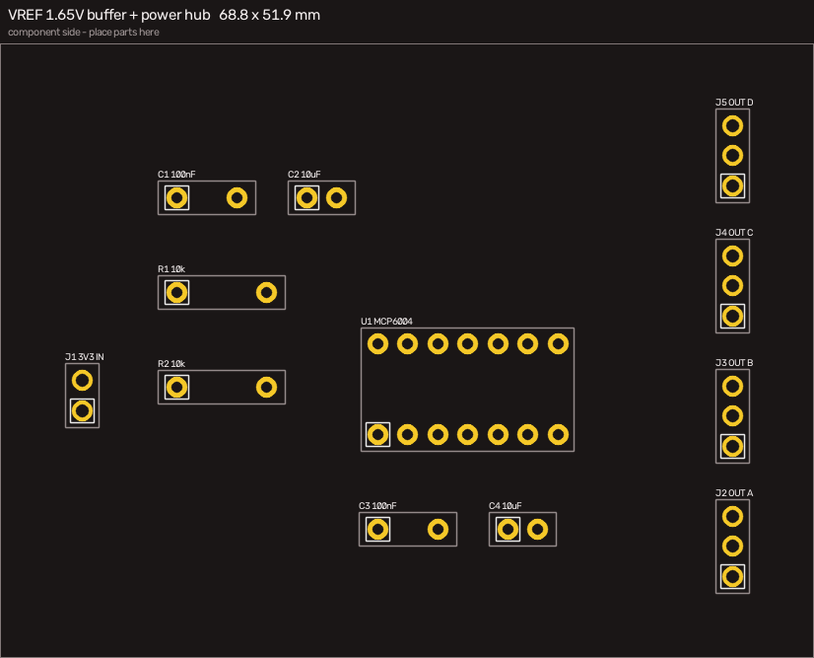
pcb/out/vref/assembly.png
