pawaritmuangrach/ultrasonic01/pcb/guide.py

"""สร้างคู่มือซื้อของและประกอบบอร์ด จาก netlist.py โดยตรง

    python pcb/guide.py

ทำไมต้องสร้างด้วยโค้ด ไม่พิมพ์เอง:
  จำนวนชิ้นส่วนกับรายชื่ออ้างอิงต้องตรงกับบอร์ดเป๊ะ ๆ ถ้าพิมพ์มือแล้ววันหนึ่ง
  แก้วงจร คู่มือจะค้างอยู่ที่ตัวเลขเก่าโดยไม่มีใครรู้ แล้วไปซื้อของผิดจำนวน
  ที่นี่ตัวเลขทุกตัวนับจาก netlist ตอนสร้างไฟล์ จึงตรงเสมอ

ส่วนคำแนะนำว่า "ซื้อของแบบไหน" เป็นความรู้ที่โค้ดไม่รู้ จึงเขียนไว้ในตาราง
SPEC ข้างล่าง แต่ผูกกับ (ค่า, ตัวถัง) ถ้าวงจรมีค่าใหม่ที่ยังไม่ได้เขียนไว้
จะฟ้องทันที ไม่ปล่อยผ่านเป็นช่องว่าง
"""
import os
from collections import defaultdict

import netlist as N

OUT = os.path.join(os.path.dirname(os.path.abspath(__file__)), "out", "main8")

# ตัวถัง -> คำที่ใช้ค้นในคลัง EasyEDA · ระยะขาคือตัวตัดสิน ไม่ใช่ชื่อ
EDA_FP = {
    "R_AXIAL": ("AXIAL-0.3", "ระยะขา 7.62 มม."),
    "C_DISC": ("RAD-0.2", "ระยะขา 5.08 มม."),
    "C_ELEC": ("RAD-0.1", "ระยะขา 2.54 มม."),
    "C_BULK": ("RAD-0.2", "ระยะขา 5.08 มม."),
    "DIP14": ("DIP-14", "ขา 2.54 แถวห่าง 7.62 มม."),
    "HDR20": ("HDR-1X20 ตัวเมีย", "ขา 2.54 มม."),
    "TERM2": ("KF301-5.0-2P", "ระยะขา 5.08 มม."),
}

# (ค่า, ตัวถัง) -> (ของที่ต้องซื้อ, เหตุผล/ข้อควรระวัง)
SPEC = {
    ("1M", "R_AXIAL"): (
        "ตัวต้านทาน 1M โอห์ม 1/4W",
        "ค่าคลาดเคลื่อน 5% พอ ตัวนี้แค่ดึงระดับกลาง ไม่ได้กำหนดอัตราขยาย"),
    ("33k", "R_AXIAL"): (
        "ตัวต้านทาน 33k โอห์ม 1/4W **ความคลาดเคลื่อน 1%**",
        "**คู่นี้กำหนดอัตราขยาย** ถ้าใช้ 5% แต่ละช่องจะขยายไม่เท่ากัน "
        "แล้วการเทียบความแรงระหว่างช่องจะเพี้ยน ซึ่งเป็นหัวใจของการหาทิศทาง"),
    ("1k", "R_AXIAL"): (
        "ตัวต้านทาน 1k โอห์ม 1/4W **ความคลาดเคลื่อน 1%**",
        "ตัวที่ลงท้าย G1/G2 คู่กับ 33k กำหนดอัตราขยาย · "
        "ตัวที่ลงท้าย O เป็นตัวกรองปลายทาง ใช้ 5% ก็ได้ แต่ซื้อ 1% ทั้งหมด"
        "ง่ายกว่าแยกสองแบบ"),
    ("10k", "R_AXIAL"): (
        "ตัวต้านทาน 10k โอห์ม 1/4W **ความคลาดเคลื่อน 1%**",
        "สองตัวนี้แบ่งไฟครึ่งหนึ่งเป็นแรงดันอ้างอิง ถ้าไม่เท่ากันจุดกลาง"
        "จะเลื่อน แล้วคลื่นจะถูกตัดข้างเดียวก่อนถึงจุดสูงสุด"),
    ("100R", "R_AXIAL"): (
        "ตัวต้านทาน 100 โอห์ม 1/4W",
        "กันกระแสพุ่งตอนขับหัวส่ง 5% พอ"),
    ("10R", "R_AXIAL"): (
        "ตัวต้านทาน 10 โอห์ม 1/4W",
        "คั่นไฟแอนะล็อกออกจากไฟดิจิทัล 5% พอ"),
    ("100nF", "C_DISC"): (
        "คาปาเซรามิก 100nF 50V ระยะขา 5.08 มม.",
        "X7R ใช้ได้ · ตัวที่ขึ้นต้น CD คือคาปาประกบชิป **ต้องอยู่ชิดขาชิป**"),
    ("10nF", "C_DISC"): (
        "คาปาเซรามิก 10nF 50V ระยะขา 5.08 มม. **ถ้าหาชนิด C0G/NP0 ได้ยิ่งดี**",
        "แปดตัวนี้คือทางเข้าของทั้งแปดช่อง ถ้าค่าไม่เท่ากันแต่ละช่องจะตอบสนอง"
        "ความถี่ต่างกันเล็กน้อย C0G นิ่งกว่า X7R มากทั้งเรื่องอุณหภูมิและแรงดัน"),
    ("1nF", "C_DISC"): (
        "คาปาเซรามิก 1nF 50V ระยะขา 5.08 มม. **C0G/NP0 ถ้าหาได้**",
        "ตัวกรองก่อนเข้า ADC เหตุผลเดียวกับ 10nF"),
    ("10uF", "C_ELEC"): (
        "คาปาอิเล็กโทรไลต์ 10uF 25V ระยะขา 2.54 มม.",
        "**มีขั้ว ใส่กลับด้านแล้วระเบิด** ขายาว = บวก · บนบอร์ดขา 1 คือบวก"),
    ("100uF", "C_BULK"): (
        "คาปาอิเล็กโทรไลต์ 100uF 16V ระยะขา 5.08 มม.",
        "**มีขั้ว** ตัวนี้อยู่บนราง 3.3V จะใช้ 16V หรือ 25V ก็ได้"),
    ("MCP6024-I/P", "DIP14"): (
        "MCP6024-I/P ตัวถัง DIP-14",
        "**ต้องมี -I/P ต่อท้าย** ไม่งั้นได้ตัวถังติดผิวหน้ามาเสียบไม่ได้ · "
        "ต้องการแบนด์วิดท์ 34 x 40kHz = 1.36 MHz ตัวนี้ให้ 10 MHz เหลือเฟือ"),
    ("SN74HCT04N", "DIP14"): (
        "SN74HCT04N ตัวถัง DIP-14",
        "**ต้องเป็น HCT ห้ามใช้ HC** เพราะ STM32 ส่งสัญญาณมาที่ 3.3V "
        "แต่ชิปตัวนี้กินไฟ 5V · HCT รับระดับสูงตั้งแต่ 2V ขึ้นไปจึงอ่านได้ "
        "ส่วน HC ต้องการถึง 3.5V จะอ่านสัญญาณ 3.3V ไม่ออก"),
    ("1x20 female hdr", "HDR20"): (
        "เฮดเดอร์ตัวเมีย 1x20 ขา ระยะ 2.54 มม. (ตัดจากแถบยาวได้)",
        "สองแถวห่างกัน 17.78 มม. สำหรับเสียบ Blue Pill · "
        "**อย่าบัดกรีบอร์ด STM32 ลงไปตรง ๆ** จะถอดไปแฟลชไม่ได้"),
}


def rows():
    b = N.BOARDS["main8"]()
    g = defaultdict(list)
    for ref, val, fp in b["parts"]:
        key = (val, fp) if fp != "TERM2" else ("เทอร์มินอลขันสกรู", fp)
        g[key].append(ref)
    missing = [k for k in g if k not in SPEC and k[1] != "TERM2"]
    if missing:
        raise SystemExit(f"ยังไม่ได้เขียนคำแนะนำของ {missing} ใน SPEC")
    return b, g


def natural(ref):
    """เรียงชื่ออ้างอิงให้ R2B มาก่อน R10B ไม่ใช่เรียงตามตัวอักษรล้วน"""
    import re
    return [int(t) if t.isdigit() else t for t in re.split(r"(\d+)", ref)]


def main():
    b, g = rows()
    L = []
    A = L.append
    A("# main8 — คู่มือซื้อของและประกอบ")
    A("")
    A("สร้างจาก `netlist.py` โดยตรง จำนวนและรายชื่อทุกตัวจึงตรงกับบอร์ดเสมอ")
    A("")
    A("## 1 · รายการที่ต้องซื้อ")
    A("")
    A("| ต้องซื้อ | จำนวน | ค้นในคลัง EasyEDA | ตัวไหนบ้าง |")
    A("|---|---|---|---|")
    order = sorted(g, key=lambda k: (k[1], k[0]))
    for key in order:
        val, fp = key
        refs = sorted(g[key], key=natural)
        eda, dim = EDA_FP[fp]
        if fp == "TERM2":
            buy = "เทอร์มินอลบล็อกขันสกรู 2 ขา KF301"
        else:
            buy = SPEC[key][0]
        rs = " ".join(refs)
        if len(rs) > 90:
            rs = rs[:88] + " …"
        A(f"| {buy} | **{len(refs)}** | `{eda}` · {dim} | {rs} |")
    A("")
    A("**ดูระยะขาเป็นตัวตัดสิน ไม่ใช่ดูชื่อ** ถ้าระยะไม่ตรง รูบนบอร์ดจะไม่ลง")
    A("")
    A("**ซื้อเผื่อไว้ด้วย** ตัวต้านทานกับคาปาเซรามิกขายเป็นแพ็คอยู่แล้ว "
      "ซื้อเผื่ออีก 20% ไม่ได้แพงขึ้นเท่าไร แต่ถ้าขาดกลางคันต้องรอของอีกรอบ")
    A("ส่วนชิปกับเทอร์มินอลซื้อเผื่ออย่างละ 1-2 ตัวพอ")
    A("")
    A("### นอกเหนือจากบนบอร์ด")
    A("")
    A("| ของ | จำนวน | หมายเหตุ |")
    A("|---|---|---|")
    A("| บอร์ด STM32F103C8T6 (Blue Pill) | 1 | เสียบลงเฮดเดอร์ JA JB |")
    A("| ST-Link V2 | 1 | ใช้แฟลชโปรแกรม · ต่อ 3.3V GND "
      "SWDIO=PA13 SWCLK=PA14 และตั้ง BOOT0=0 |")
    A("| หัวส่งอัลตราโซนิก 40 kHz | 3 | ต่อที่ TX1 TX2 TX3 |")
    A("| หัวรับอัลตราโซนิก 40 kHz | 8 | ต่อที่ RX1 ถึง RX8 |")
    A("| ไฟเลี้ยง 5V | 1 | ต่อที่ JP · กินราว 100 mA |")
    A("")
    A("## 2 · เหตุผลของแต่ละตัว และข้อควรระวัง")
    A("")
    for key in order:
        if key[1] == "TERM2":
            continue
        buy, why = SPEC[key]
        A(f"**{buy}**  ({len(g[key])} ตัว)")
        A("")
        A(f"{why}")
        A("")
    A("## 3 · สามอย่างที่ใส่กลับด้านแล้วพัง")
    A("")
    A("ที่เหลือใส่กลับด้านได้ไม่เป็นไร แต่สามกลุ่มนี้ต้องดูให้ดี")
    A("")
    A("| ตัว | ดูยังไง |")
    A("|---|---|")
    A("| **ชิปทั้ง 6 ตัว** (U1-U6) | บนบอร์ดมี**จุดวงกลมเล็กพิมพ์ไว้ข้างขา 1** "
      "ให้ตรงกับรอยบากหรือจุดบนตัวชิป |")
    A("| **คาปาอิเล็กโทรไลต์** (CB1 CB2 CF) | ขายาว = บวก · "
      "ข้างตัวมีแถบขาวชี้ขาลบ · บนบอร์ดขา 1 คือบวก |")
    A("| **เทอร์มินอล** (T1-T3 K1-K8 JP) | ช่องเสียบสายต้องหันออกนอกบอร์ด "
      "ไม่ใช่หันเข้าใน |")
    A("")
    A("## 4 · ลำดับการบัดกรี")
    A("")
    A("บัดกรีจากตัวเตี้ยไปตัวสูง ตัวเตี้ยจะได้ไม่ถูกตัวสูงบัง")
    A("")
    A("1. ตัวต้านทานทั้งหมด (54 ตัว) — เตี้ยที่สุด นอนราบกับบอร์ด")
    A("2. ชิป 6 ตัว — **ดูจุดขา 1**")
    A("3. คาปาเซรามิก (39 ตัว)")
    A("4. คาปาอิเล็กโทรไลต์ 3 ตัว — **ดูขั้ว**")
    A("5. เฮดเดอร์ตัวเมีย JA JB — เสียบ Blue Pill ทาบไว้ก่อนบัดกรี "
      "จะได้แถวตรงและระยะพอดี")
    A("6. เทอร์มินอล 12 ตัว — สูงที่สุด บัดกรีท้ายสุด")
    A("")
    A("## 5 · ตรวจก่อนจ่ายไฟครั้งแรก")
    A("")
    A("**ยังไม่ต้องเสียบ Blue Pill และยังไม่ต้องต่อหัวส่งหัวรับ**")
    A("")
    A("1. ตั้งมัลติมิเตอร์เป็นวัดความต่อเนื่อง วัดระหว่างขา 5V กับ GND ที่ JP")
    A("   — **ต้องไม่ต่อถึงกัน** ถ้าร้องแปลว่าลัดวงจร ห้ามจ่ายไฟเด็ดขาด")
    A("2. วัดระหว่างขา 4 กับขา 11 ของชิปแต่ละตัว — ต้องไม่ต่อถึงกันเช่นกัน")
    A("3. จ่ายไฟ 5V แล้ววัดที่ขา 14 ของ U1 — ต้องได้ราว 5V")
    A("4. ยังไม่มี 3.3V ในขั้นนี้ เพราะ 3.3V มาจากเรกูเลเตอร์บน Blue Pill")
    A("   ต้องเสียบ Blue Pill ก่อนถึงจะวัดได้")
    A("")
    A("## 6 · หลังเสียบ Blue Pill")
    A("")
    A("1. วัดที่ขา 4 ของ U2 ถึง U6 — ต้องได้ราว **3.1V** (ไม่ใช่ 3.3V "
      "เพราะตัวต้านทาน 10R ทำให้ตกไป 0.2V ซึ่งตั้งใจให้เป็นแบบนั้น)")
    A("2. วัดที่ขา 1 ของ U6 (แรงดันอ้างอิง VREF) — ต้องได้ราว **1.55V** "
      "คือครึ่งหนึ่งของ 3.1V พอดี")
    A("   ถ้าไม่ใช่ครึ่ง ให้ดู RV1 RV2 ว่าใส่ค่าถูกและบัดกรีติดจริงไหม")
    A("3. วัดที่ขา 1 ของ U2 (ขาออกช่องรับที่ 1 สเตจแรก) ตอนเงียบ ๆ "
      "— ต้องได้ใกล้ 1.55V เหมือนกัน")
    A("   ถ้าได้ใกล้ 0V หรือใกล้ 3.1V แปลว่าสเตจนั้นอิ่มตัว ให้ดูว่า 1M "
      "กับ 10nF ที่ทางเข้าใส่ถูกที่ไหม")
    A("")
    A("## 7 · สิ่งที่ยังไม่มี และต้องมีก่อนบอร์ดจะทำงาน")
    A("")
    A("**โปรแกรมสำหรับ STM32 ยังไม่ได้เขียนเลยแม้แต่บรรทัดเดียว**")
    A("")
    A("บอร์ดนี้ประกอบเสร็จแล้วจะยังทำอะไรไม่ได้ จนกว่าจะมีโปรแกรมที่")
    A("")
    A("- ตั้ง TIM4 ช่อง 1/2/3 (ขา B6 B7 B8) ให้ออกคลื่นสี่เหลี่ยม 40 kHz "
      "เป็นชุดสั้น ๆ")
    A("- ตั้ง ADC1 กับ ADC2 ให้อ่านขา A0 ถึง A7 พร้อมกันแบบต่อเนื่องผ่าน DMA")
    A("- ส่งข้อมูลออกทางพอร์ตอนุกรมด้วยรูปแบบเดียวกับที่ `car/sync4.py` "
      "อ่านอยู่ตอนนี้")
    A("")
    A("ของเดิมที่ใช้อยู่เป็น ESP32 อ่านได้ 4 ช่อง โปรแกรมนั้นย้ายมาตรง ๆ ไม่ได้ "
      "เพราะเป็นคนละตระกูลชิปกันคนละเรื่อง")
    A("")
    A("**แนะนำให้เขียนและทดสอบโปรแกรมบน Blue Pill เปล่า ๆ กับเซ็นเซอร์ตัวเดียว"
      "ก่อนสั่งทำบอร์ด** ถ้าเขียนไม่ผ่านจะได้ยังไม่เสียค่าบอร์ด")
    A("")
    A("## 8 · ต่อสายเซ็นเซอร์")
    A("")
    A("เทอร์มินอลทุกตัวมี 2 ขา · ขาบนคือสัญญาณ ขาล่างคือกราวด์")
    A("หัวอัลตราโซนิกไม่มีขั้ว สลับสายได้ไม่เป็นไร")
    A("")
    A("| เทอร์มินอล | ต่อกับ | เข้าขา STM32 |")
    A("|---|---|---|")
    for i in (1, 2, 3):
        A(f"| T{i} | หัวส่ง TX{i} | B{5 + i} (TIM4 ช่อง {i}) |")
    for i in range(1, 9):
        A(f"| K{i} | หัวรับ RX{i} | A{i - 1} |")
    A("| JP | ไฟเลี้ยง 5V | — |")
    A("")
    A("**ตำแหน่งการวางหัวรับสำคัญพอ ๆ กับวงจร** โมเดลที่เทรนไว้เรียนจาก"
      "ตำแหน่งชุดหนึ่งโดยเฉพาะ ถ้าย้ายตำแหน่งต้องเก็บข้อมูลใหม่และเทรนใหม่")

    os.makedirs(OUT, exist_ok=True)
    p = os.path.join(OUT, "build-guide.md")
    with open(p, "w", encoding="utf-8") as f:
        f.write("\n".join(L) + "\n")
    tot = sum(len(v) for v in g.values())
    print(f"คู่มือ: {len(g)} รายการ · {tot} ชิ้น -> {p}")


if __name__ == "__main__":
    main()
