pawaritmuangrach/ultrasonic01/hardware/perf_rx_layout.py

"""ผังบัดกรีภาครับลงแผ่นไข่ปลา — VREF + ช่องที่ 1 (บล็อกต้นแบบที่จะปั๊มซ้ำ)

Run:  python hardware/perf_rx_layout.py   ->  hardware/diagrams/perf_*.svg

แผ่นของผู้ใช้ (9x15 cm ยี่ห้อ 顺达):
  * **ทุกรูแยกอิสระ** วัดยืนยันแล้ว — รูข้างกันทั้งแนวตั้ง/แนวนอน และแถบยาวด้านบน
    ไม่ต่อถึงกันเลย ทุกการเชื่อมต้องทำเอง (ตะกั่วหรือสาย)
  * **คอลัมน์ A เริ่มจากขวา** ไล่ไปทางซ้าย · **เลขแถวอยู่ขอบขวา 048 บนสุด ลงไป 001**
    ผังนี้วาดให้ตรงกับของจริงทุกอย่าง มองผังกับมองแผ่นเห็นเหมือนกัน ไม่ต้องกลับด้าน

ทำไมย้ายจากบอร์ดทดลองมาไข่ปลา:
  ไล่หาสาเหตุ noise บอร์ด 2 (สูงกว่าบอร์ด 1 สามเท่า) จนตัดออกหมดทุกข้อ — สายยาว,
  ตัวส่ง, EMI เฉพาะความถี่, หัวรับ, ไฟ/VREF ร่วม, ขา ADC, ชิป, ค่า R (วัดแล้วตรงหมด)
  เหลือผู้ต้องสงสัยเดียวคือ "ตัวบอร์ดทดลองเอง" — หน้าสัมผัสสปริงที่ต้านทานไม่คงที่
  และความจุแฝงระหว่างรางที่อยู่ติดกัน ซึ่งแก้ด้วยการเปลี่ยนอะไหล่ไม่ได้

VREF สร้างบนแผ่นนี้เอง ไม่ยืมจากใคร:
  ตัวแบ่ง 10k/10k จาก 3V3 -> จุดกึ่งกลาง 1.65V -> บัฟเฟอร์ด้วยออปแอมป์ section C
  ต้องบัฟเฟอร์เพราะตัวแบ่งเปล่าๆ มีอิมพีแดนซ์ 5k ถ้าเอาไปเลี้ยงหลายช่องตรงๆ
  กระแสของช่องหนึ่งจะไปกระเพื่อม VREF ของช่องอื่น = ครอสทอล์ก (rx_frontend.md 2.4)

การแบ่งออปแอมป์ (MCP6004 มี 4 ตัวต่อชิป):
  ชิปแรก  : section A+B = ช่อง 1 (สเตจ 1, 2) · section C = บัฟเฟอร์ VREF · D ว่าง
  ชิปถัดไป: section A+B = ช่องหนึ่ง · C+D = อีกช่องหนึ่ง  (2 ช่องต่อชิป)
  ครบ 9 ช่องใช้ 5 ชิป (ช่อง1+VREF, 2+3, 4+5, 6+7, 8+9)

บัส 3 เส้น (ลวดแข็ง บัดกรีทุกรูที่ผ่าน):
  A = GND (ขวาสุดของแผ่น) · C = 3V3 · U = VREF (ซ้ายสุด)
ชิป DIP-14 วางตั้ง: ขา 1 ที่ L36 ไล่ลงถึงขา 7 ที่ L30 · ขา 8 ที่ O30 ไล่ขึ้นถึงขา 14 ที่ O36
"""
import os
import sys

sys.path.insert(0, os.path.dirname(os.path.abspath(__file__)))
from perf_panel import PerfPanel, C_SIG, C_POS, C_NEG, C_VREF, esc  # noqa: E402

HERE = os.path.dirname(os.path.abspath(__file__))
OUT = os.path.join(HERE, "diagrams")

COLS = "ABCDEFGHIJKLMNOPQRSTU"
G, P, V = "A", "C", "U"          # บัส GND, 3V3 (ฝั่งขวาแผ่น) · VREF (ฝั่งซ้ายแผ่น)
CHIP_L, CHIP_TOP = "L", 36       # ขา 1 = L36 · ขา 7 = L30 · ขา 8 = O30 · ขา 14 = O36
NX = 700                         # x ของกล่องข้อความ (อยู่นอกแผ่นเสมอ)


def rows_down(hi, lo):
    """แถวไล่จากมากไปน้อย = ตรงกับแผ่นจริงที่ 048 อยู่บนสุด"""
    return list(range(hi, lo - 1, -1))


def frame(name, title, sub, rows):
    p = PerfPanel(name, title, sub, rows, COLS, width=1340)
    hi, lo = rows[0], rows[-1]
    p.bus(G, hi, lo, C_NEG, "GND", side="right")
    p.bus(P, hi, lo, C_POS, "3V3", side="right")
    p.bus(V, hi, lo, C_VREF, "VREF")
    return p


def parts_table(p, x, y, rows_):
    """ตารางรูอยู่นอกแผ่นเสมอ — บนผังใส่แค่ชื่อสั้น (ตามที่ผู้ใช้ขอ)"""
    h = 30 + 20 * len(rows_)
    p.body.append('<rect x="%d" y="%d" width="336" height="%d" rx="8" fill="#ffffff" '
                  'stroke="#adb5bd" stroke-width="1.6"/>' % (x, y, h))
    p.body.append('<text x="%d" y="%d" font-size="13" font-weight="700" fill="#343a40">'
                  'อุปกรณ์ · เสียบรูไหน</text>' % (x + 12, y + 22))
    for i, (nm, val, a, b) in enumerate(rows_):
        yy = y + 46 + 20 * i
        p.body.append('<text x="%d" y="%d" font-size="12.5" font-weight="700" '
                      'fill="#343a40">%s</text>' % (x + 12, yy, esc(nm)))
        p.body.append('<text x="%d" y="%d" font-size="12.5" fill="#495057">%s</text>'
                      % (x + 112, yy, esc(val)))
        p.body.append('<text x="%d" y="%d" font-size="12.5" font-weight="700" '
                      'fill="#1864ab">%s → %s</text>' % (x + 222, yy, esc(a), esc(b)))


# ------------------------------------------------------------ ผัง 1 ------

def panel_power():
    rows = rows_down(41, 26)
    p = frame("perf_1_bus_chip",
              "ไข่ปลา ผัง 1 — บัสไฟ ซ็อกเก็ตชิป และคาปาบายพาส",
              "ลวดแข็ง 3 เส้น · ซ็อกเก็ต DIP-14 ขา 1 ที่ L36 · สายไฟลอดใต้ชิปแถว 28-26",
              rows)
    p.chip(CHIP_L, CHIP_TOP, "MCP6004 ตัวที่ 1")

    p.wire("L33", "L28", C_POS, lane=p.x["K"], side="h")      # ขา 4 (VDD) ลงมาแถว 28
    p.wire("L28", "C28", C_POS)
    p.tap("C28", C_POS)
    p.wire("O33", "O26", C_NEG, lane=p.x["P"], side="h")      # ขา 11 (VSS) ลงมาแถว 26
    p.wire("O26", "A26", C_NEG)
    p.tap("A26", C_NEG)
    p.part("L28", "O28", "บายพาส", "C")                        # คร่อมจุดไฟ ใต้ชิปพอดี
    p.wire("O28", "O26", C_NEG)
    p.part("A41", "C41", "10µF", "C", flip=True)

    # ไฟเข้าแผ่นใช้เทอร์มินอลขันสกรู (KF301 5.08 mm = 2 รูพอดี) เพราะไฟหลุดไม่ได้
    p.terminal(["B32", "B30"], "TB1 ไฟเข้า (KF301 2 ขา)",
               "B32=3V3 · B30=GND", side="left")
    p.wire("B32", "C32", C_POS)
    p.wire("B30", "A30", C_NEG)
    # VREF ส่งต่อแผ่นอื่น ใช้ header 1 ขาแยกต่างหาก (ไม่ใช่ไฟ จึงไม่ต้องขันสกรู)
    p.header(["B27"], "H2 VREF ออกไปแผ่นอื่น (ตัวผู้ 1 ขา)", "", side="left")
    p.wire("B27", "U27", C_VREF, lane=p.y[29], side="v")   # เลนแถว 29 ไม่ทับเส้น GND ที่แถว 26

    p.legend(NX, 118)
    parts_table(p, NX, 230, [
        ("บัส GND", "ลวดแข็ง", "A44", "A21"),
        ("บัส 3V3", "ลวดแข็ง", "C44", "C21"),
        ("บัส VREF", "ลวดแข็ง", "U44", "U21"),
        ("C ก้อนใหญ่", "10µF", "A41", "C41"),
        ("C บายพาส", "100nF", "L28", "O28"),
        ("สายไฟขา 4", "3V3", "L33", "C28"),
        ("สายไฟขา 11", "GND", "O33", "A26"),
        ("TB1 ไฟเข้า", "KF301 2 ขา", "B32", "B30"),
        ("H2 VREF ออก", "ตัวผู้ 1 ขา", "B27", "U27"),
    ])
    p.note(NX, 420, [
        "ลำดับบัดกรี (ห้ามข้าม)",
        "1. เดินลวดบัสทั้ง 3 เส้นก่อน แถว 44 ถึง 21",
        "   (ผัง 3 ใช้ถึงแถว 44 · ผัง 4 ลงถึงแถว 21)",
        "   บัดกรีทุกรูที่ผ่าน ไม่ใช่แค่หัวท้าย",
        "2. วัดว่าบัสไม่ช็อตกัน (A-C, C-U, A-U)",
        "3. ใส่ซ็อกเก็ต DIP-14 ยังไม่เสียบชิป",
        "4. ต่อสายไฟขา 4 / ขา 11 + คาปาบายพาส",
        "5. จ่ายไฟ วัดที่ซ็อกเก็ต ขา 4 = 3.30V",
        "   ขา 11 = 0V ผ่านแล้วจึงเสียบชิป",
    ], w=336)
    p.note(NX, 606, [
        "ผังนี้ตรงกับแผ่นจริงแล้ว",
        "คอลัมน์ A อยู่ขวาสุด ไล่ไปทางซ้าย",
        "เลขแถวอยู่ขอบขวา 048 บนสุด ลงไป 001",
        "มองผังกับมองแผ่นจริงเห็นเหมือนกัน",
        "ไม่ต้องกลับหัวหรือกลับซ้าย-ขวา",
    ], colour="#1971c2", bg="#e7f5ff", w=336)
    return p


# ------------------------------------------------------------ ผัง 2 ------

def panel_vref():
    rows = rows_down(41, 26)
    p = frame("perf_2_vref",
              "ไข่ปลา ผัง 2 — วงจร VREF 1.65V (สร้างบนแผ่นนี้เอง ไม่ยืมจากใคร)",
              "ตัวแบ่ง 10k/10k → กรอง → บัฟเฟอร์ section C (ขา 8,9,10) → บัส VREF",
              rows)
    p.chip(CHIP_L, CHIP_TOP, "MCP6004 ตัวที่ 1")

    p.part("C38", "F38", "Rv1", "R")                 # 3V3 -> จุดกึ่งกลาง
    p.tap("C38", C_POS)
    p.solder("F38", "F37", C_VREF)                   # โหนด 1.65V
    p.part("F37", "F34", "Rv2", "R", flip=True)      # จุดกึ่งกลาง -> GND
    p.wire("F34", "A34", C_NEG)
    p.tap("A34", C_NEG)

    p.part("I37", "I34", "Cv", "C")                  # กรองจุดอ้างอิงของทั้งบอร์ด
    p.wire("F37", "I37", C_VREF)
    p.wire("I34", "A34", C_NEG, lane=p.y[32], side="v")

    # ขา 10 (+INC): ให้สาย "ออกทางซ้าย" ของชิปเหมือนขา 8/9 จะได้ไม่โดนตัวชิปบัง
    # (เวอร์ชันเก่าดิ่งลงทะลุตัวชิปจากบน จุดต่อขา 10 เลยถูกบังจนดูเหมือนไม่มีสาย)
    p.wire("O32", "P32", C_VREF)                     # ขา 10 โผล่ออกซ้าย
    p.wire("P32", "F37", C_VREF, lane=p.y[40], side="v")   # อ้อมบนกลับไปโหนด (+INC)
    p.label("P32", "ขา 10 (อินพุต +)", dx=-6, dy=-12, colour=C_VREF, anchor="end")
    p.wire("O30", "Q30", C_VREF)                     # ขา 8 (OUTC)
    p.solder("Q30", "Q31", C_VREF)
    p.wire("Q31", "O31", C_VREF)                     # ป้อนกลับเข้าขา 9 (−INC)
    p.wire("Q30", "U30", C_VREF)                     # ออกสู่บัส VREF
    p.tap("U30", C_VREF)

    p.legend(NX, 118)
    parts_table(p, NX, 230, [
        ("Rv1", "10k", "C38", "F38"),
        ("Rv2", "10k", "F37", "F34"),
        ("Cv", "10µF มีขั้ว", "I37", "I34"),
        ("โหนด 1.65V", "เชื่อมตะกั่ว", "F38", "F37"),
        ("เข้าขา 10", "สาย", "F37", "O32"),
        ("ป้อนกลับ", "ขา 8 → ขา 9", "O30", "O31"),
        ("ออกสู่บัส", "สาย", "Q30", "U30"),
    ])
    p.note(NX, 420, [
        "ทำไมต้องมีบัฟเฟอร์",
        "ตัวแบ่ง 10k/10k มีอิมพีแดนซ์ 5k",
        "ถ้าเอาไปเลี้ยงหลายช่องตรงๆ กระแส",
        "ของช่องหนึ่งจะกระเพื่อม VREF ของ",
        "ช่องอื่น = ครอสทอล์กระหว่างช่อง",
        "บัฟเฟอร์ทำให้เหลือ <1 โอห์ม",
        "ออปแอมป์ตัวนี้คุ้มที่สุดในวงจร",
    ], colour="#ae3ec9", bg="#f8f0fc", w=336)
    p.note(NX, 588, [
        "จุดวัดก่อนไปต่อ",
        "โหนด 1.65V (F37) = 1.65V ± 0.05",
        "บัส VREF (U30) = 1.65V ± 0.05",
        "ถ้า F37 ได้ แต่ U30 ไม่ได้",
        "= บัฟเฟอร์ไม่ทำงาน อย่าไปต่อ",
        "Cv 10µF มีขั้ว ขา + ไปฝั่ง I37",
    ], colour="#1971c2", bg="#e7f5ff", w=336)
    return p


# ------------------------------------------------------------ ผัง 3 ------

def panel_input(name="perf_3_input_stage1", ch=1, no=3, chip="MCP6004 ตัวที่ 1",
                split_in=False):
    """split_in=True : แยกขา Cin ออกจากรูของเทอร์มินอล

    ช่อง 1 (บัดกรีไปแล้ว) ใช้ split_in=False เพื่อให้ผังตรงกับแผ่นจริง — ที่นั่นขา Cin
    กับขาสกรู KF301 ลงรู F44 รูเดียวกัน ซึ่งประกอบได้เพราะพันขารวมกันก่อนเสียบ
    แต่เป็นวิธีที่เปราะ: ถอดเทอร์มินอลทีต้องรื้อ Cin ด้วย และรูเดียวรับสองขาทำให้
    รอยบัดกรีนูนจนตัวเทอร์มินอลวางไม่สนิท
    ช่องใหม่ตั้งแต่ช่อง 2 เป็นต้นไปใช้ split_in=True : เทอร์มินอลอยู่ F44 ตามเดิม
    แล้วโดดสายไปเข้า Cin ที่คอลัมน์ H ซึ่งพ้นตัวเทอร์มินอล (F44 ห่าง H44 สองรู)
    """
    rows = rows_down(44, 29)
    p = frame(name,
              f"ไข่ปลา ผัง {no} — ช่อง {ch}: อินพุตและสเตจขยายที่ 1",
              "หัวรับ → Cin → โหนด IN → ขา 3 · Rf1 กลับขา 2 · Rg1-Cg1 ลง GND",
              rows)
    p.chip(CHIP_L, CHIP_TOP, chip)

    # หัวรับต่อผ่านเทอร์มินอล KF301 (ขันสกรู) — บัดกรีสาย 25AWG แข็งที่ขาหัวรับแล้วขันเข้า
    # จับแน่น ถอดเปลี่ยนหัวง่าย และสัมผัสดีกว่า pin header ที่จุดอินพุตซึ่งไวต่อ noise ที่สุด
    # KF301 ระยะขา 5.08mm = 2 รู (F44 สัญญาณ · D44 GND · เว้น E44 ตรงกลาง)
    p.terminal(["F44", "D44"], f"H1 หัวรับช่อง {ch}", "")
    p.wire("D44", "A44", C_NEG, lane=p.y[43], side="v")
    p.tap("A44", C_NEG)

    if split_in:
        # ขาสกรูกับขา Cin ต้องอยู่คนละรู — โดดสายข้าม G44 ไปเข้า Cin ที่คอลัมน์ H
        p.wire("F44", "H44", C_SIG)
        p.part("H44", "H42", "Cin", "C")
        p.solder("H42", "H41", C_SIG)                    # โหนด IN
        p.part("H41", "K41", "Rb", "R")
        p.wire("K41", "U41", C_VREF)                     # ไปบัส VREF
    else:
        # ช่อง 1 บัดกรีไปแล้วแบบนี้ (พันขา Cin กับขาสกรูเข้าด้วยกันก่อนเสียบ)
        # ผังต้องตรงกับแผ่นจริงเสมอ จึงไม่แก้ย้อนหลัง แค่ยกเว้นให้ตัวตรวจ
        p.allow_shared["F44"] = "ช่อง 1 บัดกรีแบบรูรวมไปแล้ว ผังต้องตรงกับแผ่นจริง"
        p.part("F44", "F42", "Cin", "C")
        p.solder("F42", "F41", C_SIG)                    # โหนด IN
        p.part("F41", "I41", "Rb", "R")
        p.wire("I41", "U41", C_VREF)                     # ไปบัส VREF
    p.tap("U41", C_VREF)
    # โหนด IN -> ขา 3 (+INA) ผ่านคอลัมน์ H ซึ่ง "ว่างทั้งแผ่น" ทั้ง 4 ผัง
    # ห้ามเดินลงคอลัมน์ F เด็ดขาด: F38/F37/F34 คือโหนด VREF กับขา GND ของ Rv2 (ผัง 2)
    # ซึ่งในผังนี้ไม่ได้วาดไว้ คอลัมน์ F จึงดู "ว่าง" ทั้งที่มีขาอุปกรณ์เสียบอยู่จริง
    if split_in:
        # โหนด IN อยู่คอลัมน์ H อยู่แล้ว ลงตรงไปเข้าขา 3 ได้เลย ไม่ต้องออกข้างก่อน
        p.wire("H41", "L34", C_SIG, lane=p.x["H"], side="h")
    else:
        p.wire("F42", "H42", C_SIG)                      # ออกข้างไปคอลัมน์ว่างก่อน
        p.wire("H42", "L34", C_SIG, lane=p.x["H"], side="h")  # ลงคอลัมน์ H -> เข้าขา 3
    _x3, _y3 = p.p("L34")
    p.top.append(f'<circle cx="{_x3}" cy="{_y3}" r="6" fill="{C_SIG}"/>')
    p.label("L34", "ขา 3 (อินพุต+)", dx=20, dy=-11, colour=C_SIG, anchor="start")

    p.wire("L36", "J36", C_SIG)
    p.solder("J36", "I36", C_SIG)                        # โหนดขาออกสเตจ 1
    p.part("I36", "G36", "Rf1", "R")
    p.solder("G36", "G35", C_SIG)                        # โหนด −INA
    p.wire("G35", "L35", C_SIG)                          # -> ขา 2
    p.part("G35", "G32", "Rg1", "R", flip=True)
    p.part("G32", "G30", "Cg1", "C", flip=True)
    p.wire("G30", "A30", C_NEG)
    p.tap("A30", C_NEG)

    p.legend(NX, 118)
    parts_table(p, NX, 230, ([
        ("H1 สกรูสัญญาณ", "KF301 ขาซ้าย", "F44", "→ Cin"),
        ("H1 สกรู GND", "KF301 ขาขวา", "D44", "A44"),
        ("สายโดดเข้า Cin", "สาย (ข้าม G44)", "F44", "H44"),
        ("Cin", "100nF ฟิล์ม", "H44", "H42"),
        ("Rb ไบแอส", "10k", "H41", "K41"),
    ] if split_in else [
        ("H1 สกรูสัญญาณ", "KF301 ขาซ้าย", "F44", "→ Cin"),
        ("H1 สกรู GND", "KF301 ขาขวา", "D44", "A44"),
        ("Cin", "100nF ฟิล์ม", "F44", "F42"),
        ("Rb ไบแอส", "10k", "F41", "I41"),
    ]) + [
        ("Rf1", "100k", "I36", "G36"),
        ("Rg1", "10k", "G35", "G32"),
        ("Cg1", "1nF", "G32", "G30"),
        ("โหนด IN", "เชื่อมตะกั่ว", *(("H42", "H41") if split_in else ("F42", "F41"))),
        ("โหนด −INA", "เชื่อมตะกั่ว", "G36", "G35"),
        ("โหนดออก 1", "เชื่อมตะกั่ว", "J36", "I36"),
    ])
    p.note(NX, 440, [
        "โหนด = รูติดกันที่เชื่อมด้วยตะกั่ว",
        "ไข่ปลาทุกรูแยกกัน ถ้าจุดหนึ่งต้องรับ",
        "หลายขา ให้ใช้ 2 รูติดกันแล้วป้ายตะกั่ว",
        "เชื่อม (เส้นทึบสั้นสีเขียวในผัง)",
    ], colour="#2f9e44", bg="#ebfbee", w=336)
    p.note(NX, 548, [
        "เส้นอินพุตต้องสั้นที่สุด",
        "โหนด IN ไวที่สุด เพราะถูกขยาย 121 เท่า",
        "วางหัวรับให้ใกล้ และห้ามให้สายอินพุต",
        "วิ่งขนานกับสายขาออกหรือสาย TX",
        "จุดวัดเมื่อเสร็จ: ขา 1 ต้องได้ 1.65V",
    ], colour="#e03131", bg="#fff5f5", w=336)
    return p


# ------------------------------------------------------------ ผัง 4 ------

def panel_stage2(name="perf_4_stage2_out", ch=1, no=4, chip="MCP6004 ตัวที่ 1", gpio=34):
    rows = rows_down(36, 21)
    p = frame(name,
              f"ไข่ปลา ผัง {no} — ช่อง {ch}: สเตจขยายที่ 2 และขาออกไป ESP32",
              "ขา 1 → ขา 5 ต่อตรง · Rf2 กลับขา 6 · Rg2-Cg2 ลง GND · R_out + C_out",
              rows)
    p.chip(CHIP_L, CHIP_TOP, chip)

    p.wire("L36", "L32", C_SIG, lane=p.x["K"], side="h")   # ขา 1 -> ขา 5 ต่อตรง
    p.label("L32", "ขา 5 (อินพุต+)", dx=20, dy=-11, colour=C_SIG, anchor="start")

    # ขา 7 (เอาต์สเตจ 2) ออกทางขวาที่แถวเดียวกันก่อน แล้วค่อยลง — ไม่ลอดใต้ชื่อชิป
    # (เวอร์ชันเก่าลงตรงใต้ชิปแล้วโดนป้ายชื่อ "MCP6004" ทับ จนดูเหมือนขา 7 ไม่ได้ต่ออะไร)
    p.wire("L30", "J29", C_SIG, lane=p.y[30], side="v")
    p.label("L30", "ขา 7 (เอาต์)", dx=20, dy=-11, colour=C_SIG, anchor="start")
    p.solder("J29", "I29", C_SIG)                          # โหนดขาออกสเตจ 2
    p.part("I29", "G29", "Rf2", "R")
    p.solder("G29", "G28", C_SIG)                          # โหนด −INB
    # ป้อนกลับเข้าขา 6 ต้องใช้คอลัมน์ H ไม่ใช่ K — คอลัมน์ K มีสาย ขา1->ขา5 อยู่แล้ว
    # ถ้าใช้ K ทั้งคู่ สองเส้นจะห่างกันแค่แถวเดียว มองเป็นเส้นเดียว = ต่อ ขา1/5/6 ถึงกันหมด
    p.wire("G28", "L31", C_SIG, lane=p.x["H"], side="h")
    p.label("L31", "ขา 6 (ป้อนกลับ)", dx=20, dy=13, colour=C_SIG, anchor="start")
    p.part("G28", "G25", "Rg2", "R", flip=True)
    p.part("G25", "G23", "Cg2", "C", flip=True)
    p.wire("G23", "A23", C_NEG)
    p.tap("A23", C_NEG)

    p.part("J29", "M29", "R_out", "R", flip=True)
    p.solder("M29", "M28", C_SIG)
    p.part("M28", "M26", "C_out", "C")
    p.wire("M26", "A21", C_NEG, lane=p.y[21], side="v")
    p.tap("A21", C_NEG)
    # ออกไป ESP32 ผ่าน header 2 ขา — มี GND คู่มาด้วยเสมอ เพื่อให้สายมีทางกลับที่สั้น
    p.header(["P26", "Q26"], f"H3 ออกไป ESP32 (ตัวผู้ 2 ขา)",
             f"P26=สัญญาณ GPIO{gpio} · Q26=GND")
    p.wire("M29", "P26", "#f08c00", lane=p.y[27], side="v")
    p.wire("Q26", "A24", C_NEG, lane=p.y[24], side="v")
    p.tap("A24", C_NEG)

    p.legend(NX, 118)
    parts_table(p, NX, 230, [
        ("Rf2", "100k", "I29", "G29"),
        ("Rg2", "10k", "G28", "G25"),
        ("Cg2", "1nF", "G25", "G23"),
        ("R_out", "2.2k", "J29", "M29"),
        ("C_out", "1nF", "M28", "M26"),
        ("โหนด −INB", "เชื่อมตะกั่ว", "G29", "G28"),
        ("โหนดออก 2", "เชื่อมตะกั่ว", "J29", "I29"),
        ("H3 ไป ESP32", "ตัวผู้ 2 ขา", "P26", "Q26"),
    ])
    p.note(NX, 440, [
        "จุดวัดหลังบัดกรีเสร็จ (ยังไม่ใส่หัวรับ)",
        "ขา 1 = 1.65V ± 0.05 · ขา 7 = 1.65V ± 0.1",
        "ปลาย R_out (M29) = 1.65V ± 0.1",
        "ได้ 0V หรือ 3.3V = สเตจนั้นอิ่มตัว",
        "ให้ย้อนดู Rg/Cg ของสเตจนั้นก่อน",
    ], colour="#1971c2", bg="#e7f5ff", w=336)
    p.note(NX, 566, [
        "ทิศทางสัญญาณ ห้ามสลับ",
        "อินพุตอยู่แถวบน (44-35)",
        "ขาออกอยู่แถวล่าง (29-21)",
        "ถ้าเอาขาออกไปไว้ใกล้อินพุต ความจุแฝง",
        "ไม่กี่ pF ที่เกน 121 เท่า จะกลายเป็น",
        "ป้อนกลับบวก = วงจรหอนเอง",
    ], colour="#e03131", bg="#fff5f5", w=336)
    return p


# ------------------------------------------------------------ ผัง 5 ------

def panel_board2():
    """แผ่นที่ 2 — เหมือนผัง 1 ทุกอย่าง ยกเว้น **ไม่สร้าง VREF เอง** แต่รับเข้ามา

    VREF ที่ส่งข้ามแผ่นได้โดยไม่เกิดครอสทอล์ก เพราะผ่านบัฟเฟอร์มาแล้ว (อิมพีแดนซ์ <1 โอห์ม)
    ต่างจากตอนบอร์ดทดลองที่ยืมตัวแบ่งเปล่า ๆ ข้ามบอร์ด ซึ่งอิมพีแดนซ์ 5k
    """
    rows = rows_down(41, 22)
    p = frame("perf_5_board2_power",
              "ไข่ปลา ผัง 5 — แผ่นที่ 2: บัสไฟ ซ็อกเก็ตชิป 2 และรับ VREF จากแผ่น 1",
              "ชิป 2 = ช่อง 2 (section A+B) + ช่อง 3 (section C+D) · VREF รับเข้าไม่ต้องสร้างใหม่",
              rows)
    p.chip(CHIP_L, CHIP_TOP, "MCP6004 ตัวที่ 2")

    p.wire("L33", "L28", C_POS, lane=p.x["K"], side="h")      # ขา 4 (VDD)
    p.wire("L28", "C28", C_POS)
    p.tap("C28", C_POS)
    p.wire("O33", "O26", C_NEG, lane=p.x["P"], side="h")      # ขา 11 (VSS)
    p.wire("O26", "A26", C_NEG)
    p.tap("A26", C_NEG)
    p.part("L28", "O28", "บายพาส", "C")
    p.wire("O28", "O26", C_NEG)
    p.part("A41", "C41", "10µF", "C", flip=True)

    p.terminal(["B32", "B30"], "TB2 ไฟเข้า (KF301 2 ขา)",
               "B32=3V3 · B30=GND", side="left")
    p.wire("B32", "C32", C_POS)
    p.wire("B30", "A30", C_NEG)

    # VREF เข้าเป็น "คู่สาย VREF+GND" เสมอ — บทเรียนใหญ่สุดของ Stage B คือสายสัญญาณ
    # ต้องมีสายกราวด์เดินเคียง (ลด noise ได้ 3.3 เท่าจากสายเส้นเดียว)
    p.header(["B24", "B23"], "H4 รับ VREF จากแผ่น 1 (ตัวผู้ 2 ขา)",
             "B24=VREF · B23=GND · บิดเกลียวคู่กันมา", side="left")
    p.wire("B24", "U24", C_VREF, lane=p.y[22], side="v")
    p.tap("U24", C_VREF)
    p.wire("B23", "A23", C_NEG)
    p.tap("A23", C_NEG)

    p.legend(NX, 118)
    parts_table(p, NX, 230, [
        ("บัส GND", "ลวดแข็ง", "A44", "A21"),
        ("บัส 3V3", "ลวดแข็ง", "C44", "C21"),
        ("บัส VREF", "ลวดแข็ง", "U44", "U21"),
        ("C ก้อนใหญ่", "10µF", "A41", "C41"),
        ("C บายพาส", "100nF", "L28", "O28"),
        ("สายไฟขา 4", "3V3", "L33", "C28"),
        ("สายไฟขา 11", "GND", "O33", "A26"),
        ("TB2 ไฟเข้า", "KF301 2 ขา", "B32", "B30"),
        ("H4 VREF เข้า", "ตัวผู้ 2 ขา", "B24", "B23"),
    ])
    p.note(NX, 440, [
        "ลำดับบัดกรี (เหมือนผัง 1)",
        "1. เดินบัส 3 เส้น แถว 44 ถึง 21",
        "2. วัดว่าบัสไม่ช็อตกัน (A-C, C-U, A-U)",
        "3. ใส่ซ็อกเก็ต ยังไม่เสียบชิป",
        "4. ต่อไฟขา 4 / ขา 11 + คาปาบายพาส",
        "5. จ่ายไฟ วัด ขา 4 = 3.30V · ขา 11 = 0V",
        "6. ต่อ H4 จากแผ่น 1 วัดบัส VREF = 1.65V",
        "   ผ่านครบแล้วจึงเสียบชิป",
    ], w=336)
    p.note(NX, 626, [
        "จุดที่ต่างจากแผ่น 1",
        "แผ่นนี้ไม่มี Rv1 Rv2 Cv และไม่มีบัฟเฟอร์",
        "VREF รับมาจาก H2 ของแผ่น 1 ผ่าน H4",
        "section C+D ของชิปนี้ว่างไว้ให้ช่อง 3",
        "สาย VREF ต้องมี GND เดินคู่มาด้วยเสมอ",
    ], colour="#ae3ec9", bg="#f8f0fc", w=336)
    return p


# ------------------------------------------------- ผังภาพรวมแผ่นที่ 2 ------

COLS2 = "ABCDEFGHIJKLMNOPQRSTUVWXYZ"      # แผ่นจริงมี 30 คอลัมน์ ใช้ 26 พอ
G2, P2, V2, GZ = "A", "C", "Y", "Z"       # GND · 3V3 · VREF · GND เส้นที่ 2 (ขอบซ้าย)


def panel_board2_map():
    """ภาพรวมแผ่นที่ 2 — จองพื้นที่ให้ครบ 2 ช่องก่อนลงมือบัดกรี

    ชิป DIP วางตั้ง ขาซ้าย (คอลัมน์ L) = section A+B = ช่อง 2
                    ขาขวา (คอลัมน์ O) = section C+D = ช่อง 3
    อุปกรณ์ของแต่ละช่องจึงอยู่คนละฝั่งของชิป เป็นภาพสะท้อนกัน ใช้คนละครึ่งแผ่น
    """
    rows = rows_down(46, 20)
    p = PerfPanel("perf_5a_board2_map",
                  "ไข่ปลา แผ่นที่ 2 — ภาพรวม: ชิปเดียว 2 ช่อง (ช่อง 2 + ช่อง 3)",
                  "จองพื้นที่ให้ครบก่อนบัดกรี · ช่อง 2 อยู่ฝั่งขวาของชิป · ช่อง 3 ฝั่งซ้าย (ภาพสะท้อน)",
                  rows, COLS2, width=1560)
    hi, lo = rows[0], rows[-1]
    p.bus(G2, hi, lo, C_NEG, "GND", side="right")
    p.bus(P2, hi, lo, C_POS, "3V3", side="right")
    p.bus(V2, hi, lo, C_VREF, "VREF", side="right")
    p.bus(GZ, hi, lo, C_NEG, "GND 2")

    def region(c_hi, c_lo, r_hi, r_lo, colour, label):
        x0 = min(p.x[c_hi], p.x[c_lo]) - 13
        x1 = max(p.x[c_hi], p.x[c_lo]) + 13
        y0, y1 = p.y[r_hi] - 13, p.y[r_lo] + 13
        p.under.append(f'<rect x="{x0}" y="{y0}" width="{x1-x0}" height="{y1-y0}" rx="8" '
                       f'fill="{colour}" fill-opacity="0.18" stroke="{colour}" '
                       f'stroke-width="2" stroke-dasharray="6 4"/>')
        p.body.append(f'<text x="{(x0+x1)/2:.0f}" y="{y1+22}" font-size="14" '
                      f'font-weight="700" text-anchor="middle" fill="{colour}">{esc(label)}</text>')

    region("D", "K", 44, 21, "#2f9e44", "ช่อง 2  (section A+B)")
    region("P", "W", 44, 21, "#1971c2", "ช่อง 3  (section C+D)")
    p.chip(CHIP_L, CHIP_TOP, "MCP6004/6024 ตัวที่ 2")

    p.terminal(["B32", "B30"], "TB2 ไฟเข้า", "3V3 · GND", side="left")
    p.header(["B24", "B23"], "H4 รับ VREF+GND จากแผ่น 1", "", side="left")
    p.terminal(["F44", "D44"], "H1 หัวรับช่อง 2", "", side="left")
    p.terminal(["R44", "T44"], "H1b หัวรับช่อง 3", "", side="right")
    p.header(["E26", "E25"], "H3 ออกช่อง 2", "", side="left")
    p.header(["S26", "S25"], "H3b ออกช่อง 3", "", side="right")

    p.legend(NX + 160, 118)
    p.note(NX + 160, 250, [
        "ทำไมสองช่องอยู่คนละฝั่งได้",
        "ชิป DIP-14 มีขาสองแถว ซ้าย-ขวา",
        "ขาซ้าย (1-7) = section A+B = ช่อง 2",
        "ขาขวา (8-14) = section C+D = ช่อง 3",
        "อุปกรณ์จึงกางออกคนละทาง ไม่ชนกัน",
        "ผังช่อง 3 = ภาพสะท้อนของช่อง 2 ทุกจุด",
    ], colour="#1971c2", bg="#e7f5ff", w=380)
    p.note(NX + 160, 400, [
        "คู่ขาที่ตรงกัน (ช่อง 2 → ช่อง 3)",
        "ขา 3 → ขา 12   (อินพุต + สเตจ 1)",
        "ขา 2 → ขา 13   (ป้อนกลับสเตจ 1)",
        "ขา 1 → ขา 14   (เอาต์สเตจ 1)",
        "ขา 5 → ขา 10   (อินพุต + สเตจ 2)",
        "ขา 6 → ขา 9    (ป้อนกลับสเตจ 2)",
        "ขา 7 → ขา 8    (เอาต์สเตจ 2)",
        "แถวเดียวกันหมด ต่างแค่คอลัมน์",
    ], colour="#2f9e44", bg="#ebfbee", w=380)
    p.note(NX + 160, 578, [
        "บัสของแผ่นนี้มี 4 เส้น",
        "GND (A) กับ GND 2 (Z) = ขอบสองข้าง",
        "ต่อถึงกันด้วยสายที่หัวและท้ายแผ่น",
        "เพื่อให้ทั้งสองช่องมีกราวด์อยู่ใกล้ตัว",
        "ไม่ต้องลากสายกราวด์ยาวข้ามแผ่น",
        "(บทเรียน: กราวด์ใกล้ = noise ลด 3.3 เท่า)",
        "3V3 (C) สั้นได้ เพราะมีแค่ขา 4 ที่ใช้",
        "VREF (Y) อยู่นอกพื้นที่ทั้งสองช่อง",
    ], colour="#ae3ec9", bg="#f8f0fc", w=380)
    return p


def main():
    # สร้างทั้ง 4 ผังก่อน เพื่อรู้ว่า "รูไหนถูกผังอื่นจองไว้แล้ว" แล้วค่อยวาดวงจางทับ
    panels = [panel_power(), panel_vref(), panel_input(), panel_stage2(),
              panel_board2(), panel_board2_map(),
              panel_input("perf_6_ch2_input", ch=2, no=6, chip="MCP6004 ตัวที่ 2",
                          split_in=True),
              panel_stage2("perf_7_ch2_stage2", ch=2, no=7, chip="MCP6004 ตัวที่ 2",
                           gpio=35)]
    # แผ่น 1 = ผัง 1-4 · แผ่น 2 = ผัง 5 เป็นต้นไป — วงประต้องคิดแยกแผ่น
    board = {p.name: (1 if p.name[5] in "1234" else 2) for p in panels}
    allused = {}
    for p in panels:
        allused[p.name] = set(p.used)
    for p in panels:
        other = set().union(*(v for k, v in allused.items()
                              if k != p.name and board[k] == board[p.name]))
        p.ghosts(other - p.used)
        # กล่องอธิบายวงประต้องอยู่พ้นเลขแถวเสมอ (ผังกว้างไม่เท่ากัน) และผังภาพรวม
        # มีกล่องอธิบายของตัวเองอยู่แล้ว จึงข้าม
        if "map" in p.name:
            print("เขียน", p.save(OUT))
            continue
        nx = max(NX, 58 + (len(p.cols) - 1) * 26 + 94)
        p.note(nx, 700, [
            "วงประแดง = รูที่ผังอื่นใช้อยู่",
            "แผ่นนี้เป็นแผ่นเดียวกันทั้ง 4 ผัง",
            "ห้ามบัดกรีหรือเดินสายทับรูที่มีวงประแดง",
            "และห้ามเดินสายเลียบไปตามคอลัมน์ที่มีวงประ",
        ], colour="#c92a2a", bg="#fff5f5", w=336)
        print("เขียน", p.save(OUT))


if __name__ == "__main__":
    main()
