pawaritmuangrach/ultrasonic01/hardware/perf_tx_layout.py

"""ผังบัดกรี **ภาคส่ง (TX)** ลงแผ่นไข่ปลา — 3 หัวส่งจาก 74HCT04 ตัวเดียว

Run:  python hardware/perf_tx_layout.py   ->  hardware/diagrams/perf_tx_*.svg

แผ่นเดียวกับภาครับ (9x15 cm ยี่ห้อ 顺达) ทุกรูแยกอิสระ ต้องเชื่อมเอง
คอลัมน์ A เริ่มจาก **ขวา** ไล่ไปซ้าย · เลขแถวอยู่ขอบขวา 048 บนสุด ลงไป 001
มองผังกับมองแผ่นจริงเห็นเหมือนกัน ไม่ต้องกลับด้าน

ทำไมทำ 3 TX เลย ไม่ทำ 1 TX ก่อน:
  ข้อมูลชุด walk 5 ช่วง (25 ส.ค. 2026) ชี้ว่าปัญหาใหญ่สุดของภาคส่งตัวเดียวคือ
  **เอคโค่จากคนสะท้อนแบบ specular** — ขยับตัวนิดเดียวความแรงวูบ 40 เท่า
  (วัดได้ 28 mV ถึง 1173 mV ที่ระยะเดียวกัน) ทำให้ 21% ของเฟรมใช้ไม่ได้
  หัวส่งคนละตำแหน่งส่องวัตถุคนละมุม โอกาสที่ทุกตัวหลุดพร้อมกันต่ำกว่ามาก
  และ **TX ถูก RX แพง** — TX เพิ่มตัวใช้แค่ GPIO 1 ขา ไม่กิน ADC ซึ่งเป็นคอขวดจริง

ทำไม 2 เกตต่อหัวส่ง (ไม่ใช่ 1 เกตขับ + 3 เกตขนานแบบเวอร์ชัน A บนบอร์ดทดลอง):
  74HCT04 มี 6 เกต -> 3 หัวส่ง x 2 เกต = ใช้ครบพอดี เหลือชิปสำรองอีก 2 ตัว
  **ที่ 40 kHz การขนานเกตแทบไม่ช่วยเรื่องความแรง** เพราะทรานสดิวเซอร์คือ C 2.4 nF
  ซึ่งมีรีแอกแตนซ์ 1658 โอห์ม ที่ 40 kHz — เทียบกับอิมพีแดนซ์ขาออก 115 โอห์ม (3 เกต)
  หรือ 145 โอห์ม (1 เกต) แล้วต่างกันไม่ถึง 0.3% ของแรงดันที่ตกคร่อมหัวส่ง
  การขนานเกตมีผลกับ "ความชันของขอบ" ซึ่งเราตั้งใจทำให้ช้าลงด้วย R 100 โอห์มอยู่แล้ว
  กระแสพีคต่อเกต = 5V / 145 โอห์ม = 34 mA (พิกัด 25 mA ต่อขา ยิงทีละตัวจึงไม่เกินแพ็กเกจ)

**ต้องเป็น 74HCT04 ไม่ใช่ 74HC04** — HC ต้องการ VIH 3.5V แต่ ESP32 ให้แค่ 3.3V
อาการถ้าใส่ผิดคือ "บางทีก็ยิง บางทีก็ไม่ยิง" ซึ่งไล่บั๊กยากมาก (tx_driver.md §0)

**ห้ามต่อขาออกของชิป (5V) กลับเข้า GPIO ของ ESP32** — พังถาวร ทิศทางมีทางเดียว
ESP32 (3.3V) -> อินพุตชิป เท่านั้น

ทำไมต้องผ่านเกต 2 ชั้น: เพื่อให้ขาออก "ตามขาเข้า" ตอนพัก GPIO เป็น LOW ขาออกก็ LOW
= แรงดันคร่อมหัวส่ง 0V ถ้าใช้เกตชั้นเดียว ตอนพักจะมี 5V คร่อมหัวส่งตลอดเวลา

การแบ่งเกต (74HCT04: เกต n มีขาเข้า/ขาออกติดกัน จึงจับคู่เกตที่อยู่คอลัมน์เดียวกันได้):
  TX1 = เกต 1,2  (ขา 1->2, 3->4)   ทั้งคู่อยู่คอลัมน์ L  ขาออก = ขา 4
  TX2 = เกต 6,5  (ขา 13->12, 11->10) ทั้งคู่อยู่คอลัมน์ O  ขาออก = ขา 10
  TX3 = เกต 3,4  (ขา 5->6, 9->8)   คร่อมสองฝั่ง จึงมีสายข้ามใต้ชิปหนึ่งเส้น ขาออก = ขา 8

บัส 3 เส้น (ลวดแข็ง บัดกรีทุกรูที่ผ่าน):
  A = GND (ขวาสุด) · C = +5V · U = GND ฝั่งซ้าย (เชื่อมกับ A ที่แถว 21)
  GND ฝั่งซ้ายมีไว้ให้ขาที่ 2 ของหัวส่งทั้งสามกลับกราวด์ได้สั้น ๆ
  ไม่ต้องลากข้ามแผ่นไปคอลัมน์ A ซึ่งจะเป็นวงกราวด์ยาวที่กระแส 34 mA วิ่งผ่าน
ชิป DIP-14 วางตั้ง: ขา 1 ที่ L36 ไล่ลงถึงขา 7 ที่ L30 · ขา 8 ที่ O30 ไล่ขึ้นถึงขา 14 ที่ O36
"""
import os
import sys

sys.path.insert(0, os.path.dirname(os.path.abspath(__file__)))
from perf_panel import PerfPanel, C_SIG, C_POS, C_NEG, esc  # noqa: E402

HERE = os.path.dirname(os.path.abspath(__file__))
OUT = os.path.join(HERE, "diagrams")

COLS = "ABCDEFGHIJKLMNOPQRSTU"
G, P5, G2 = "A", "C", "U"        # บัส GND ขวา · +5V · GND ซ้าย
CHIP_L, CHIP_TOP = "L", 36       # ขา 1 = L36 · ขา 7 = L30 · ขา 8 = O30 · ขา 14 = O36
CHIP = "74HCT04"
NX = 700
ROWS = list(range(44, 19, -1))   # 044 บนสุด ลงไป 020 — ทุกผังใช้ช่วงเดียวกัน


def frame(name, title, sub):
    p = PerfPanel(name, title, sub, ROWS, COLS, width=1340)
    p.bus(G, 44, 20, C_NEG, "GND", side="right")
    p.bus(P5, 44, 20, C_POS, "+5V", side="right")
    p.bus(G2, 44, 20, C_NEG, "GND ซ้าย", side="right")
    return p


def parts_table(p, x, y, rows_):
    h = 30 + 20 * len(rows_)
    p.body.append('<rect x="%d" y="%d" width="336" height="%d" rx="8" fill="#ffffff" '
                  'stroke="#adb5bd" stroke-width="1.6"/>' % (x, y, h))
    p.body.append('<text x="%d" y="%d" font-size="13" font-weight="700" fill="#343a40">'
                  'อุปกรณ์ · เสียบรูไหน</text>' % (x + 12, y + 22))
    for i, (nm, val, a, b) in enumerate(rows_):
        yy = y + 46 + 20 * i
        p.body.append('<text x="%d" y="%d" font-size="12.5" font-weight="700" '
                      'fill="#343a40">%s</text>' % (x + 12, yy, esc(nm)))
        p.body.append('<text x="%d" y="%d" font-size="12.5" fill="#495057">%s</text>'
                      % (x + 118, yy, esc(val)))
        p.body.append('<text x="%d" y="%d" font-size="12.5" font-weight="700" '
                      'fill="#1864ab">%s → %s</text>' % (x + 224, yy, esc(a), esc(b)))


# ------------------------------------------------------------ ผัง 1 ------

def panel_power():
    p = frame("perf_tx_1_power_chip",
              "ไข่ปลา TX ผัง 1 — บัสไฟ 5V ซ็อกเก็ตชิป และคาปาบายพาส",
              "ลวดแข็ง 3 เส้น · ซ็อกเก็ต DIP-14 ขา 1 ที่ L36 · "
              "ขา 14 กับ ขา 7 เป็นขามุม จึงเดินสายออกตรงๆ ได้")
    p.chip(CHIP_L, CHIP_TOP, CHIP)

    # ขา 14 (VCC) เป็นขามุมบนของคอลัมน์ซ้าย เดินขึ้นตรงๆ ได้ ไม่ทับตัวชิป
    p.wire("O36", "O38", C_POS)
    p.wire("O38", "O40", C_POS)
    p.wire("O40", "C40", C_POS)
    p.tap("C40", C_POS)
    p.label("O40", "ขา 14 VCC", dx=0, dy=-13, colour=C_POS)

    # คาปาบายพาสคร่อมไฟ ให้ใกล้ขา 14 ที่สุดเท่าที่วางได้ (2 แถว = 5 mm)
    p.part("O38", "L38", "บายพาส 100nF", "C")
    p.wire("L38", "A38", C_NEG)
    p.tap("A38", C_NEG)

    # ขา 7 (GND) เป็นขามุมล่างของคอลัมน์ขวา เดินลงตรงๆ ได้
    p.wire("L30", "L28", C_NEG)
    p.wire("L28", "A28", C_NEG)
    p.tap("A28", C_NEG)
    p.label("L28", "ขา 7 GND", dx=0, dy=19, colour=C_NEG)

    p.part("A44", "C44", "10µF", "C", flip=True)

    p.terminal(["B34", "B32"], "TB1 ไฟเข้า 5V", "", side="left")
    p.wire("B34", "C34", C_POS)
    p.wire("B32", "A32", C_NEG)

    # เชื่อมบัส GND สองเส้นเข้าหากันจุดเดียว ที่แถวล่างสุดให้พ้นทางเดินสายอื่น
    p.wire("U20", "A20", C_NEG)
    p.tap("U20", C_NEG)
    p.tap("A20", C_NEG)

    p.legend(NX, 118)
    parts_table(p, NX, 230, [
        ("บัส GND ขวา", "ลวดแข็ง", "A44", "A20"),
        ("บัส +5V", "ลวดแข็ง", "C44", "C20"),
        ("บัส GND ซ้าย", "ลวดแข็ง", "U44", "U20"),
        ("เชื่อม GND", "ลวด 1 เส้น", "U20", "A20"),
        ("C ก้อนใหญ่", "10µF มีขั้ว", "A44", "C44"),
        ("C บายพาส", "100nF", "O38", "L38"),
        ("ขา 14 → +5V", "สาย", "O36", "C40"),
        ("ขา 7 → GND", "สาย", "L30", "A28"),
        ("TB1 ขั้ว +5V", "KF301 ขาบน", "B34", "C34"),
        ("TB1 ขั้ว GND", "KF301 ขาล่าง", "B32", "A32"),
    ])
    p.note(NX, 448, [
        "ลำดับบัดกรี (ห้ามข้าม)",
        "1. เดินลวดบัสทั้ง 3 เส้น แถว 44 ถึง 20",
        "   บัดกรีทุกรูที่ผ่าน ไม่ใช่แค่หัวท้าย",
        "2. เชื่อม U20-A20 แล้ววัดว่า A กับ U ต่อกัน",
        "   และ C ไม่ช็อตกับทั้งสอง",
        "3. ใส่ซ็อกเก็ต DIP-14 ยังไม่เสียบชิป",
        "4. ต่อสายขา 14 / ขา 7 + คาปาบายพาส",
        "5. จ่ายไฟ 5V วัดที่ซ็อกเก็ต",
        "   ขา 14 = 5.0V · ขา 7 = 0V",
        "   ผ่านแล้วจึงเสียบชิป",
    ], w=336)
    p.note(NX, 660, [
        "ไฟเลี้ยงเป็น 5V ไม่ใช่ 3V3",
        "ต่างจากแผ่นภาครับที่ใช้ 3V3",
        "ถ้าจ่าย 3V3 เข้าแผ่นนี้ เสียงจะเบาลง",
        "แต่ไม่พัง · ถ้าจ่าย 5V เข้าแผ่นรับ",
        "ออปแอมป์ MCP6004 พังทันที",
        "ติดป้ายที่ TB1 ให้ชัดว่า 5V",
    ], colour="#c92a2a", bg="#fff5f5", w=336)
    return p


# ------------------------------------------------------------ ผัง 2 ------

def panel_gates():
    p = frame("perf_tx_2_gates",
              "ไข่ปลา TX ผัง 2 — สาย GPIO เข้าชิป และการต่อเกตสองชั้นของทั้ง 3 หัวส่ง",
              "ขากลางของชิปต้องเดินสายออกทางข้าง (คอลัมน์ K หรือ P) เสมอ "
              "ห้ามเดินขึ้น/ลงทับตัวชิป")
    p.chip(CHIP_L, CHIP_TOP, CHIP)

    # หัวต่อวางแนวนอนที่ขอบล่าง — ป้ายจะอยู่เหนือหัวต่อในที่ว่าง ไม่ทับสายหรือเลขแถว
    p.header(["G24", "F24", "E24", "D24"], "H1 จาก ESP32", "", side="right")
    p.wire("D24", "A24", C_NEG)
    p.tap("A24", C_NEG)

    # ---- TX1 = เกต 1,2 อยู่คอลัมน์ L ทั้งคู่ ----
    # เดินขึ้นคอลัมน์ E (นอกสุด) แล้วเลี้ยวเข้าขา 1 ที่แถว 36 ซึ่งสูงกว่าปลายสายอื่น
    # จึงไม่ตัดกับเส้นไหนเลย — สายที่เลี้ยวแถวต่ำต้องอยู่คอลัมน์ในกว่าเสมอ
    p.wire("E24", "E36", C_SIG)
    p.wire("E36", "L36", C_SIG)                       # เข้าขา 1 ทางขวาของชิป
    p.wire("L35", "J35", C_SIG)                       # ขา 2 ออกทางขวา
    p.wire("J35", "J34", C_SIG)
    p.wire("J34", "L34", C_SIG)                       # กลับเข้าขา 3
    p.label("J35", "TX1 ขา 2→3", dx=26, dy=-14, colour=C_SIG)

    # ---- TX3 = เกต 3,4 คร่อมสองฝั่ง มีสายอ้อมใต้ชิปหนึ่งเส้น ----
    p.wire("G24", "G32", C_SIG)
    p.wire("G32", "L32", C_SIG)                       # เข้าขา 5
    p.wire("L31", "J31", C_SIG)                       # ขา 6 ออกทางขวา
    p.wire("J31", "J29", C_SIG)
    p.wire("J29", "R29", C_SIG)                       # อ้อมใต้ชิปที่แถว 29
    p.wire("R29", "R31", C_SIG)
    p.wire("R31", "O31", C_SIG)                       # เข้าขา 9 ทางซ้ายของชิป
    p.label("R29", "TX3 ขา 6→9 อ้อมใต้ชิป", dx=44, dy=19, colour=C_SIG)

    # ---- TX2 = เกต 6,5 อยู่คอลัมน์ O ทั้งคู่ ----
    p.wire("F24", "F22", C_SIG)
    p.wire("F22", "S22", C_SIG)                       # อ้อมใต้สุด แถว 22
    p.wire("S22", "S35", C_SIG)
    p.wire("S35", "O35", C_SIG)                       # เข้าขา 13 ทางซ้ายของชิป
    p.wire("O34", "P34", C_SIG)                       # ขา 12 ออกทางซ้าย
    p.wire("P34", "P33", C_SIG)
    p.wire("P33", "O33", C_SIG)                       # กลับเข้าขา 11
    p.label("Q34", "TX2 ขา 12→11", dx=10, dy=-14, colour=C_SIG)
    p.label("Q22", "TX2 อ้อมใต้สุด", dx=0, dy=19, colour=C_SIG)

    p.legend(NX, 118)
    parts_table(p, NX, 230, [
        ("H1 จาก ESP32", "ตัวผู้ 4 ขา", "G24", "D24"),
        ("  ขาซ้ายสุด G24", "= TX3 เข้า", "G24", "L32"),
        ("  ขา F24", "= TX2 เข้า", "F24", "O35"),
        ("  ขา E24", "= TX1 เข้า", "E24", "L36"),
        ("  ขาขวาสุด D24", "= GND", "D24", "A24"),
        ("TX1 ขา 2→3", "สาย 3 ท่อน", "L35", "L34"),
        ("TX2 ขา 12→11", "สาย 3 ท่อน", "O34", "O33"),
        ("TX3 ขา 6→9", "สาย 5 ท่อน", "L31", "O31"),
    ])
    p.note(NX, 428, [
        "ขาชิปที่ใช้ ทั้ง 14 ขา",
        "1 = TX1 เข้า      14 = +5V",
        "2 → 3 (ต่อกัน)    13 = TX2 เข้า",
        "4 = TX1 ออก      12 → 11 (ต่อกัน)",
        "5 = TX3 เข้า      10 = TX2 ออก",
        "6 → 9 (ต่อกัน)     9 = ต่อจากขา 6",
        "7 = GND           8 = TX3 ออก",
    ], colour="#1971c2", bg="#e7f5ff", w=336)
    p.note(NX, 592, [
        "ทำไมสายต้องออกทางข้างของชิป",
        "ส.ค. 2026 ผัง VREF ของภาครับเดินสาย",
        "ดิ่งลงหาขา 10 ทะลุตัวชิป จุดต่อเลยถูก",
        "ตัวชิปบัง ผู้ต่อมองไม่เห็นจึงบัดกรีไป",
        "ลงขา 14 แทน = อินพุตลอย เอาต์พุตชน",
        "ขอบล่าง ไล่บั๊กเสียเวลาหลายรอบ",
        "ผังนี้ทุกสายจึงโผล่ออกข้างให้เห็นชัด",
    ], colour="#f08c00", bg="#fff4e6", w=336)
    return p


# ------------------------------------------------------------ ผัง 3 ------

def panel_outputs():
    p = frame("perf_tx_3_outputs",
              "ไข่ปลา TX ผัง 3 — ตัวต้านทานอนุกรม 100Ω และเทอร์มินอลหัวส่งทั้ง 3 ตัว",
              "R อนุกรมลดกระแสพีคจาก 333 mA เหลือ 34 mA และลดกราวด์เด้ง 58 เท่า "
              "โดยไม่ทำให้เสียงเบาลง")
    p.chip(CHIP_L, CHIP_TOP, CHIP)

    # ---- TX1: ขา 4 (L33) เป็นขากลางฝั่งขวา ออกทางขวาแล้วอ้อมขึ้นข้ามหัวชิป ----
    p.wire("L33", "K33", C_SIG)
    p.wire("K33", "K43", C_SIG)
    p.wire("K43", "Q43", C_SIG)                       # อ้อมเหนือชิปที่แถว 43
    p.part("Q43", "S43", "R1 100Ω", "R")
    p.solder("S43", "T43", C_SIG)                     # หยดตะกั่วเข้าขาเทอร์มินอล
    p.terminal(["T43", "T41"], "TB2  TX1", "")
    p.wire("T41", "U41", C_NEG)

    # ---- TX2: ขา 10 (O32) ออกทางซ้าย ----
    p.wire("O32", "Q32", C_SIG)
    p.part("Q32", "S32", "R2 100Ω", "R")
    p.solder("S32", "T32", C_SIG)
    p.terminal(["T32", "T30"], "TB3  TX2", "")
    p.wire("T30", "U30", C_NEG)

    # ---- TX3: ขา 8 (O30) เป็นขามุม ออกทางซ้ายได้ตรงๆ ----
    p.wire("O30", "Q30", C_SIG)
    p.wire("Q30", "Q26", C_SIG)
    p.part("Q26", "S26", "R3 100Ω", "R")
    p.solder("S26", "T26", C_SIG)
    p.terminal(["T26", "T24"], "TB4  TX3", "")
    p.wire("T24", "U24", C_NEG)

    p.legend(NX, 118)
    parts_table(p, NX, 230, [
        ("R1 (TX1)", "100Ω", "Q43", "S43"),
        ("R2 (TX2)", "100Ω", "Q32", "S32"),
        ("R3 (TX3)", "100Ω", "Q26", "S26"),
        ("ตะกั่วเชื่อม R เข้าขั้ว", "3 จุด", "S43/S32/S26", "T43/T32/T26"),
        ("ขา 4 → R1", "สาย 3 ท่อน", "L33", "Q43"),
        ("ขา 10 → R2", "สาย", "O32", "Q32"),
        ("ขา 8 → R3", "สาย 2 ท่อน", "O30", "Q26"),
        ("TB2 หัวส่ง TX1", "KF301 2 ขา", "T43", "T41"),
        ("TB3 หัวส่ง TX2", "KF301 2 ขา", "T32", "T30"),
        ("TB4 หัวส่ง TX3", "KF301 2 ขา", "T26", "T24"),
        ("GND หัวส่ง TX1", "สาย", "T41", "U41"),
        ("GND หัวส่ง TX2", "สาย", "T30", "U30"),
        ("GND หัวส่ง TX3", "สาย", "T24", "U24"),
    ])
    p.note(NX, 470, [
        "ทำไมต้องมี R อนุกรม 100Ω",
        "หัวส่งคือ C 2.4 nF ไม่ใช่ลำโพง",
        "ต่อตรง: พีค 333 mA (เกินพิกัด 6 เท่า)",
        "        กราวด์เด้ง 0.70V",
        "มี R:  พีค 34 mA · เด้ง 0.012V",
        "สัญญาณรับมีแค่ 1 mV — กราวด์เด้ง",
        "0.7V กลบภาครับทั้งระบบ",
        "เสียงไม่เบาลงเลย เพราะขอบที่ช้าลง",
        "เป็น 276 ns ยังเร็วกว่าคาบ 40 kHz",
        "(12500 ns) ถึง 45 เท่า",
    ], colour="#ae3ec9", bg="#f8f0fc", w=336)
    p.note(NX, 682, [
        "หัวส่งต่อกลับด้านได้ ไม่มีขั้ว",
        "TCT40-16T ไม่มีขั้วบวกลบ",
        "สลับสองขาแล้วเสียงเท่าเดิม",
        "(ต่างจาก C 10µF ที่มีขั้ว)",
        "ใช้สายแข็ง 25AWG ขันที่ KF301",
    ], colour="#1971c2", bg="#e7f5ff", w=336)
    return p


def main():
    panels = [panel_power(), panel_gates(), panel_outputs()]
    allused = {p.name: set(p.used) for p in panels}
    for p in panels:
        other = set().union(*(v for k, v in allused.items() if k != p.name))
        p.ghosts(other - p.used)
        nx = max(NX, 58 + (len(p.cols) - 1) * 26 + 94)
        p.note(nx, 806, [
            "วงประแดง = รูที่ผังอื่นใช้อยู่",
            "ทั้ง 3 ผังคือแผ่นเดียวกัน",
            "ห้ามบัดกรีหรือเดินสายทับรูที่มีวงประ",
            "และห้ามเดินสายเลียบตามคอลัมน์ที่มีวงประ",
        ], colour="#c92a2a", bg="#fff5f5", w=336)
        print("เขียน", p.save(OUT))


if __name__ == "__main__":
    main()
